rebeccajr/color-clock/docs/imgs/circuit/mux-examples__2024-06-23.pdf

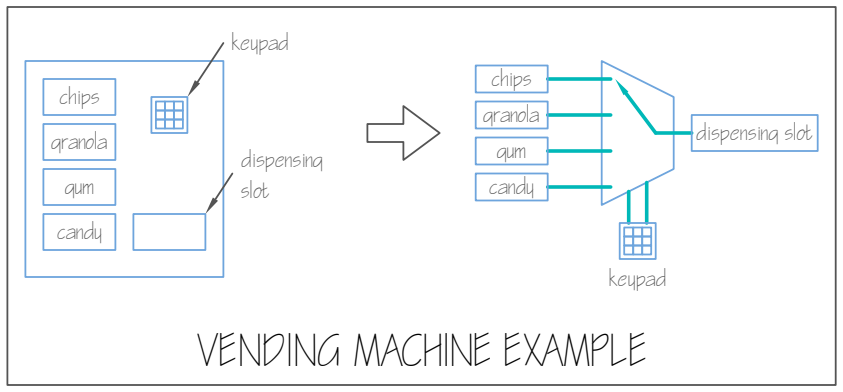
[picture p3: figure]
chips; granola; gum; candy; keypad; dispensing slot; chips granola gum candy; keypad VENDING MACHINE EXAMPLE

Arduino
control signals
common output pin | R
| G B

LED terminals

# RGB LED EXAMPLE
