rebeccajr/color-clock/docs/imgs/participant-ctrl/participant-ctrl-enclosure__2024-07-13.pdf

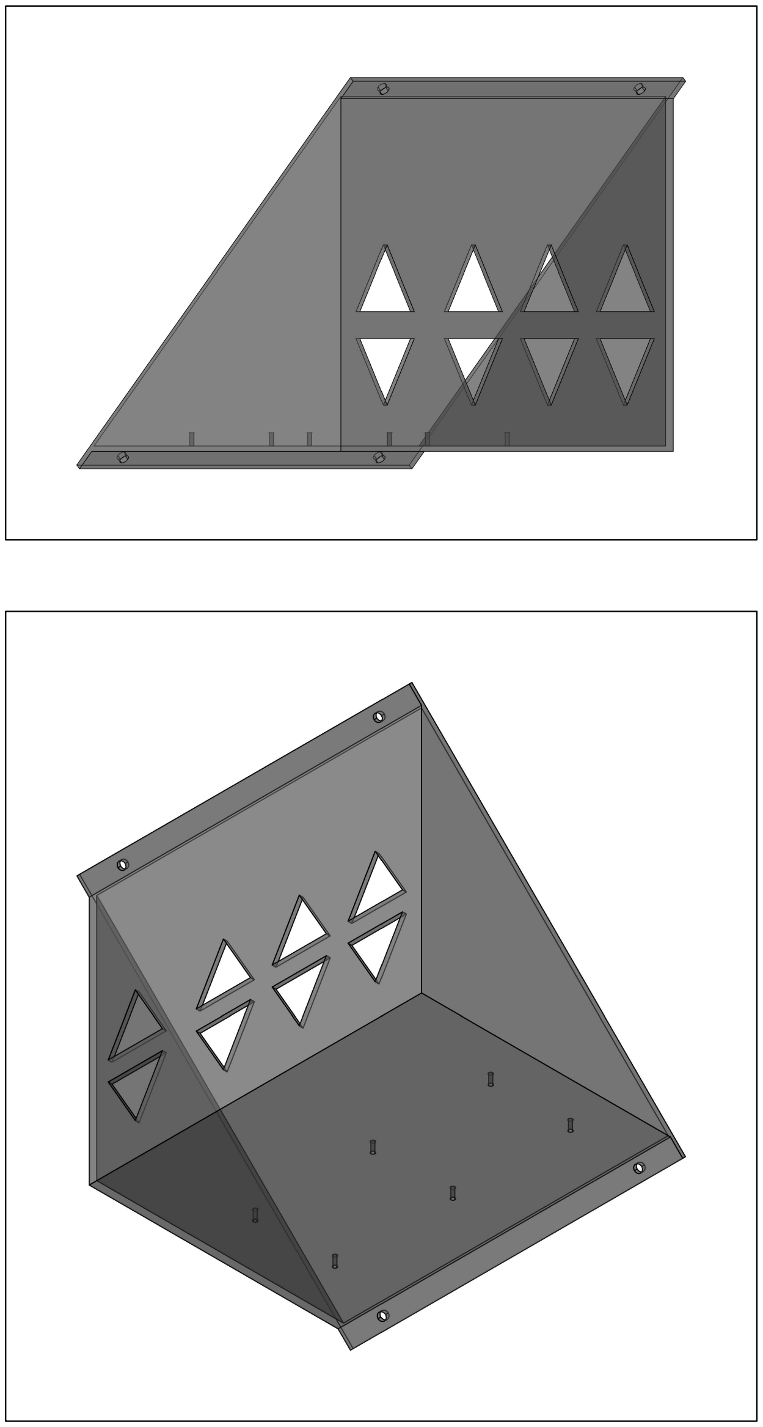
[picture p4: page 1]
