rebeccajr/color-clock/docs/imgs/participant-ctrl/participant-intfc__2024-07-04.pdf

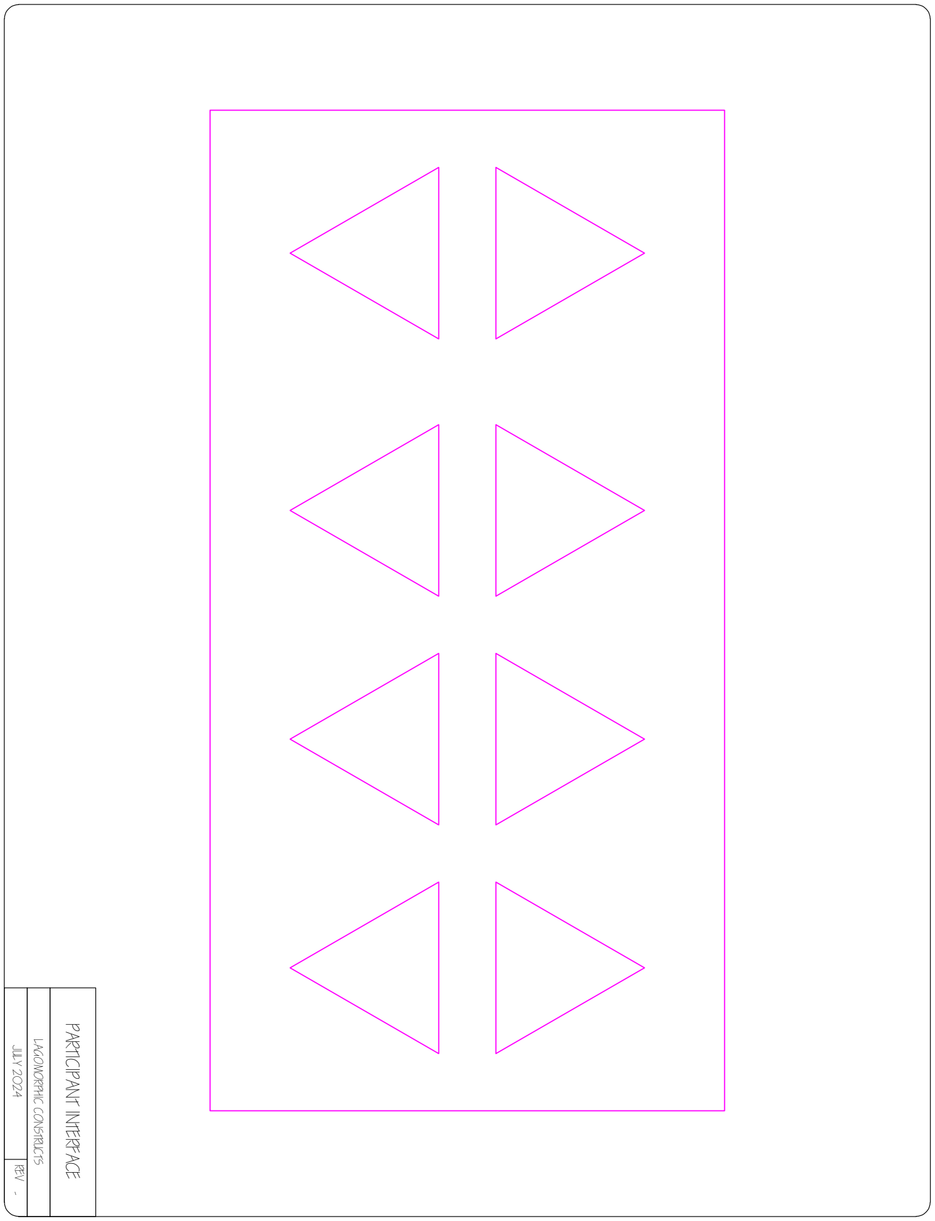
[picture p5: figure]

REV LAGOMORPHIC CONSTRUCTS - JULY 2024 PARTICIPANT INTERFACE
