rebeccajr/color-clock/docs/datasheets/Common-Anode-Singal-Input.jpg

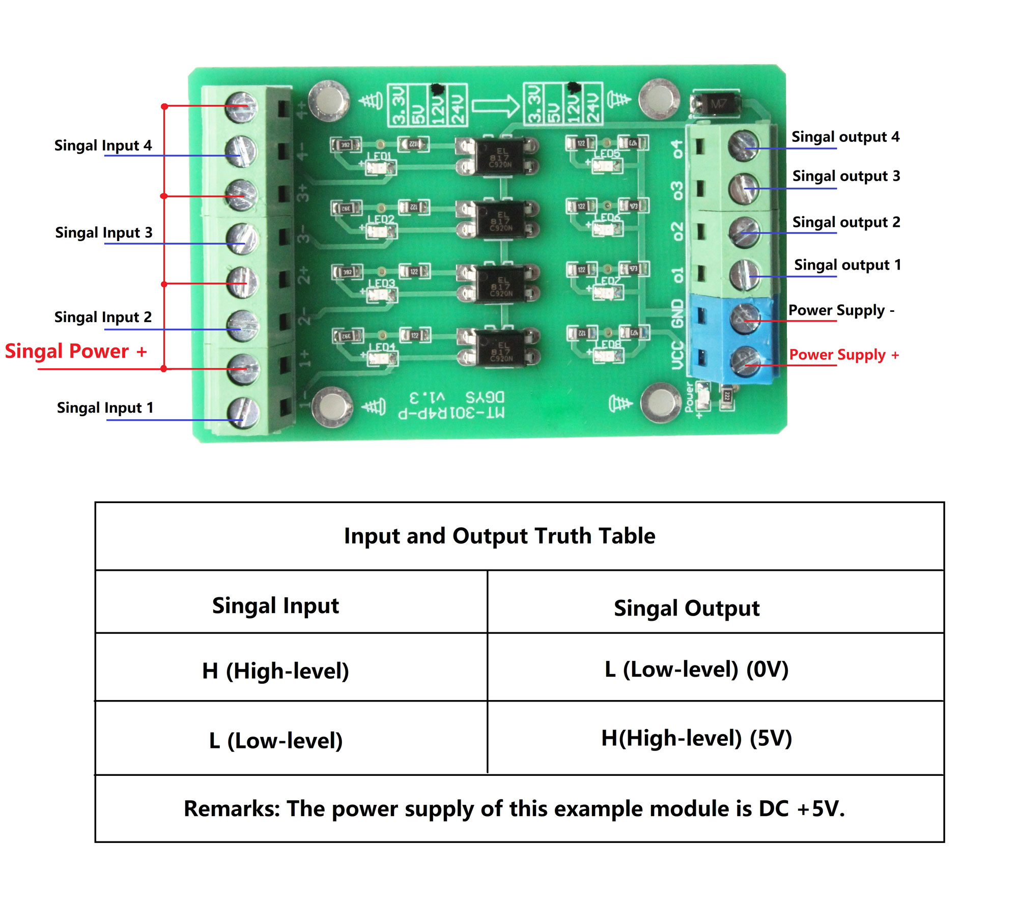
docs/datasheets/Common-Anode-Singal-Input.jpg
