rebeccajr/color-clock/docs/datasheets/Common-Cathode-Singal-Input.jpg

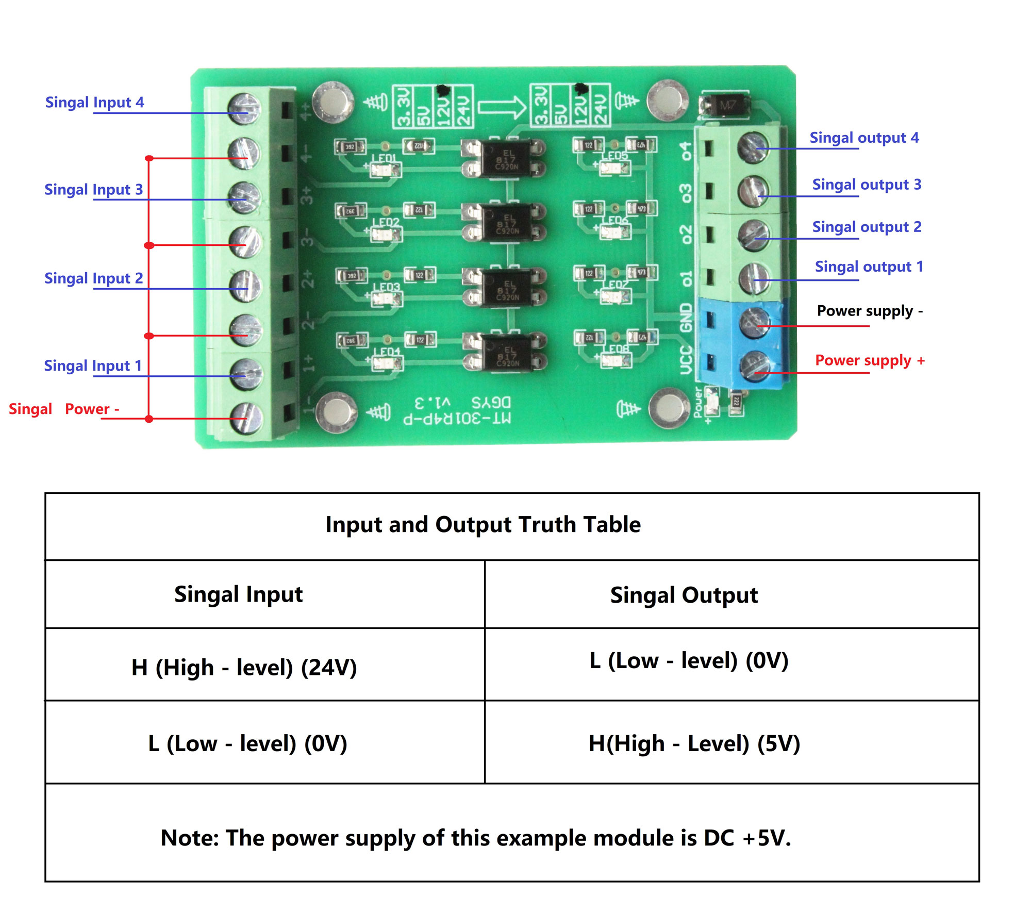
docs/datasheets/Common-Cathode-Singal-Input.jpg
