rebeccajr/color-clock/docs/imgs/block-diagrams/color-clock-block.png

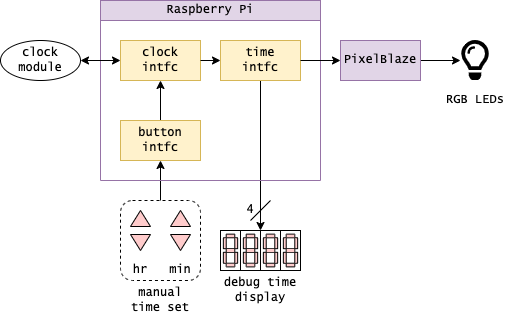
docs/imgs/block-diagrams/color-clock-block.png
