rebeccajr/color-clock/docs/imgs/block-diagrams/color-clock-block_2022-04.png

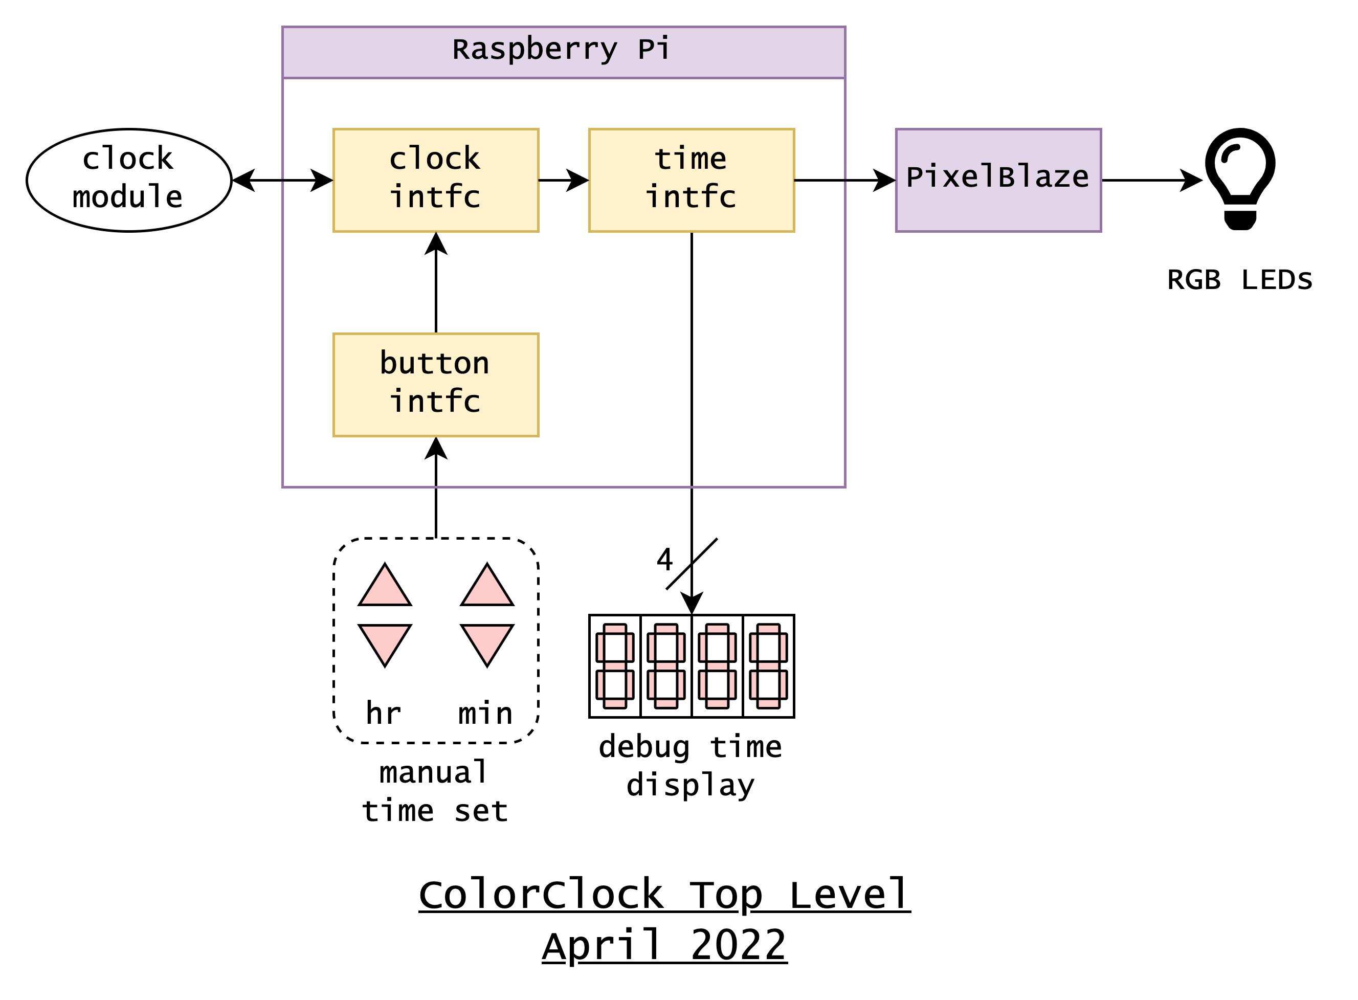
docs/imgs/block-diagrams/color-clock-block_2022-04.png
