rebeccajr/color-clock/docs/imgs/block-diagrams/color-clock-block_2024-02-03.png

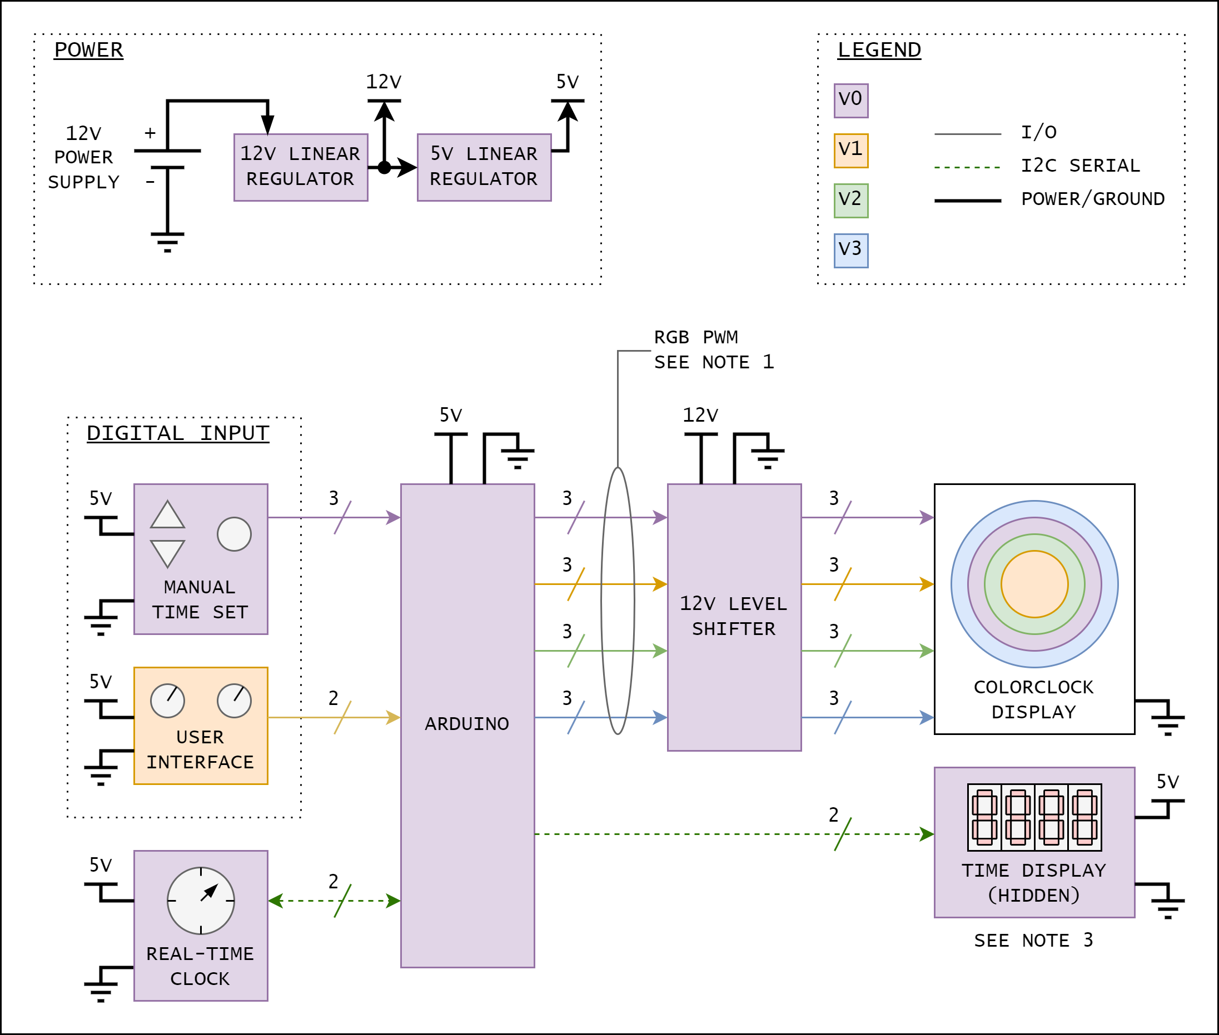
docs/imgs/block-diagrams/color-clock-block_2024-02-03.png
