rebeccajr/color-clock/docs/imgs/circuit/circuit-board-full__2024-07-20.png

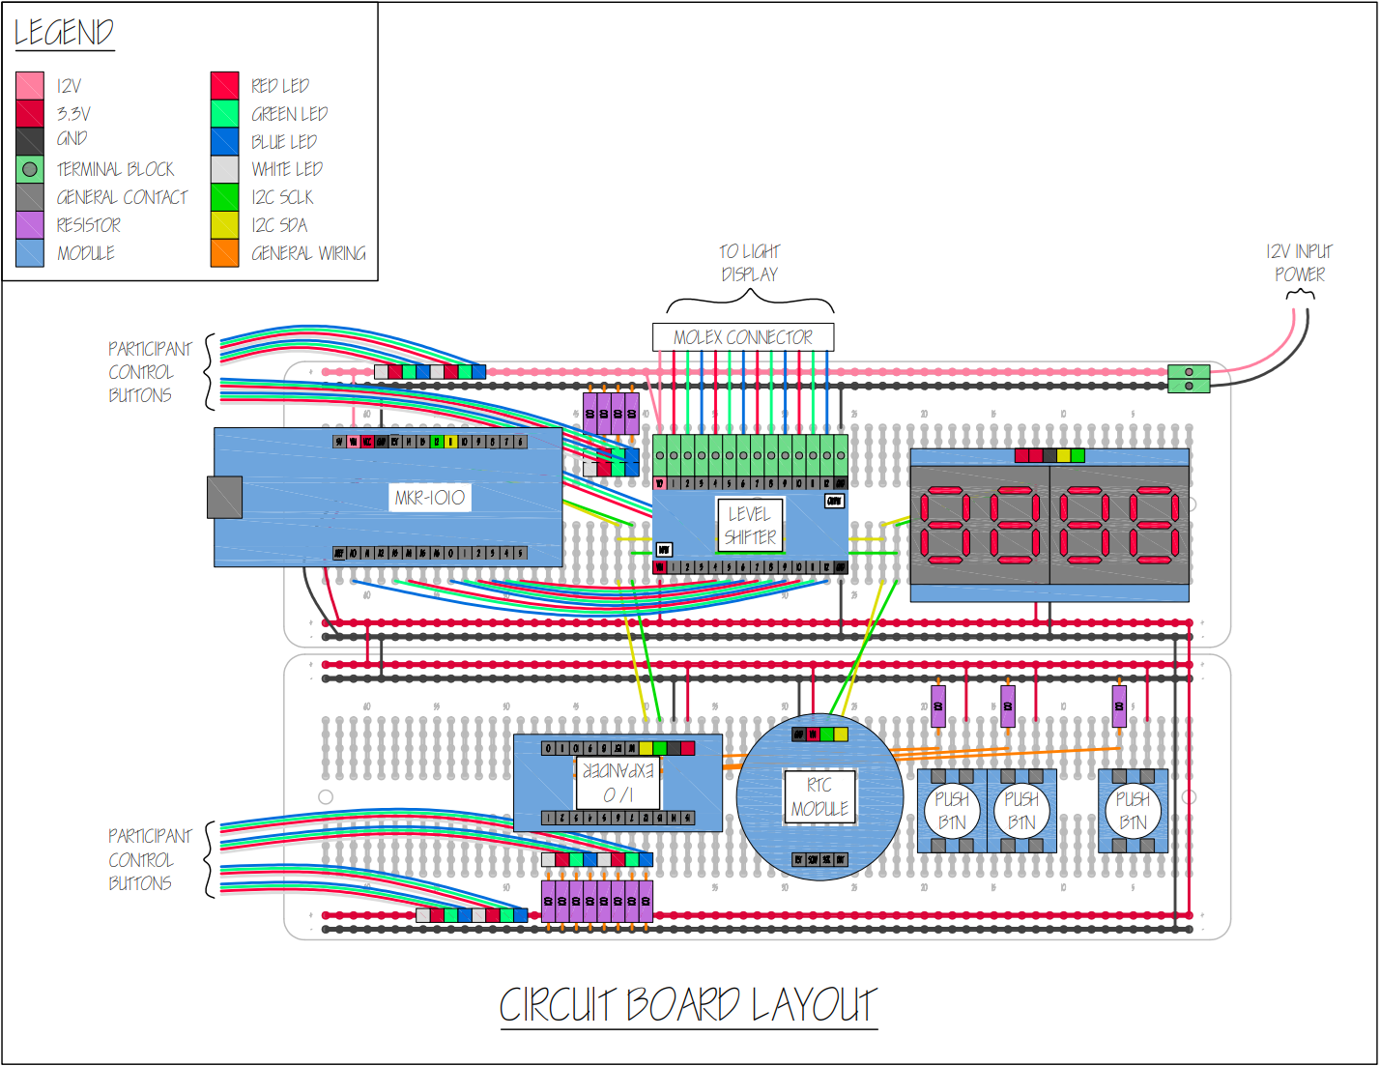
docs/imgs/circuit/circuit-board-full__2024-07-20.png
