rebeccajr/color-clock/docs/imgs/circuit/circuit-board-wire__2024-07-20.png

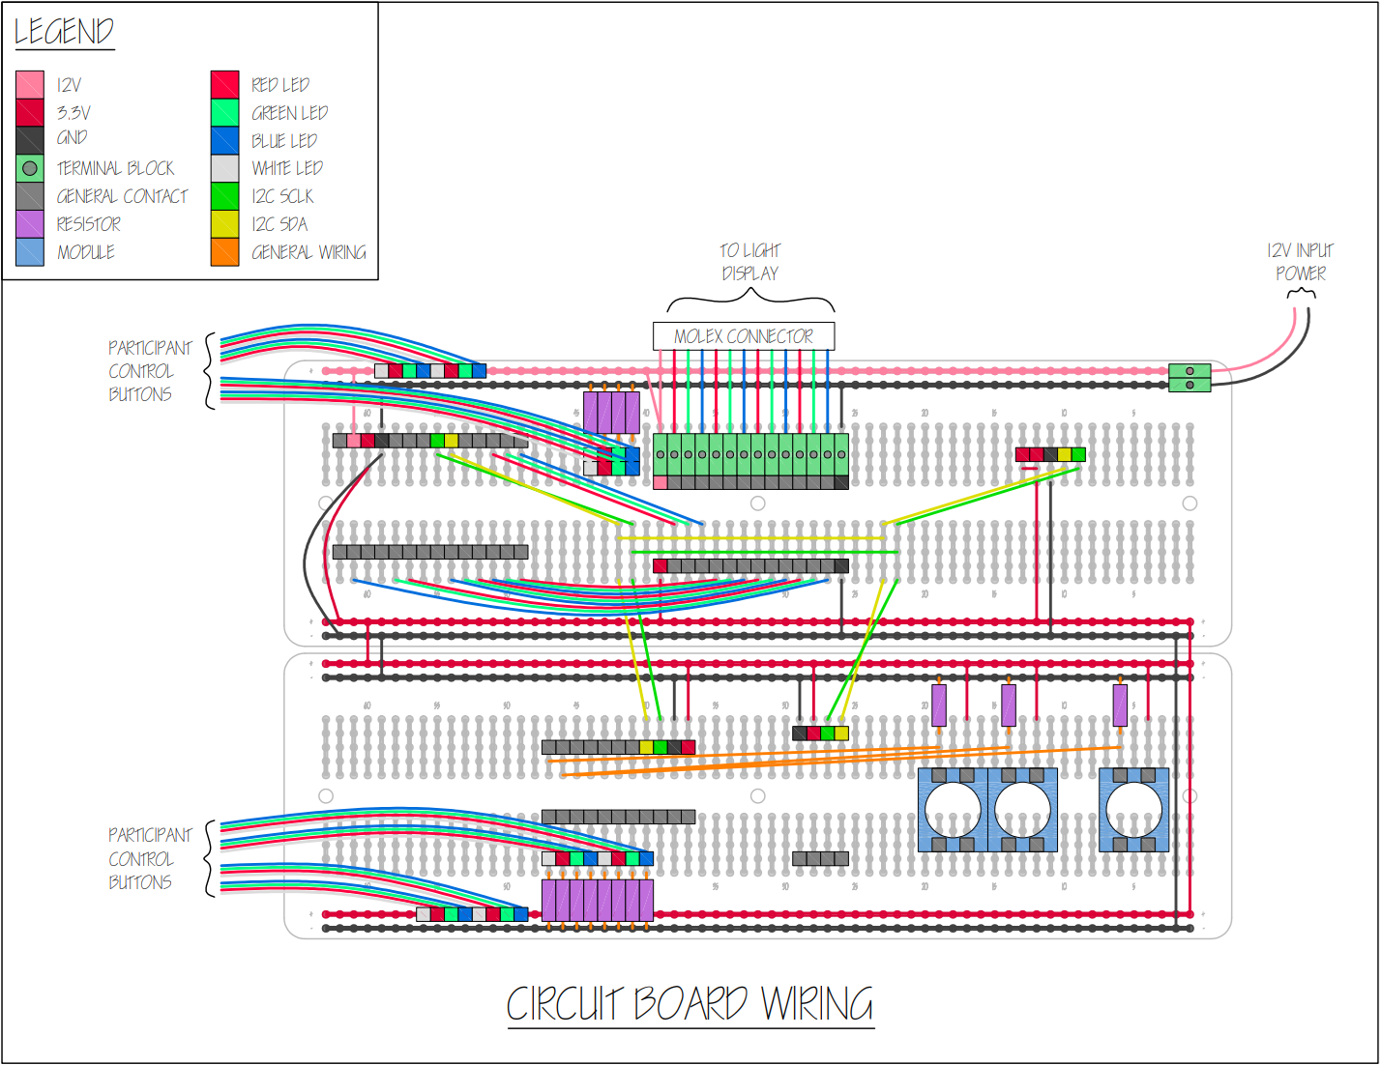
docs/imgs/circuit/circuit-board-wire__2024-07-20.png
