rebeccajr/color-clock/docs/imgs/circuit/color-clock-circuit_2022-05-15.png

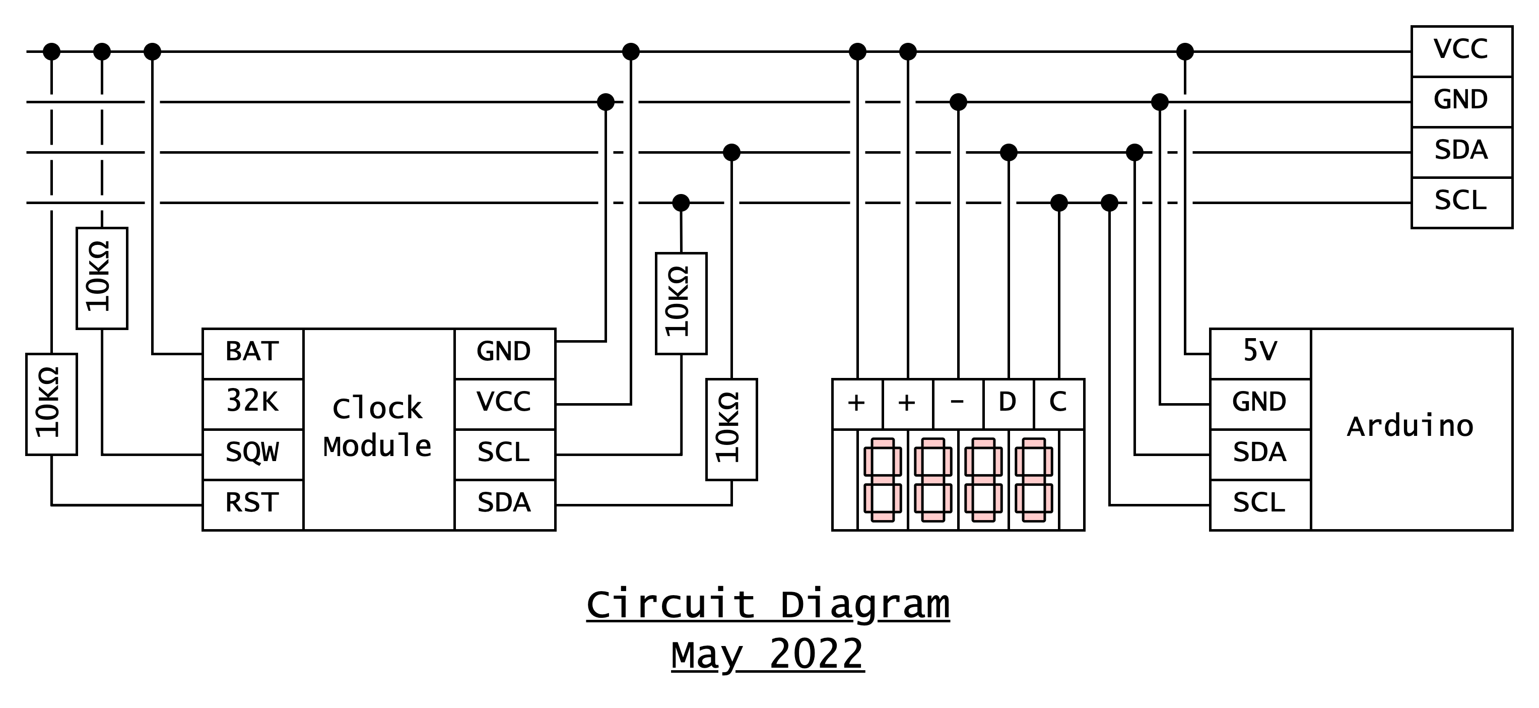
docs/imgs/circuit/color-clock-circuit_2022-05-15.png
