rebeccajr/color-clock/docs/imgs/circuit/mux-rgb__2024-06-23.png

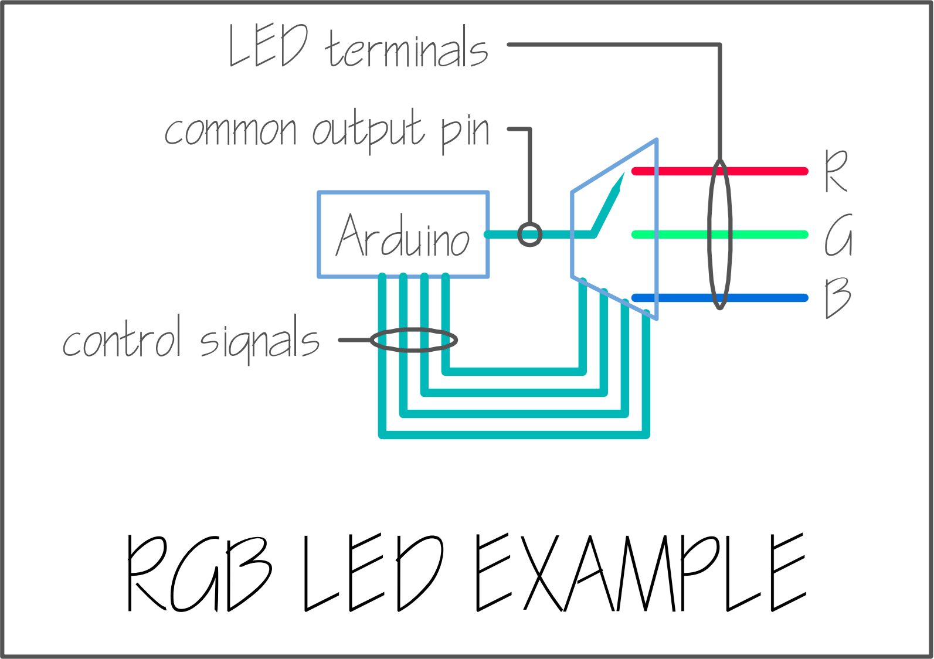
docs/imgs/circuit/mux-rgb__2024-06-23.png
