rebeccajr/color-clock/docs/imgs/circuit/mux-vending-machine__2024-06-23.png

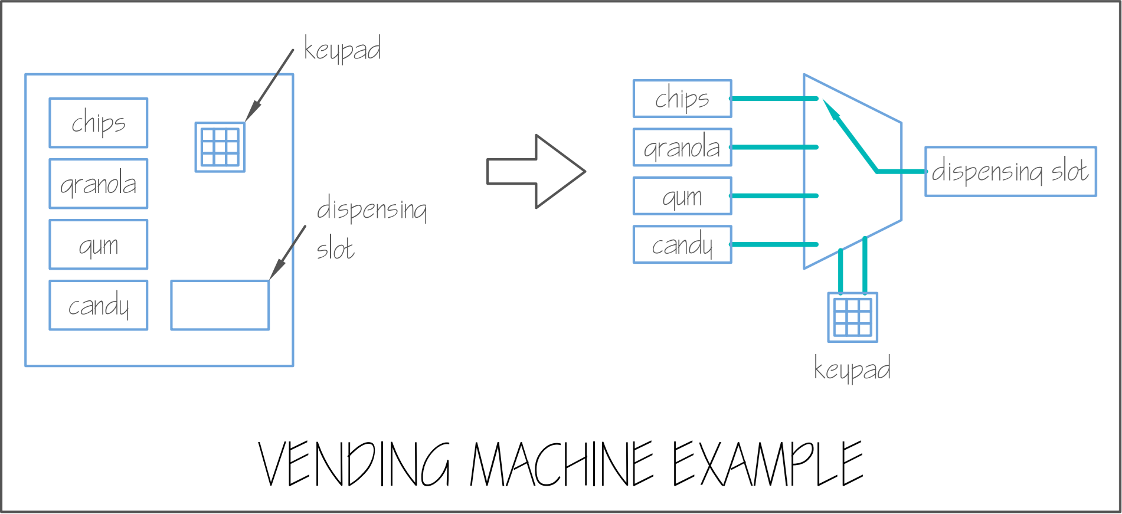
docs/imgs/circuit/mux-vending-machine__2024-06-23.png
