rebeccajr/color-clock/docs/imgs/light-display/light-display-v02_2024-03-06.png

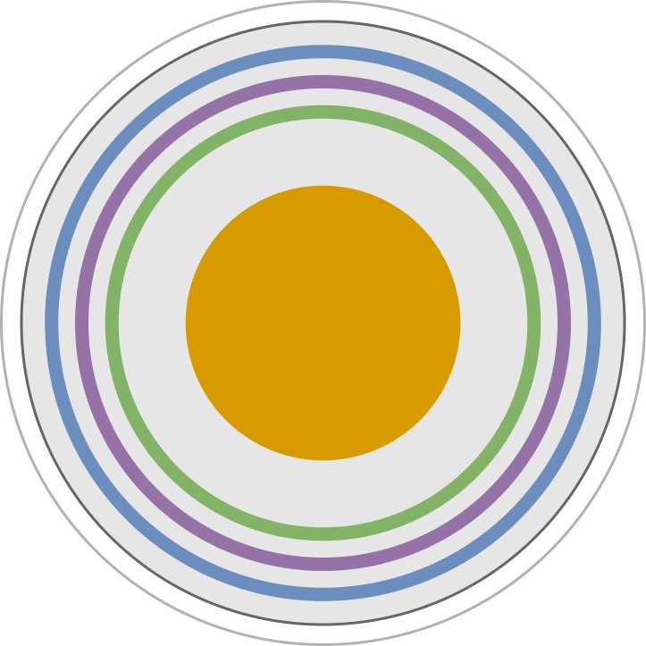
docs/imgs/light-display/light-display-v02_2024-03-06.png
