rebeccajr/color-clock/docs/imgs/light-display/light-display_2024-02-23.png

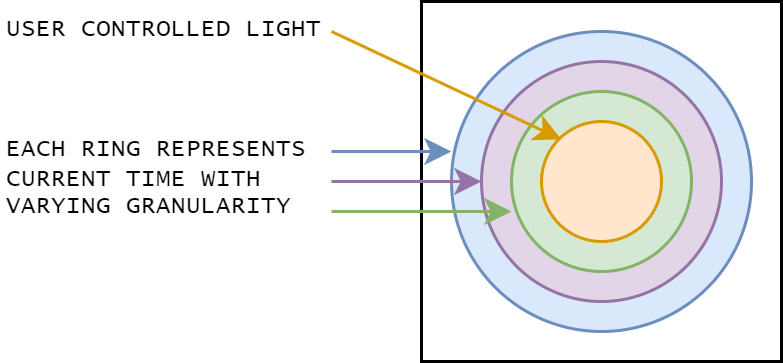
docs/imgs/light-display/light-display_2024-02-23.png
