rebeccajr/color-clock/docs/imgs/other/ascii-bunny.png

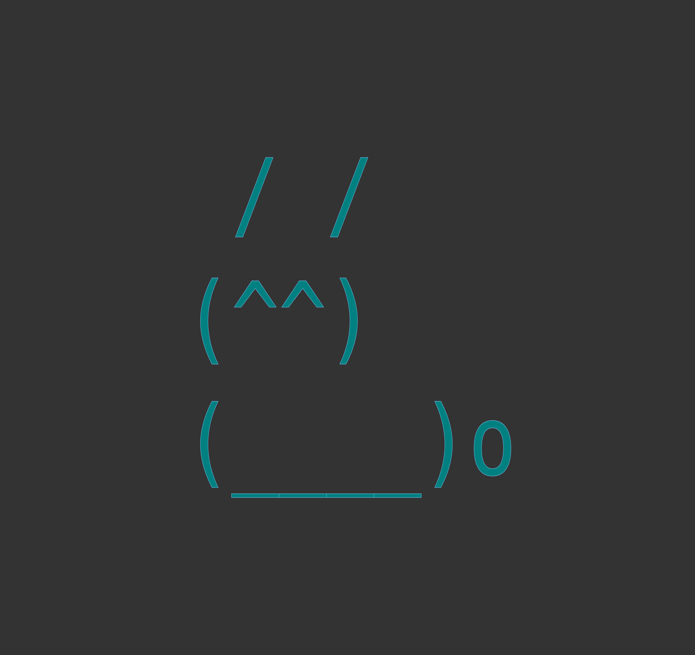
docs/imgs/other/ascii-bunny.png
