rebeccajr/color-clock/docs/imgs/participant-ctrl/participant-ctrl-0__2024-07-13.png

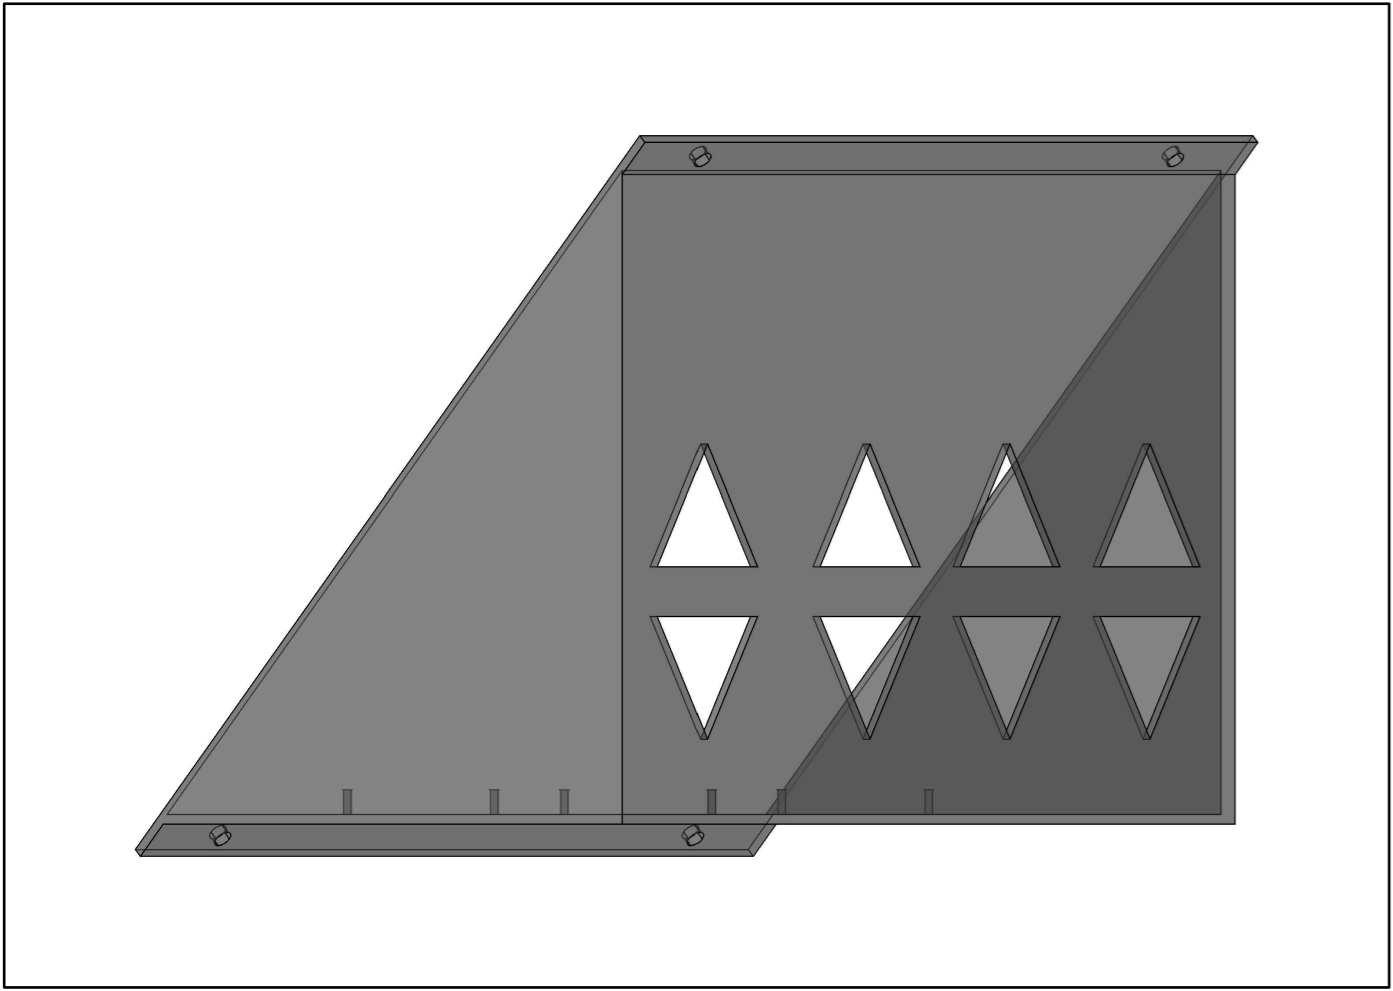
docs/imgs/participant-ctrl/participant-ctrl-0__2024-07-13.png
