rebeccajr/color-clock/docs/imgs/participant-ctrl/user-interface-v2_2024-02-23.png

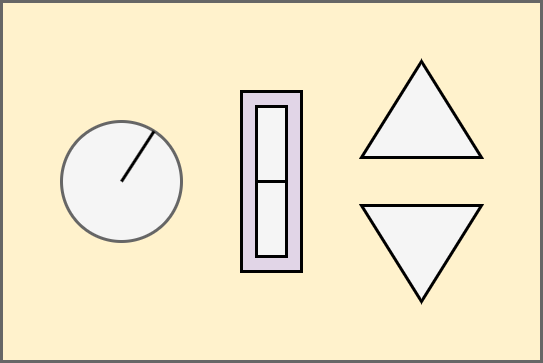
docs/imgs/participant-ctrl/user-interface-v2_2024-02-23.png
