rebeccajr/color-clock/docs/imgs/participant-ctrl/user-interface-v3_2024-02-23.png

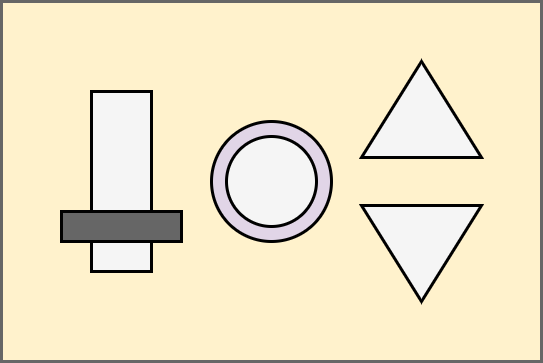
docs/imgs/participant-ctrl/user-interface-v3_2024-02-23.png
