rebeccajr/color-clock/docs/imgs/photos/IMG_2031.JPEG

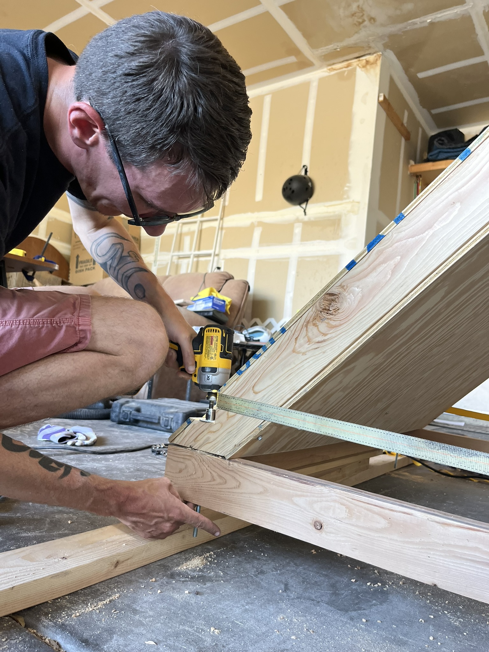
docs/imgs/photos/IMG_2031.JPEG
