rebeccajr/color-clock/docs/imgs/photos/IMG_2035.JPEG

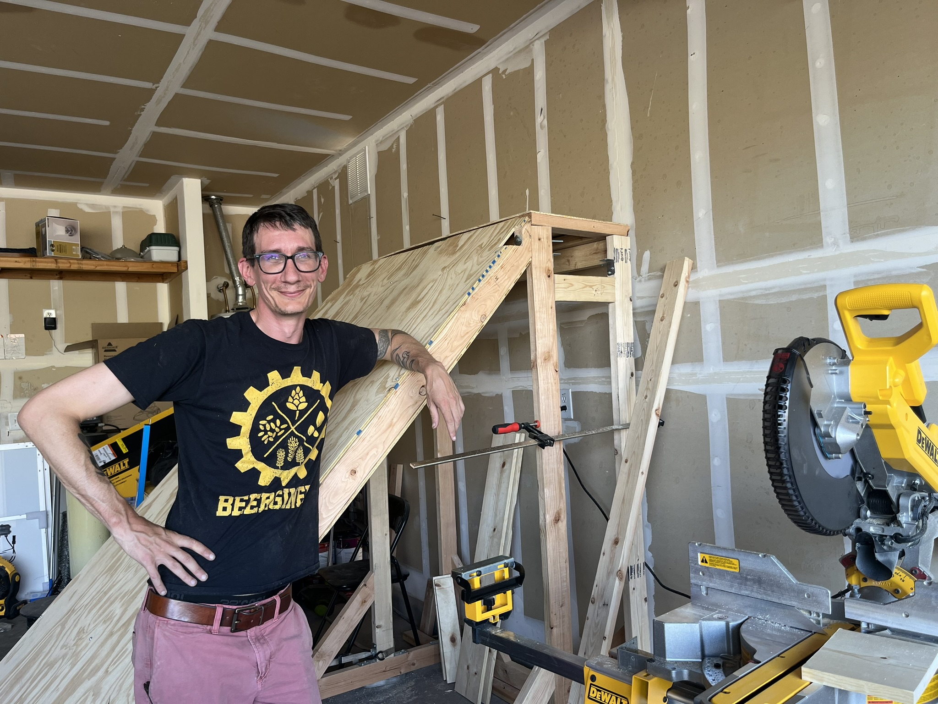
docs/imgs/photos/IMG_2035.JPEG
