rebeccajr/color-clock/docs/imgs/photos/IMG_2041.JPEG

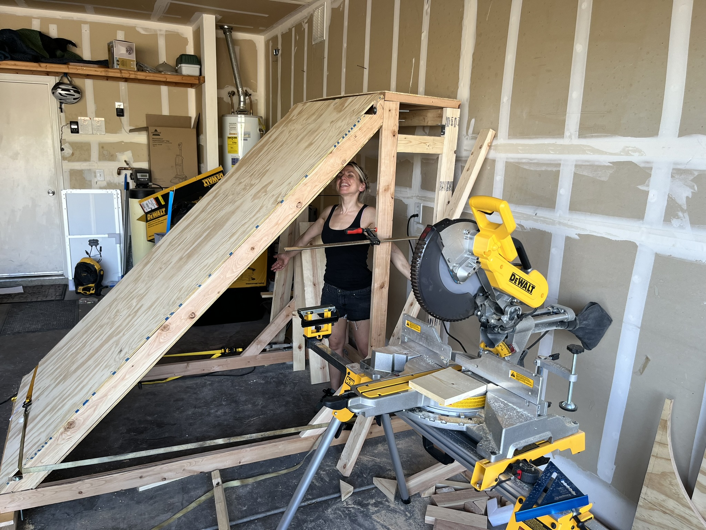
docs/imgs/photos/IMG_2041.JPEG
