rebeccajr/color-clock/docs/imgs/photos/IMG_2043.JPEG

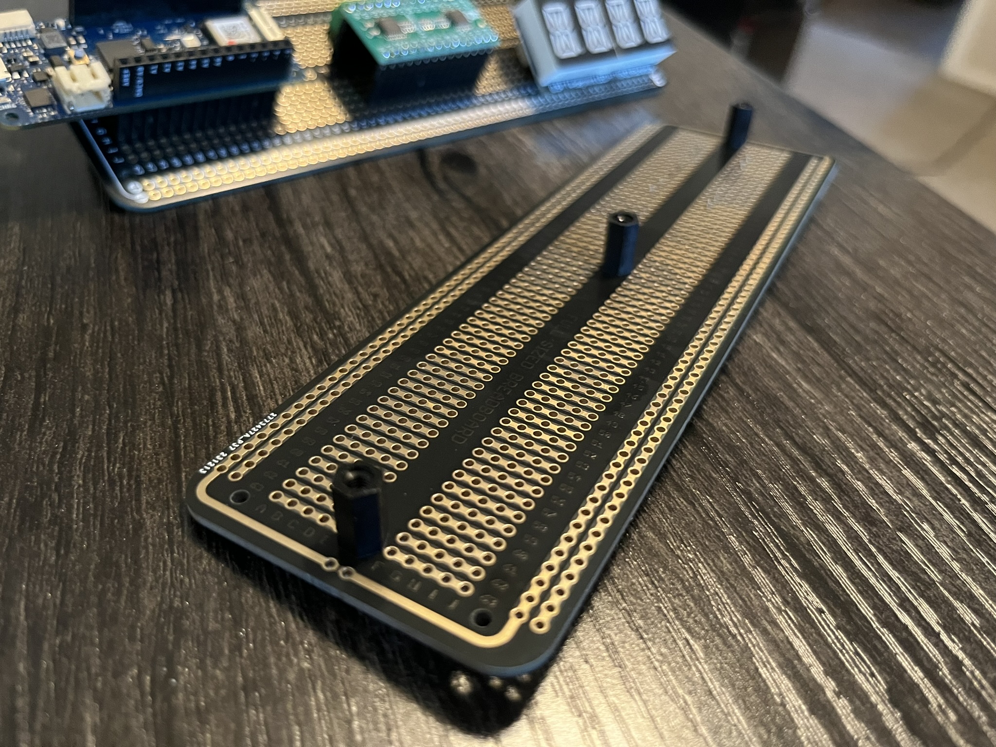
docs/imgs/photos/IMG_2043.JPEG
