rebeccajr/color-clock/docs/imgs/photos/structure-v1-photo_2024-03-02.jpg

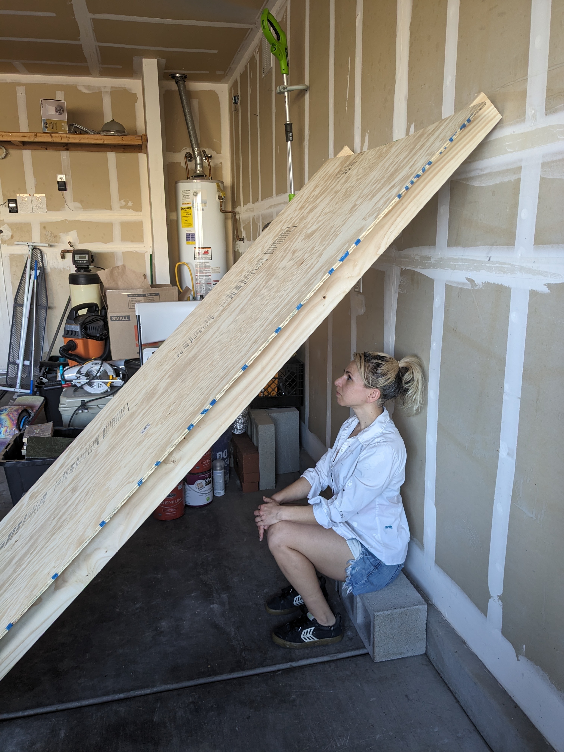
docs/imgs/photos/structure-v1-photo_2024-03-02.jpg
