rebeccajr/color-clock/docs/imgs/photos/time-display_2024-03-20.jpg

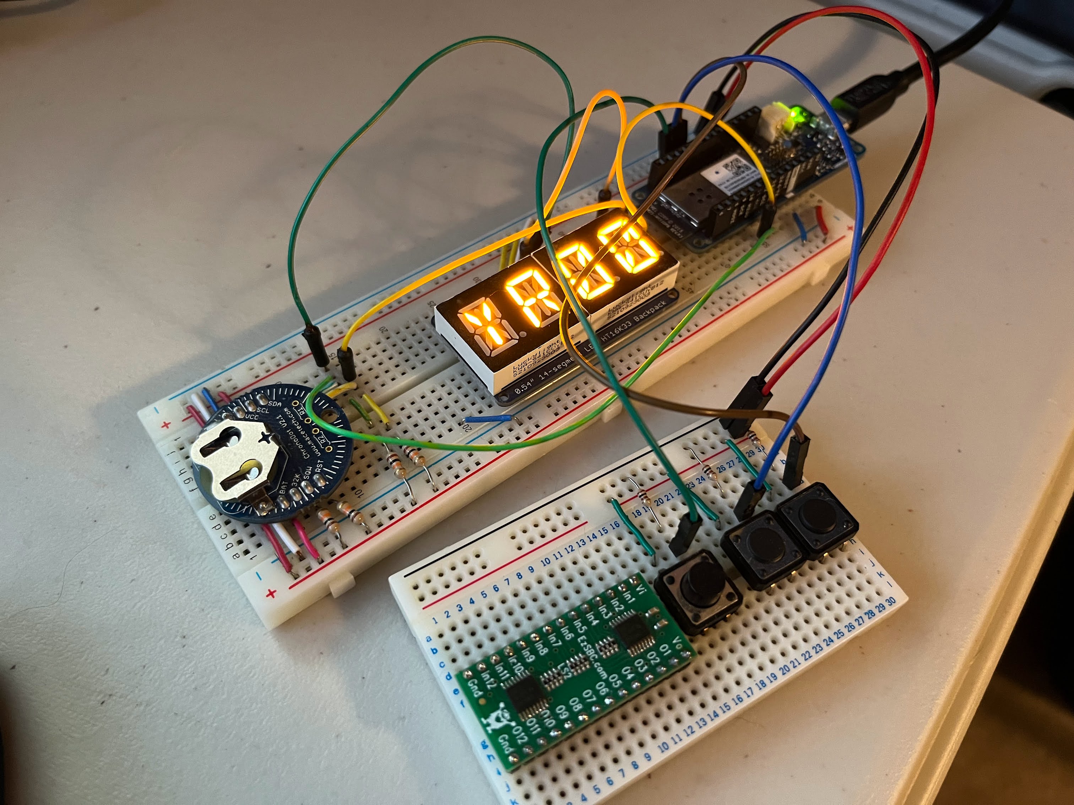
docs/imgs/photos/time-display_2024-03-20.jpg
