rebeccajr/color-clock/docs/imgs/structure/color-clock-overall-v02__2024-03-06.jpg

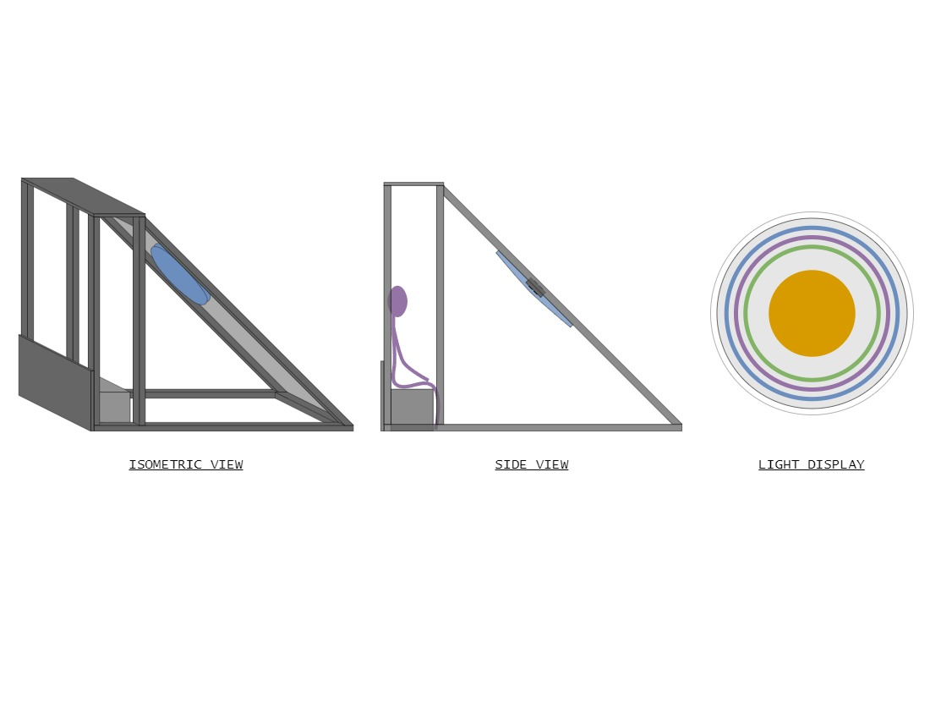
docs/imgs/structure/color-clock-overall-v02__2024-03-06.jpg
