rebeccajr/color-clock/docs/imgs/structure/color-clock-physical-structure-v0.jpg

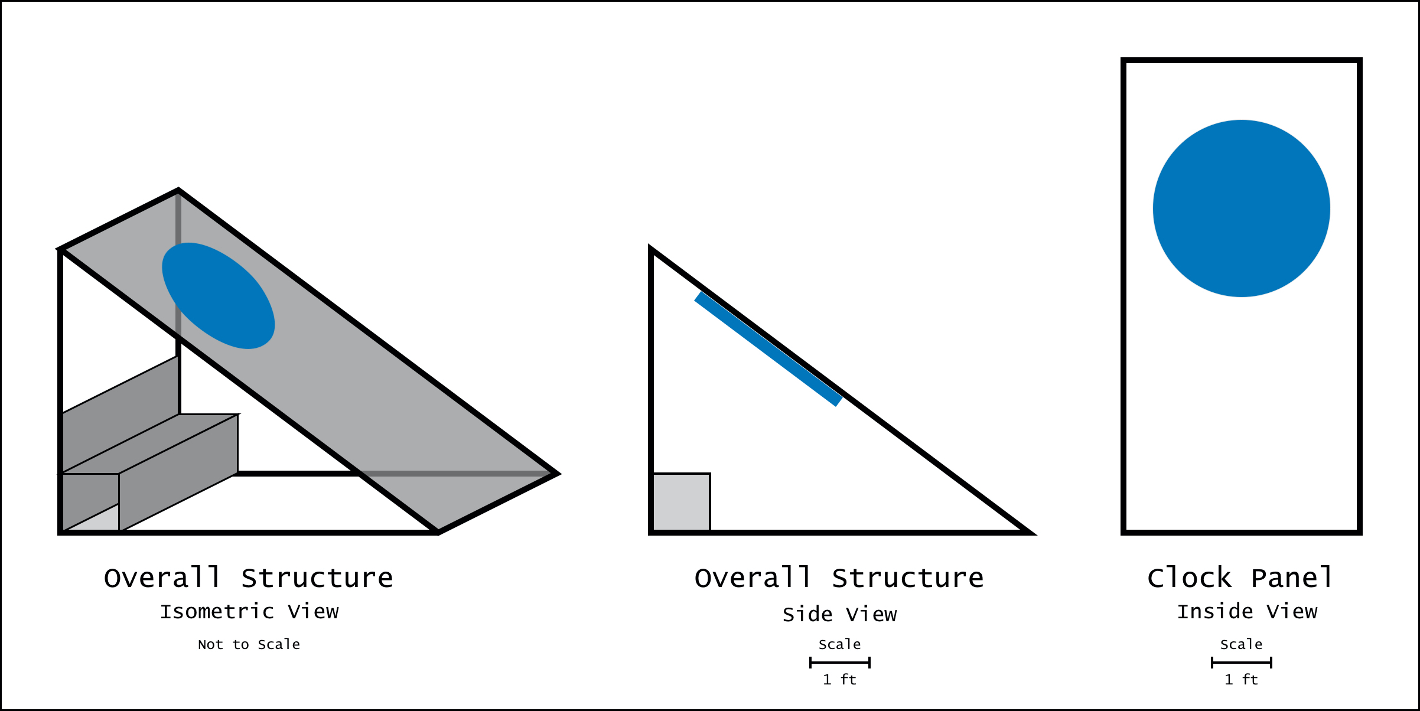
docs/imgs/structure/color-clock-physical-structure-v0.jpg
