rebeccajr/color-clock/docs/imgs/structure/structure-v2-cad_2024-03-06.png

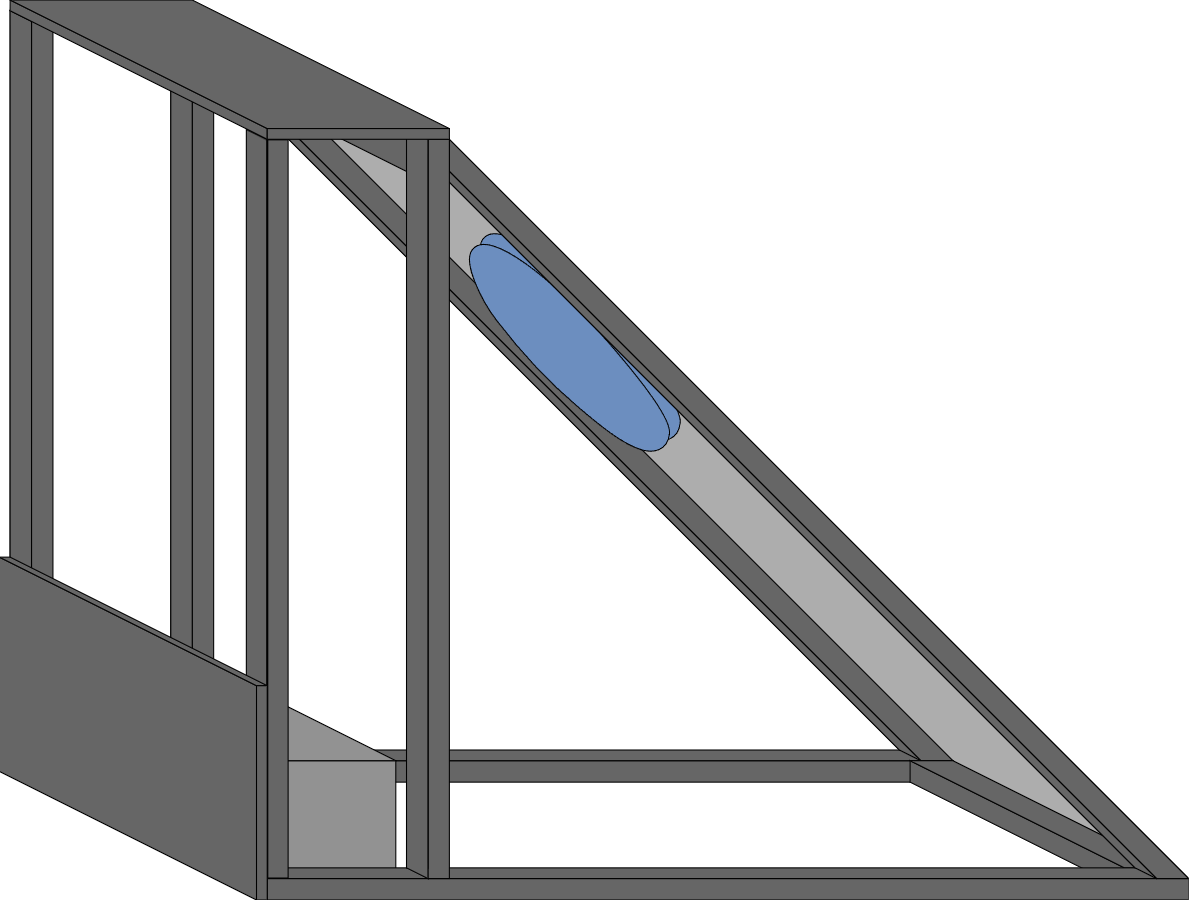
docs/imgs/structure/structure-v2-cad_2024-03-06.png
