rebeccajr/color-clock/docs/imgs/structure/structure-v2-sketch_2024-03-20.png

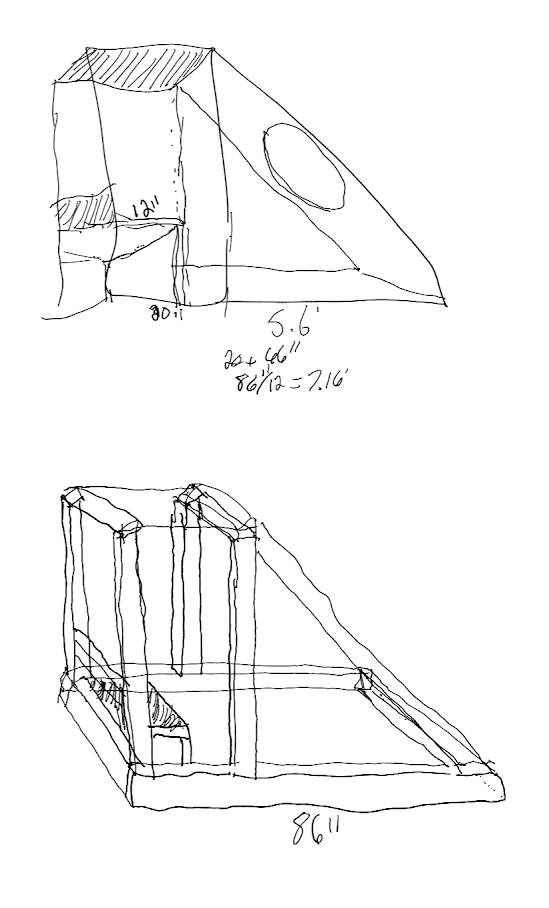
docs/imgs/structure/structure-v2-sketch_2024-03-20.png
