rebeccajr/color-clock/docs/slide-decks/2024-08-10__demo/_photos-demo/IMG_2125.jpeg

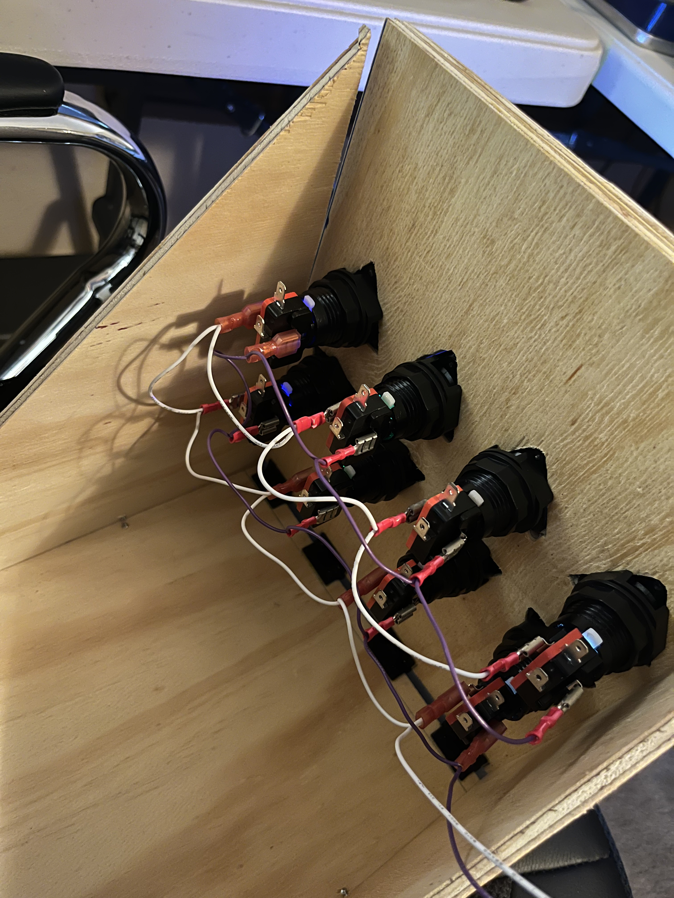
docs/slide-decks/2024-08-10__demo/_photos-demo/IMG_2125.jpeg
