rebeccajr/color-clock/docs/slide-decks/2024-08-10__demo/_png/02__light-color.png

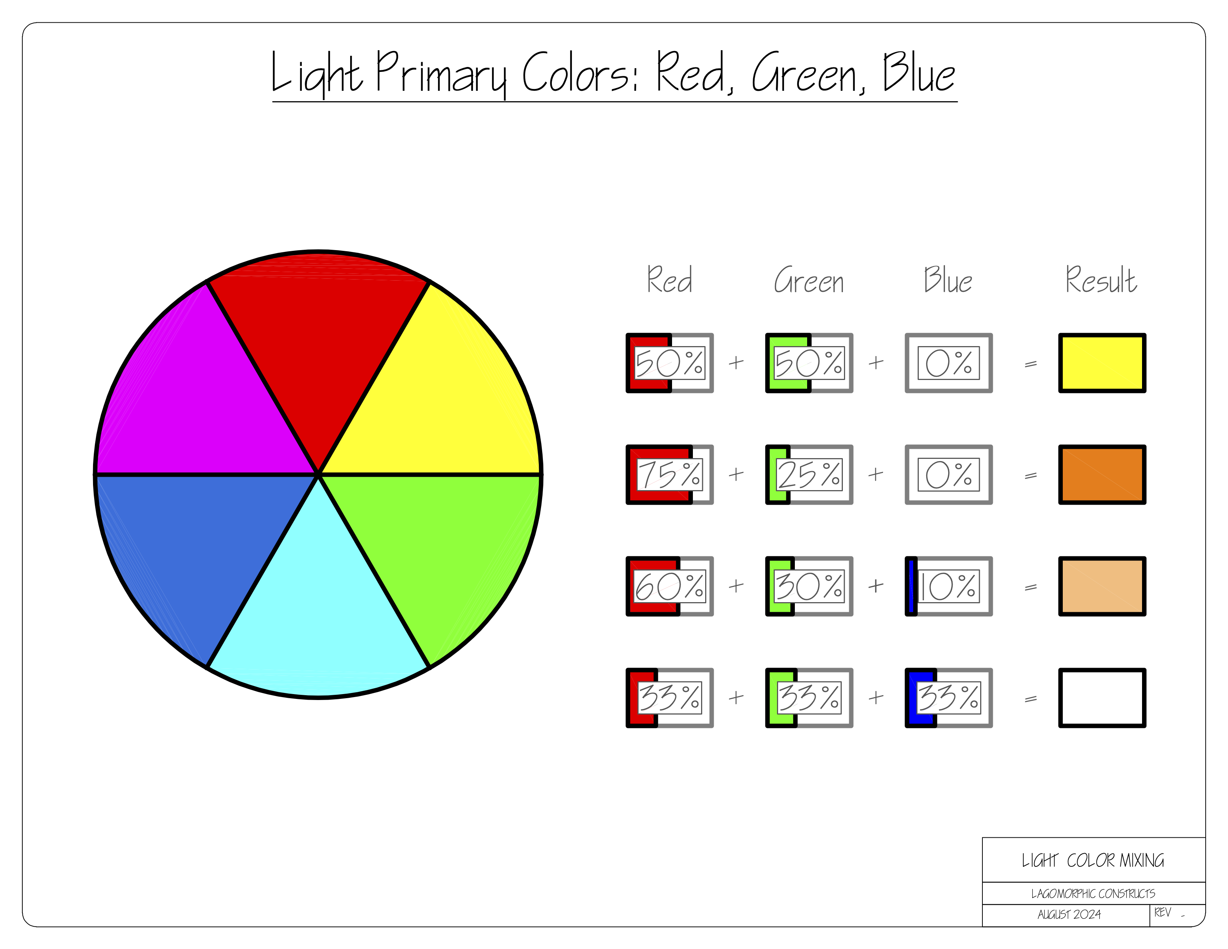
docs/slide-decks/2024-08-10__demo/_png/02__light-color.png
