rebeccajr/color-clock/docs/slide-decks/2024-08-10__demo/_png/03__rgb-led-common-anode.png

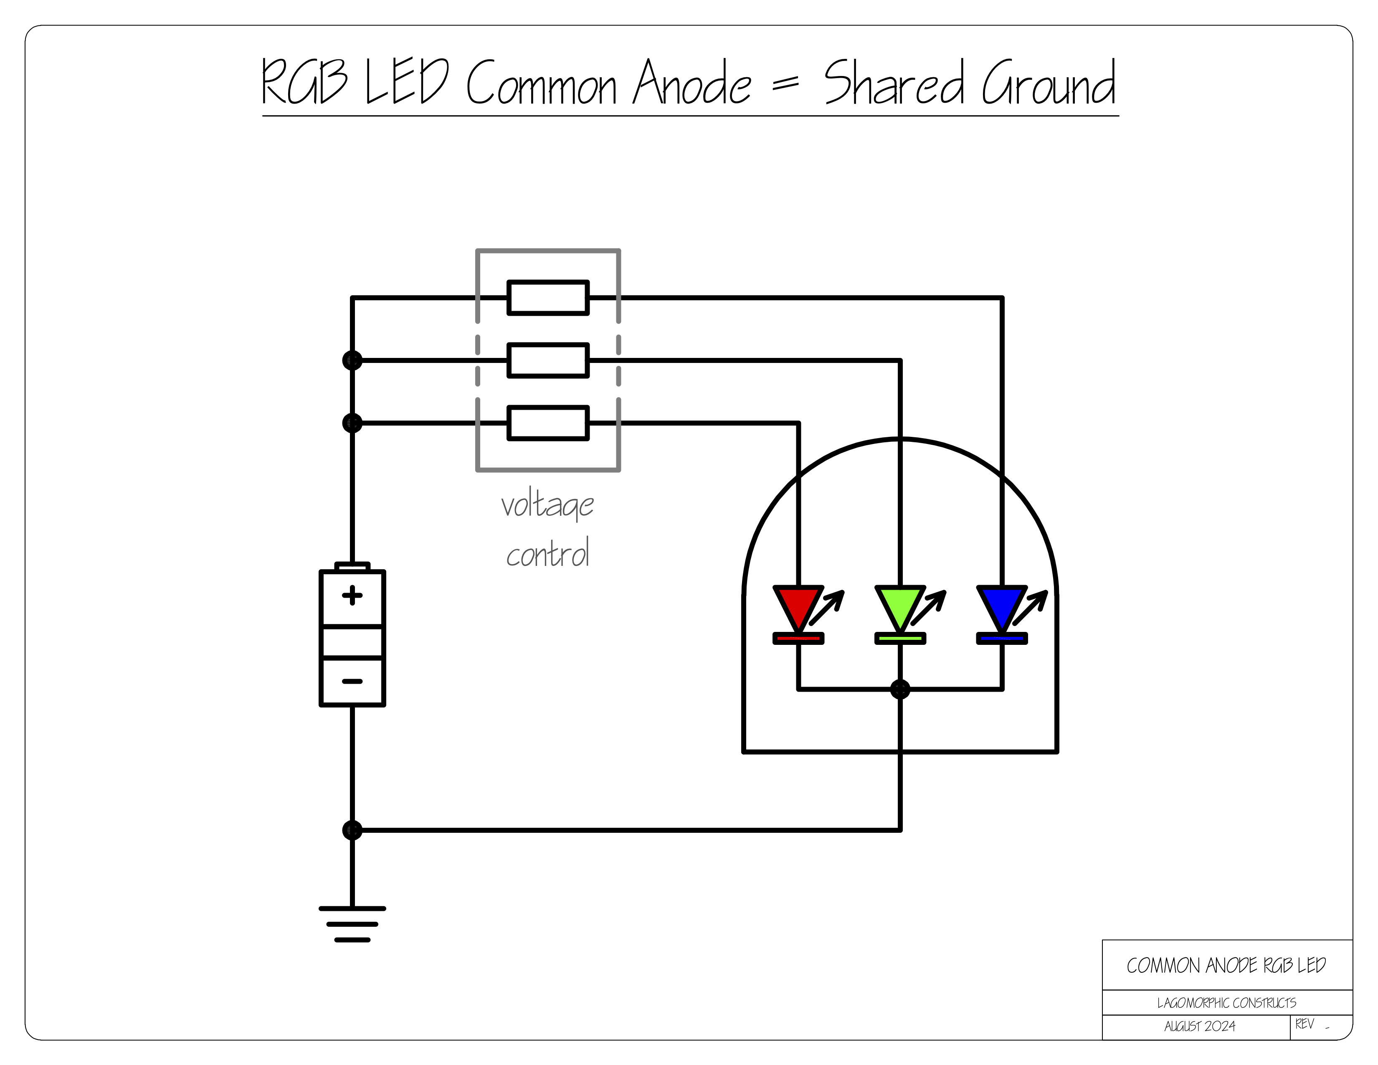
docs/slide-decks/2024-08-10__demo/_png/03__rgb-led-common-anode.png
