rebeccajr/color-clock/docs/slide-decks/2024-08-10__demo/_png/04__rgb-color-mix.png

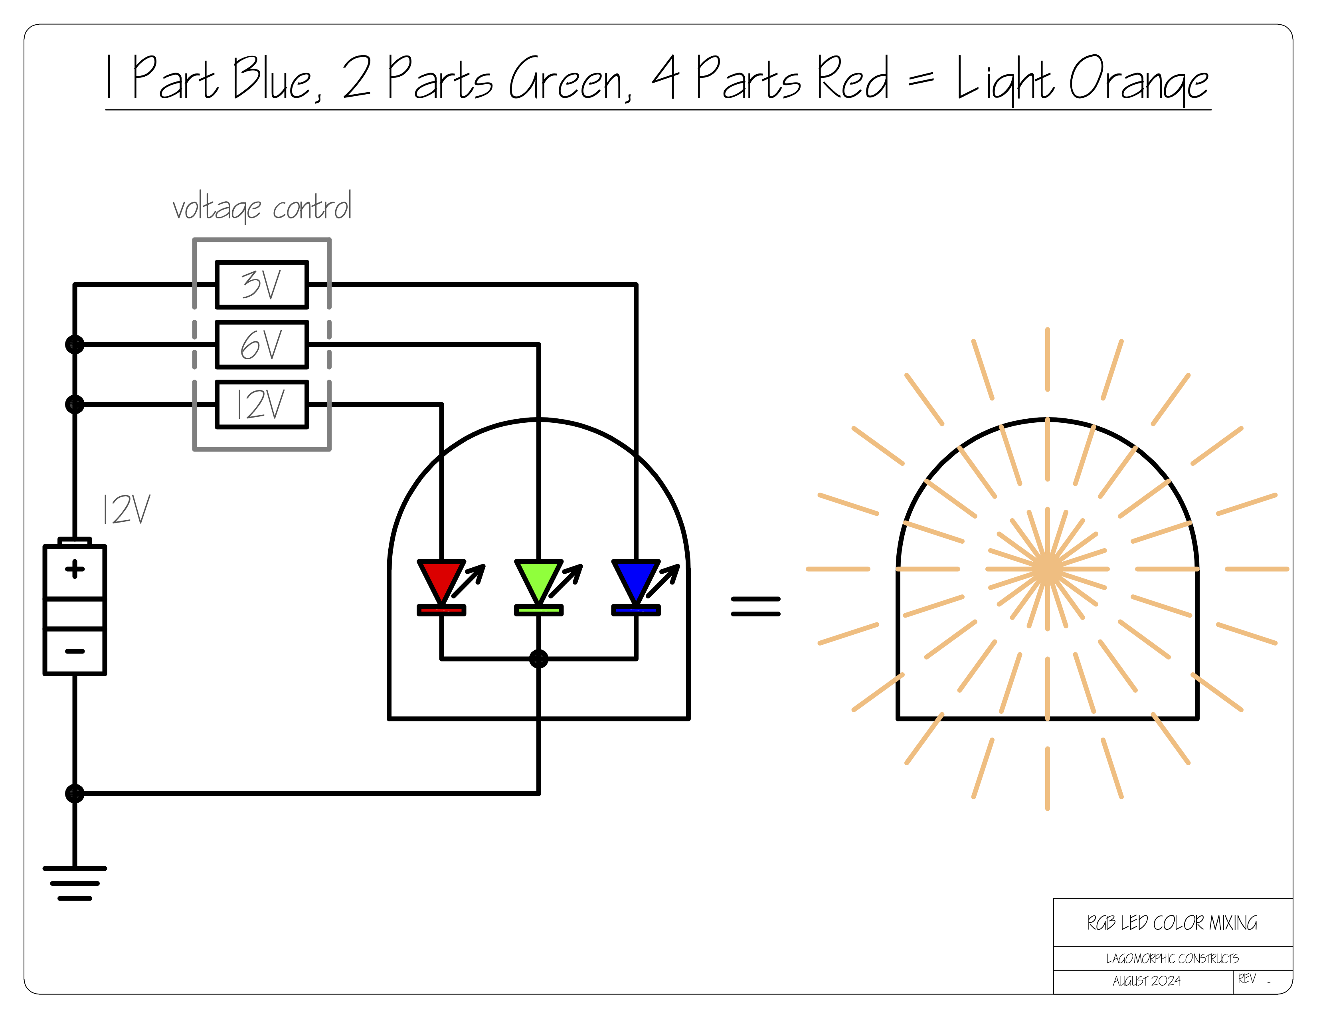
docs/slide-decks/2024-08-10__demo/_png/04__rgb-color-mix.png
