rebeccajr/color-clock/docs/slide-decks/2024-08-10__demo/_png/05__level-shifter.png

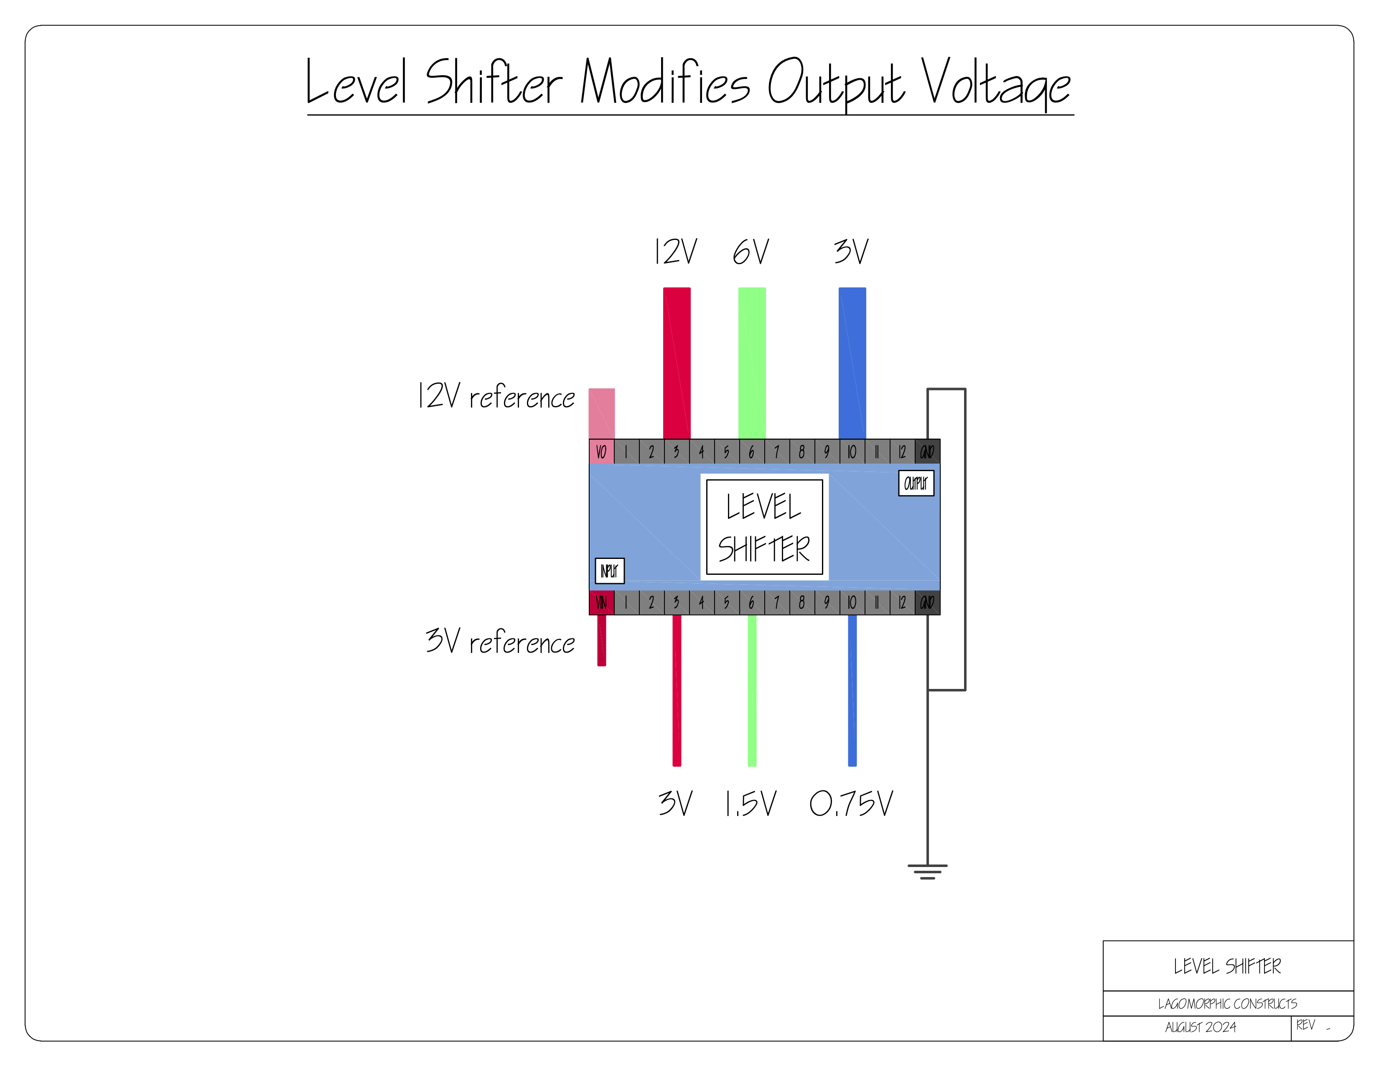
docs/slide-decks/2024-08-10__demo/_png/05__level-shifter.png
