rebeccajr/color-clock/docs/imgs/acad/_stl/box-divider-6in-v0__2024-08-04.stl

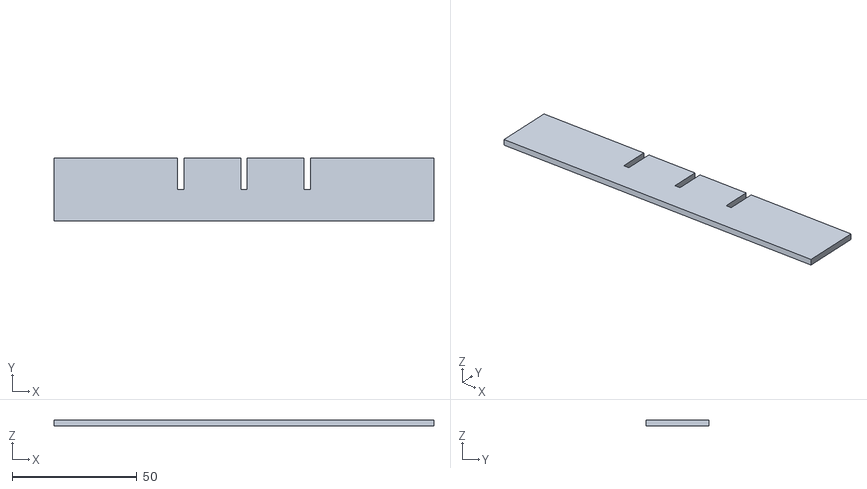
[picture p65: CAD file, 2024-11-28]
docs/imgs/acad/_stl/box-divider-6in-v0__2024-08-04.stl
152.4 x 25.4 x 2.54
