rebeccajr/color-clock/docs/imgs/acad/_stl/enclosure-front-v0__2024-07-29.stl

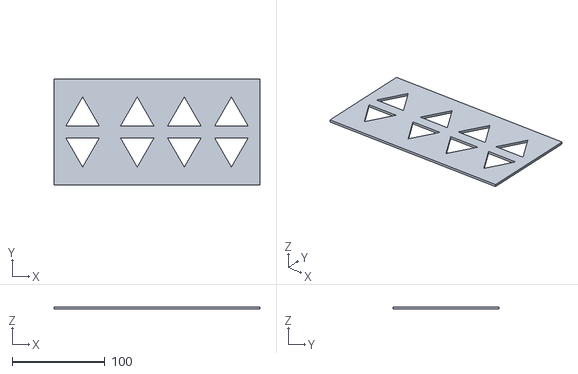
[picture p66: CAD file, 2024-11-28]
docs/imgs/acad/_stl/enclosure-front-v0__2024-07-29.stl
222.2 x 114.3 x 2.54
