rebeccajr/color-clock/docs/imgs/circuit/solderless-breadboard-layout-rev--no-anno__2024-05-28.png

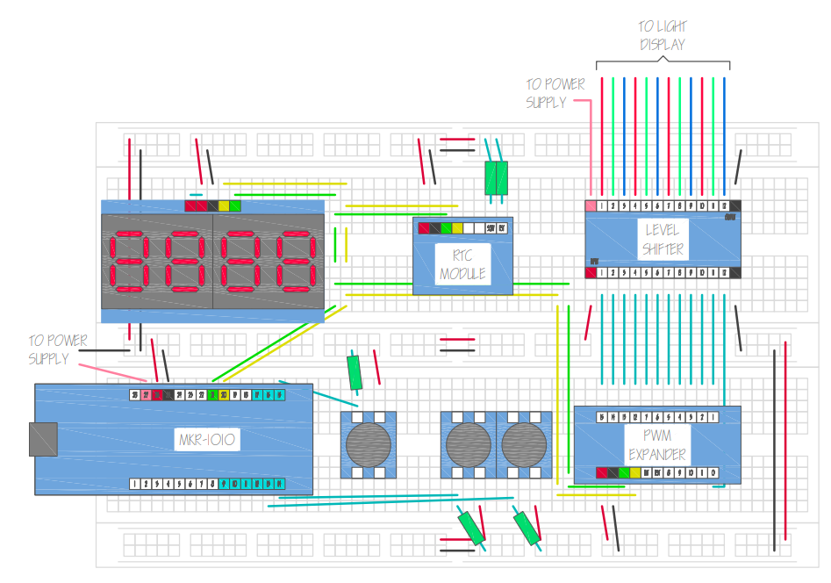
docs/imgs/circuit/solderless-breadboard-layout-rev--no-anno__2024-05-28.png
