rebeccajr/color-clock/docs/imgs/circuit/solderless-breadboard-layout-rev-a-no-anno__2024-05-29.jpg

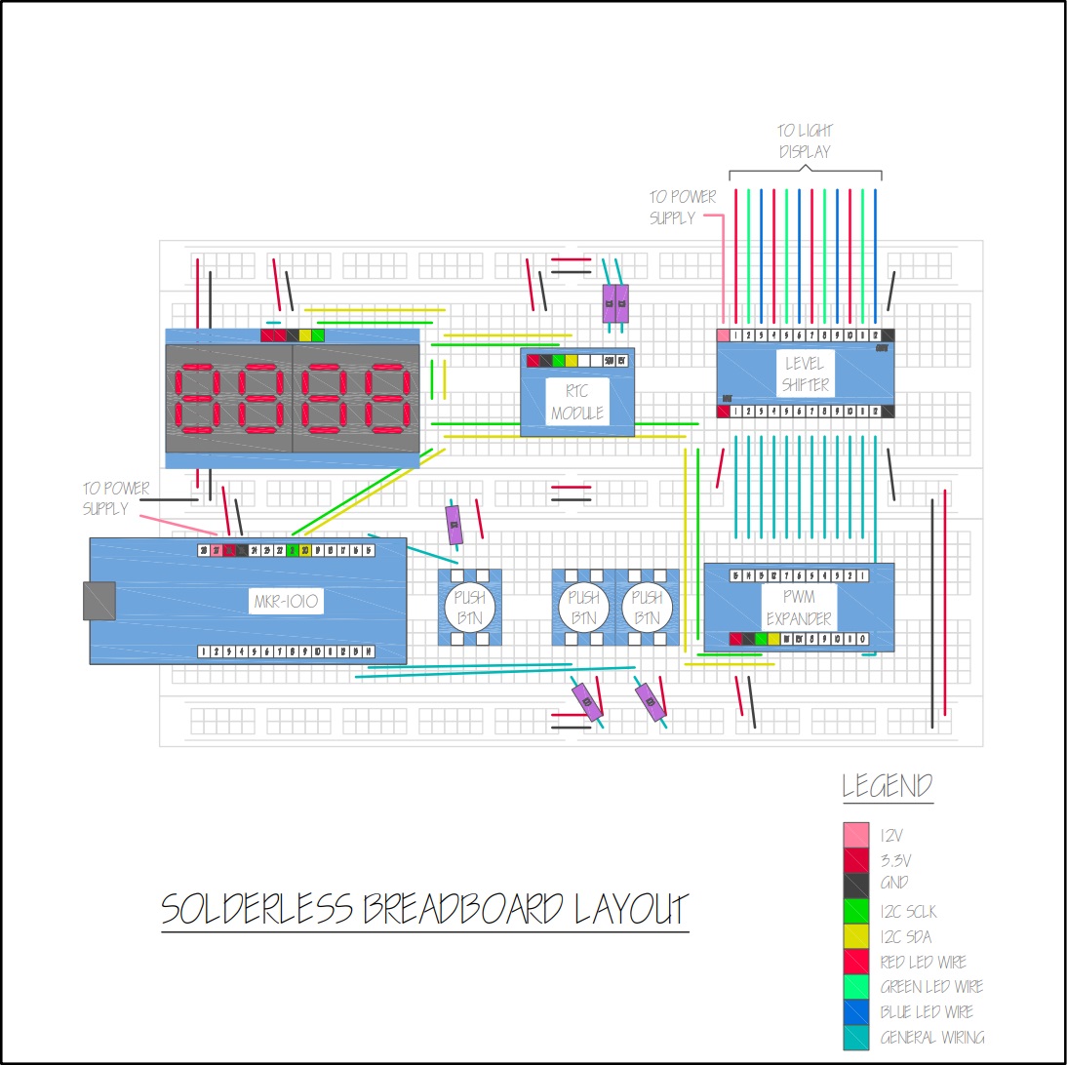
docs/imgs/circuit/solderless-breadboard-layout-rev-a-no-anno__2024-05-29.jpg
