rebeccajr/color-clock/docs/imgs/photos/hardware/solderless-bread-board__2024-05-29.JPEG

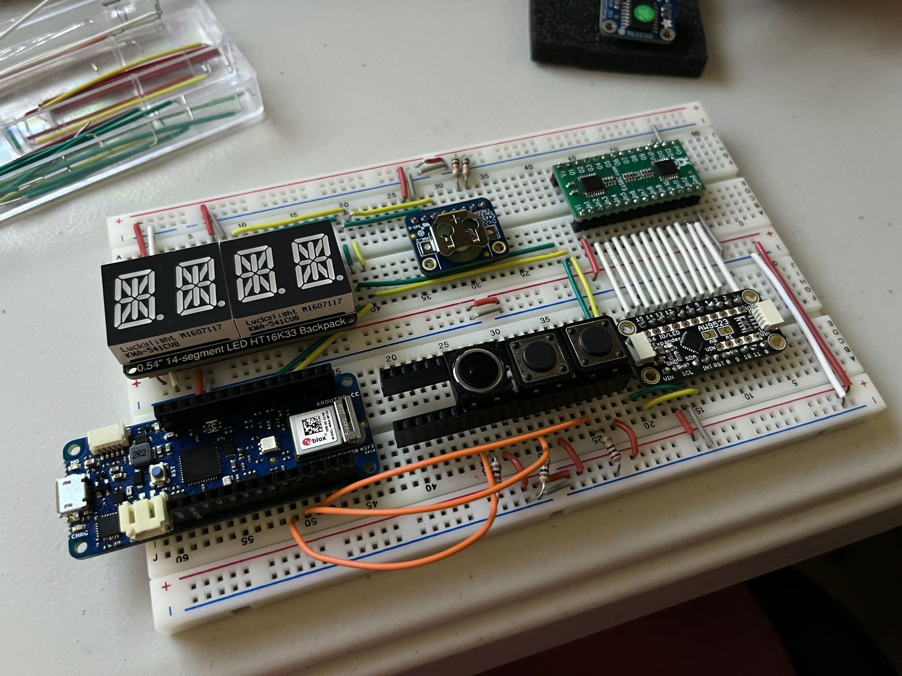
docs/imgs/photos/hardware/solderless-bread-board__2024-05-29.JPEG
