rebeccajr/color-clock/docs/slide-decks/2024-08-10__demo/3__rgb-led-common-anode.pdf

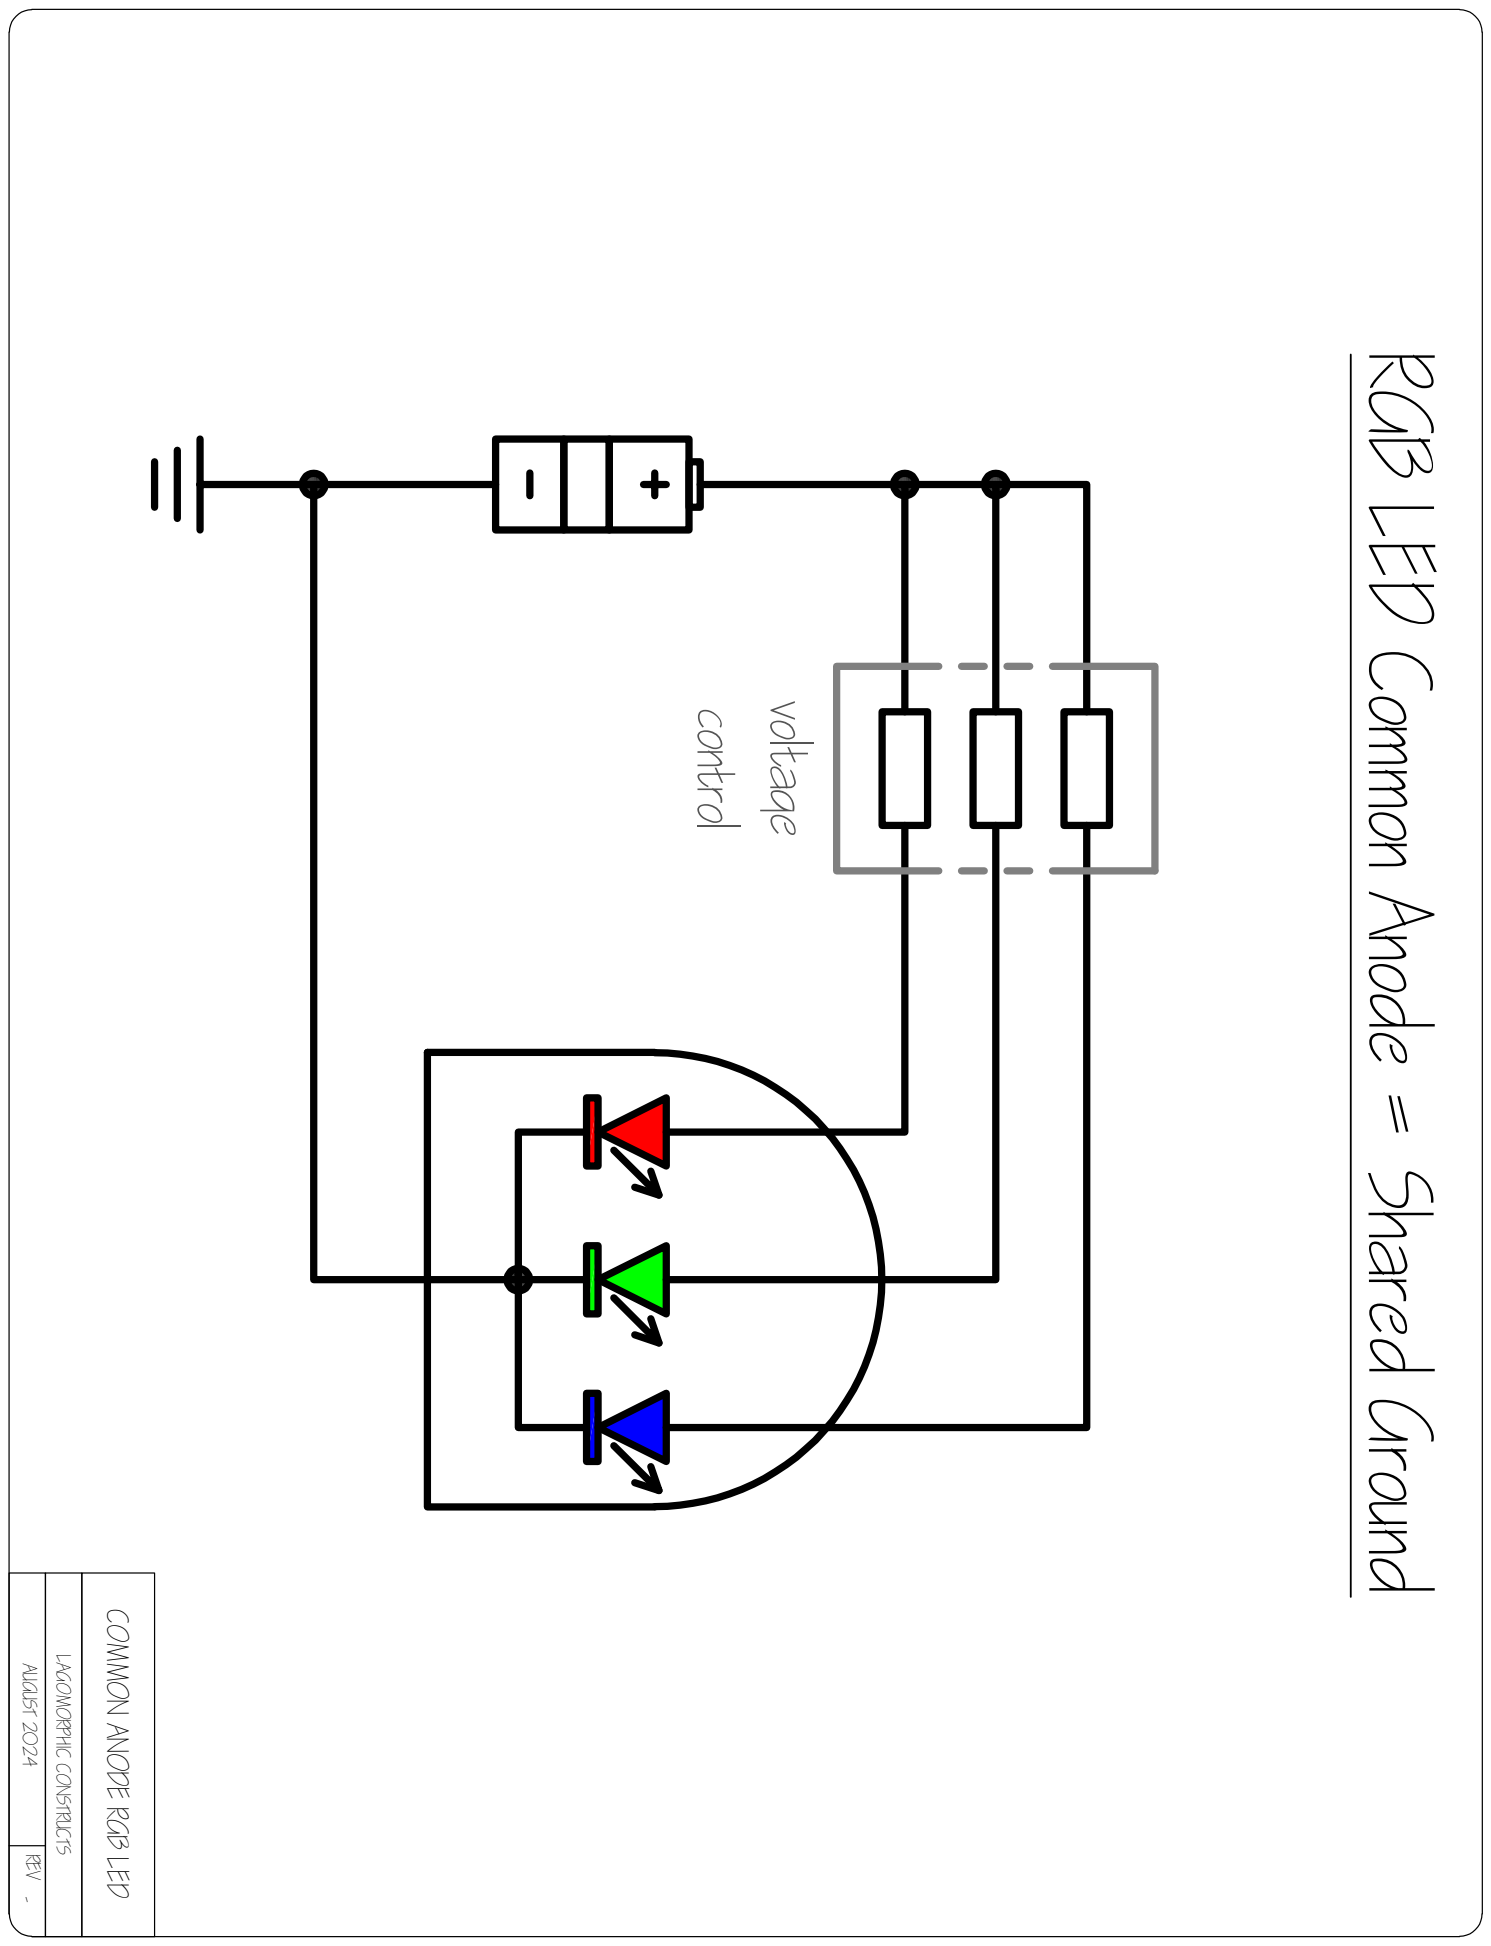
[picture p73: page 1]

REV LAGOMORPHIC CONSTRUCTS - AUGUST 2024 COMMON ANODE RGB LED RGB LED Common Anode = Shared Ground control voltage
