rebeccajr/color-clock/docs/slide-decks/2024-08-10__demo/4__rgb-color-mix.pdf

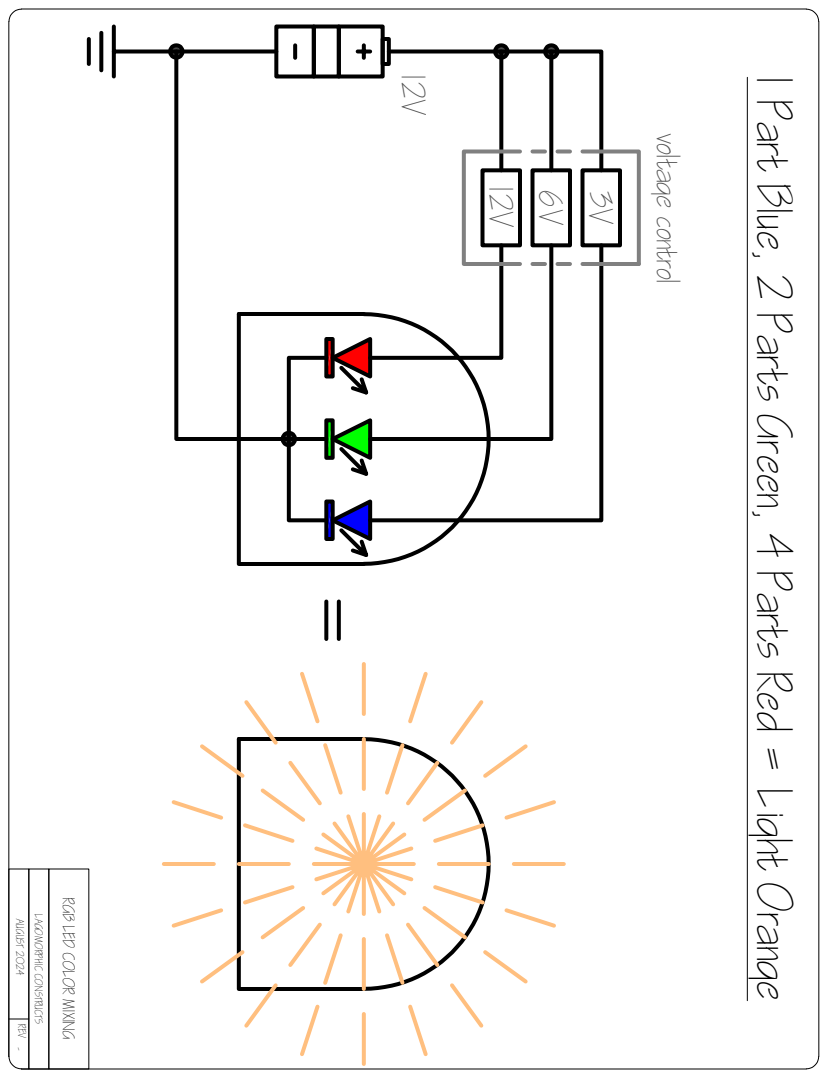
[picture p74: page 1]
voltage control

REV LAGOMORPHIC CONSTRUCTS - AUGUST 2024 RGB LED COLOR MIXING 12V

1 Part Blue, 2 Parts Green, 4 Parts Red = Light Orange
