rebeccajr/color-clock/docs/slide-decks/2024-08-10__demo/6a__level-shifter.pdf

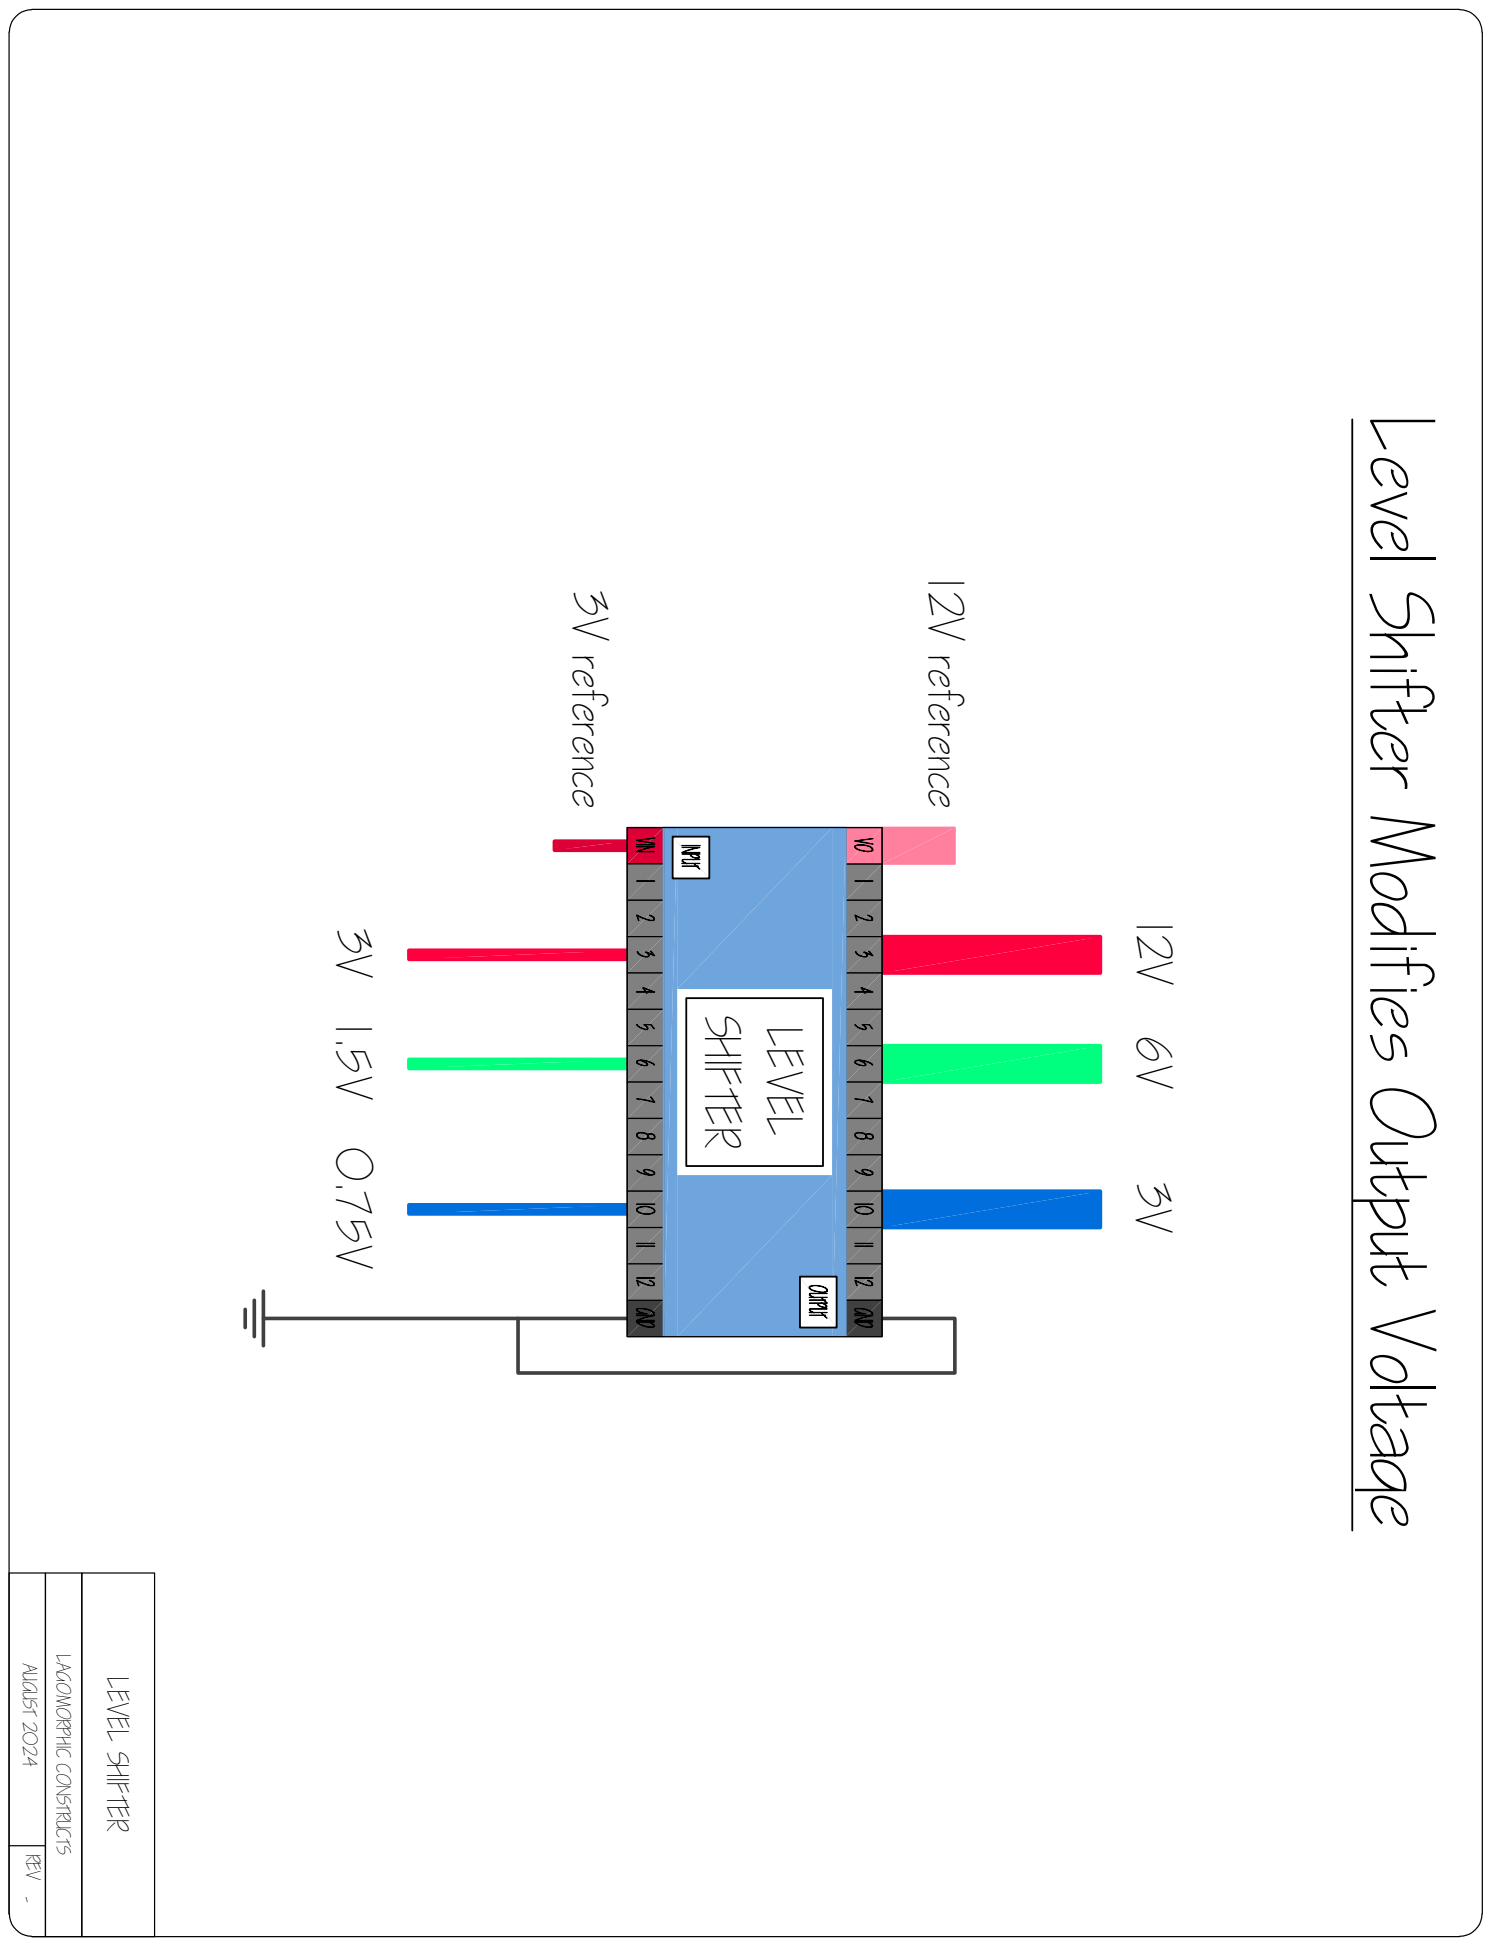
[picture p75: page 1]

3V reference 12V reference 3V 1.5V 0.75V 12V 6V 3V LEVEL SHIFTER REV LAGOMORPHIC CONSTRUCTS - AUGUST 2024 LEVEL SHIFTER Level Shifter Modifies Output Voltage
