rebeccajr/color-clock/docs/slide-decks/2024-08-10__demo/7__level-shifter.pdf

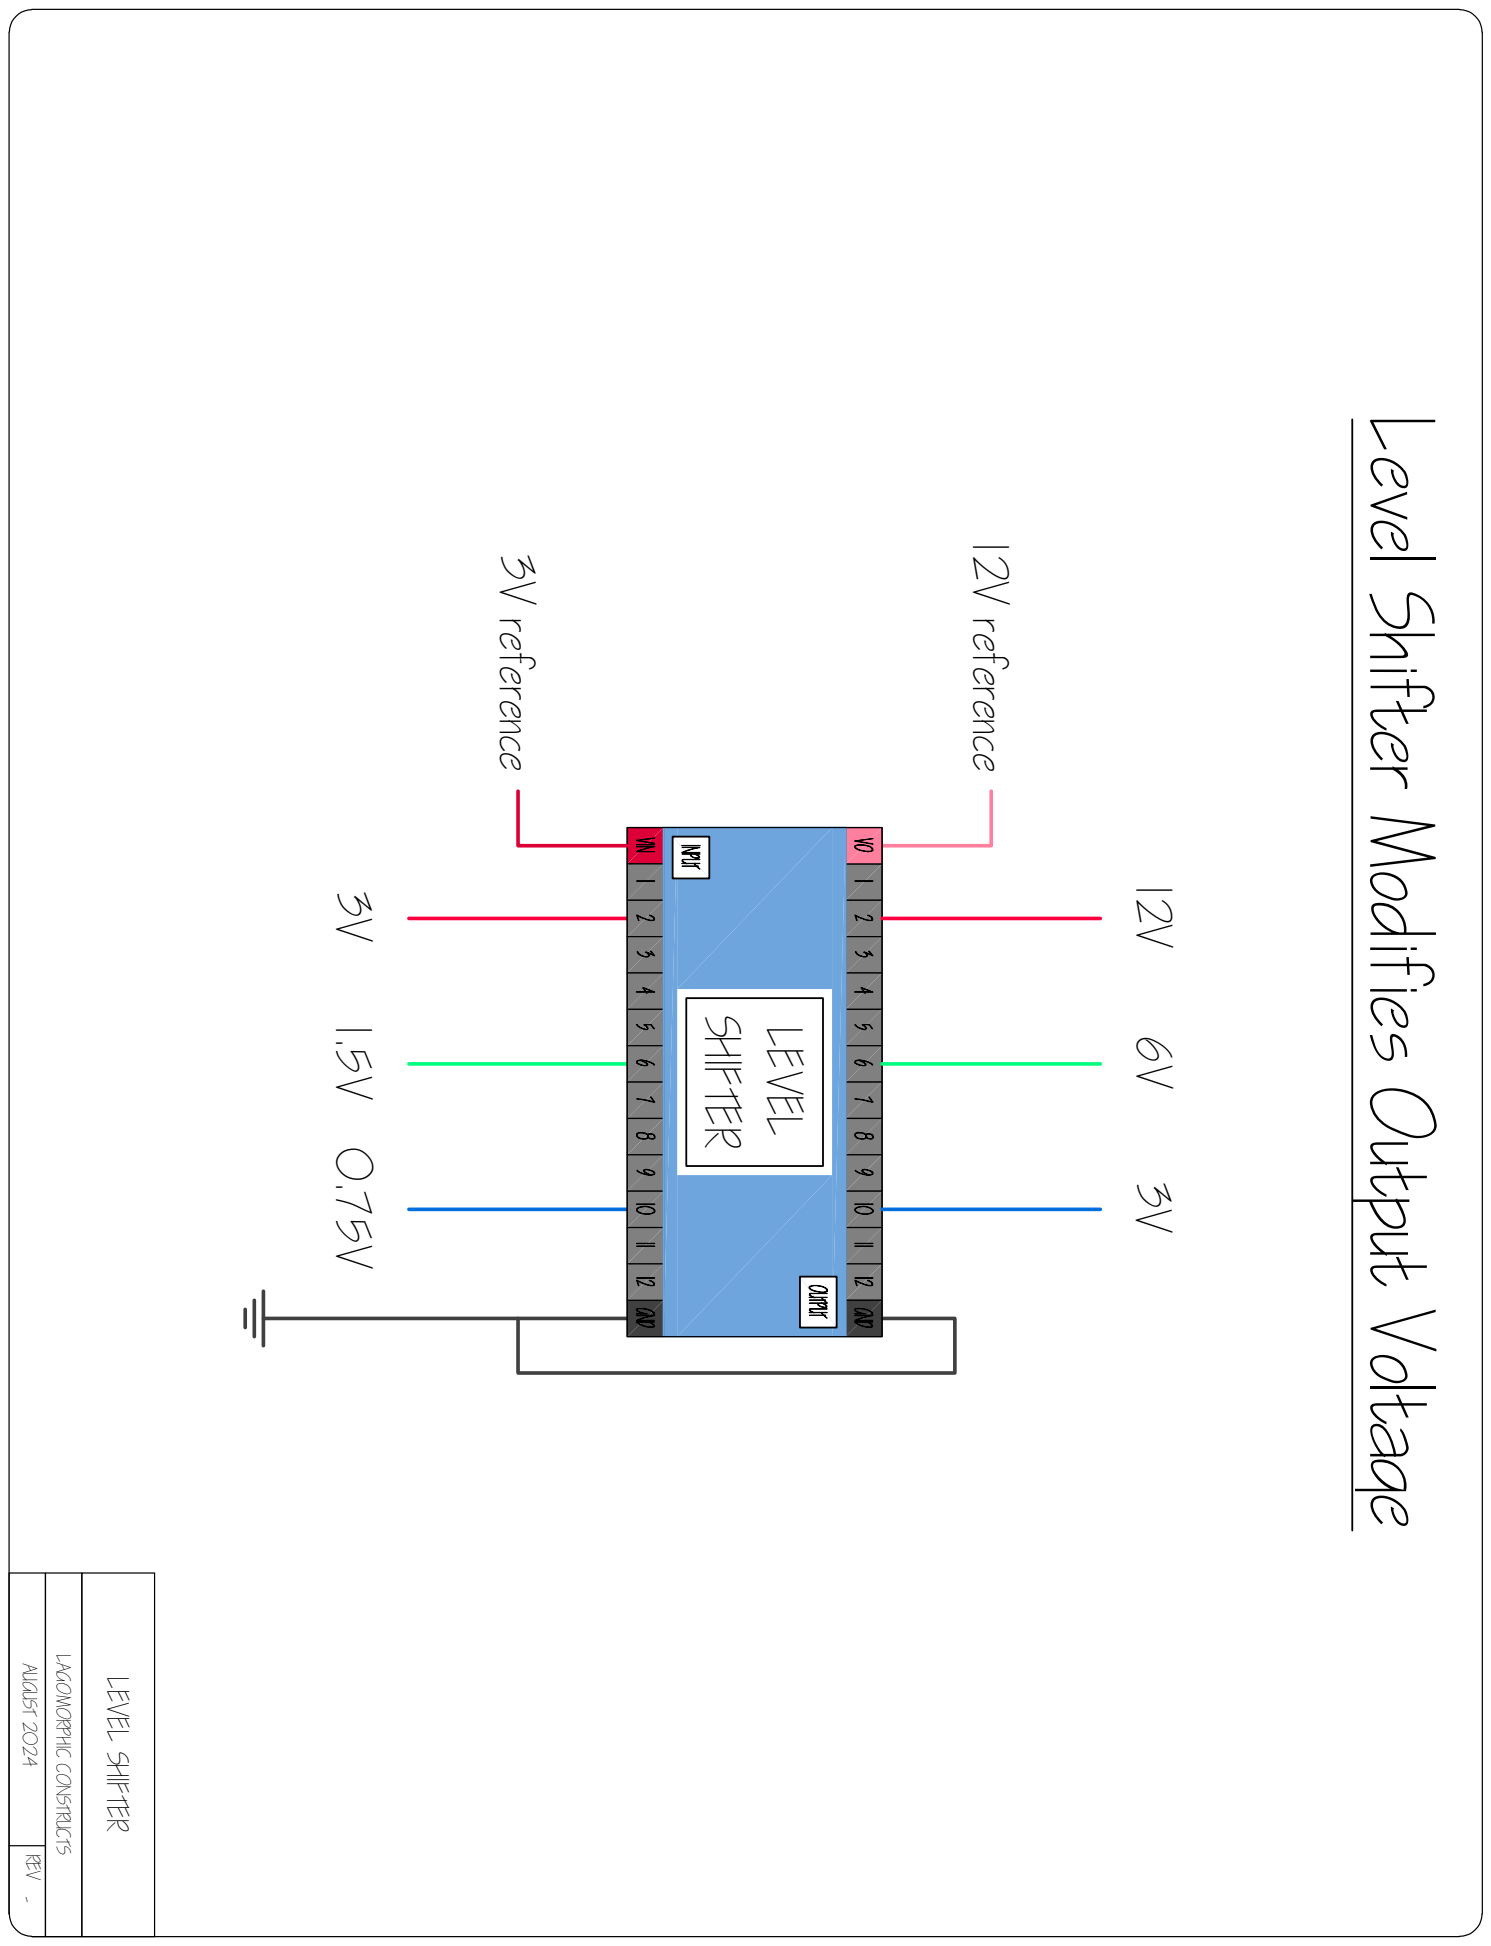
[picture p77: page 1]

12V reference LEVEL SHIFTER 3V reference 3V 1.5V 0.75V 12V 6V 3V REV LAGOMORPHIC CONSTRUCTS - AUGUST 2024 LEVEL SHIFTER Level Shifter Modifies Output Voltage
