rebeccajr/color-clock/docs/slide-decks/2024-08-10__demo/8__circuit-board-full.pdf

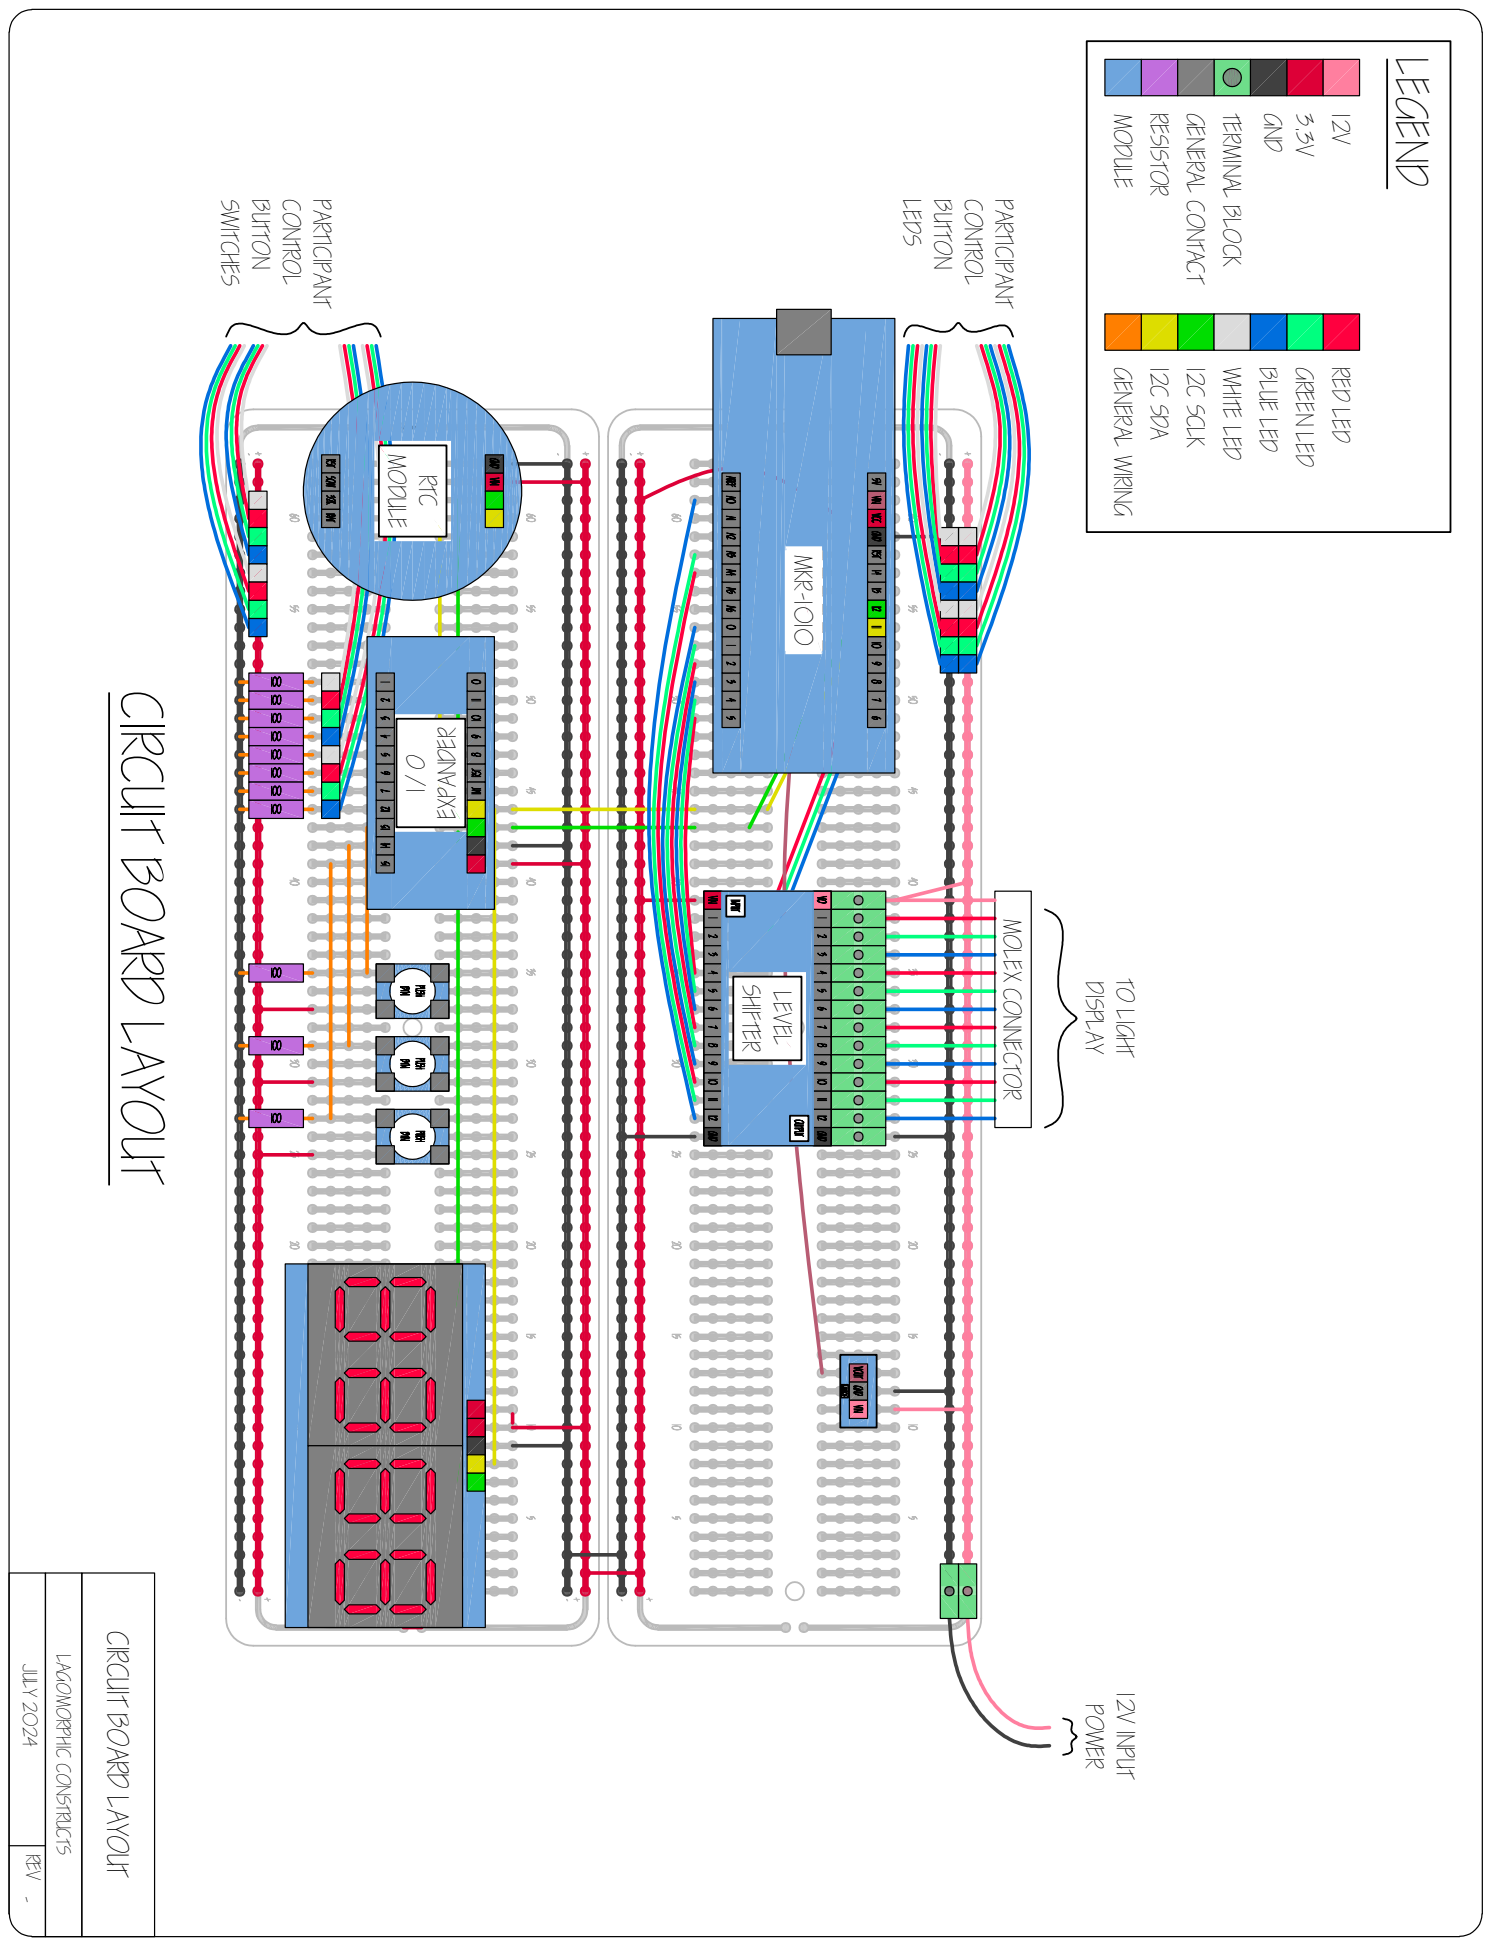
[picture p78: page 1]

LEDS BUTTON CONTROL PARTICIPANT MOLEX CONNECTOR DISPLAY TO LIGHT 12V INPUT POWER SWITCHES BUTTON CONTROL PARTICIPANT RTC MODULE I/O EXPANDER LEVEL SHIFTER MKR-1010 3.3V 12V RED LED I2C SDA I2C SCLK GND LEGEND RESISTOR WHITE LED GREEN LED TERMINAL BLOCK GENERAL WIRING BLUE LED MODULE GENERAL CONTACT REV LAGOMORPHIC CONSTRUCTS - JULY 2024 CIRCUIT BOARD LAYOUT CIRCUIT BOARD LAYOUT
