rebeccajr/color-clock/docs/slide-decks/2024-08-10__demo/04__rgb-color-mix.pdf

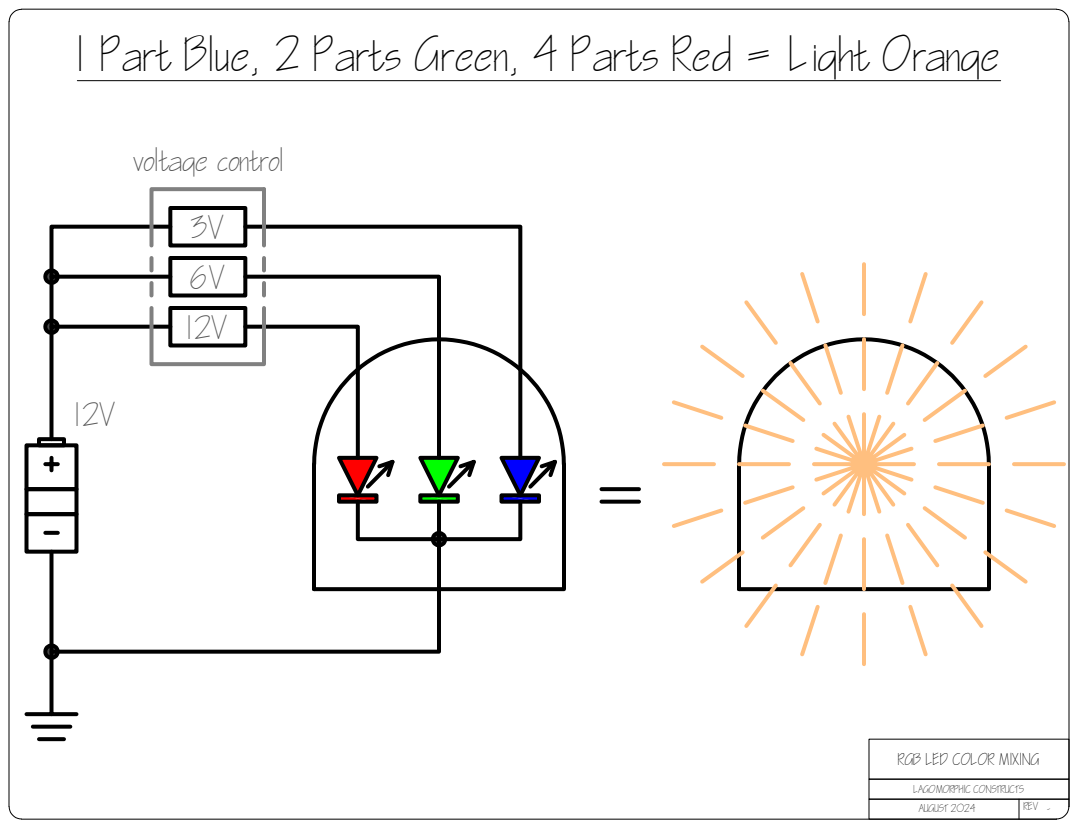
[picture p79: page 1]
REV LAGOMORPHIC CONSTRUCTS AUGUST 2024; - RGB LED COLOR MIXING 1 Part Blue, 2 Parts Green, 4 Parts Red = Light Orange 12V; 12V6V3V voltage control
