rebeccajr/color-clock/docs/slide-decks/2024-08-10__demo/05__level-shifter.pdf

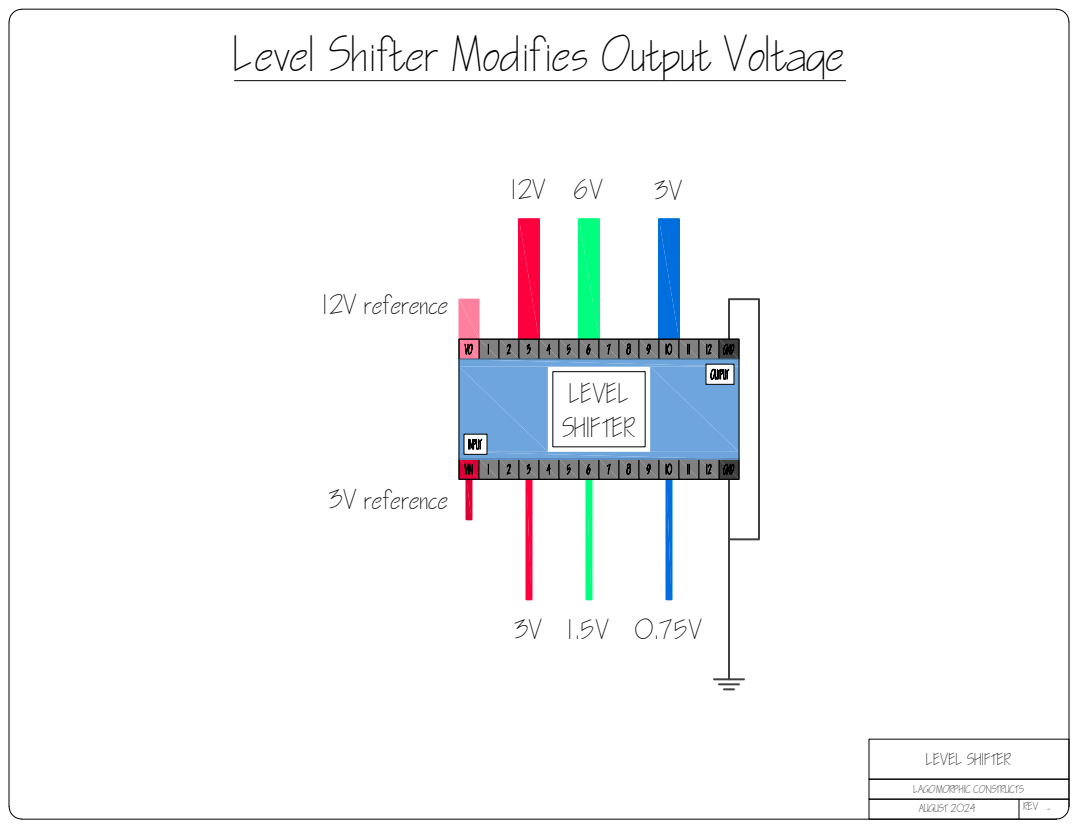
[picture p80: page 1]
12V reference 3V reference; 3V LEVEL SHIFTER; REV LAGOMORPHIC CONSTRUCTS AUGUST 2024; - LEVEL SHIFTER Level Shifter Modifies Output Voltage
