rebeccajr/color-clock/docs/slide-decks/2024-08-10__demo/08__level-shifter.pdf

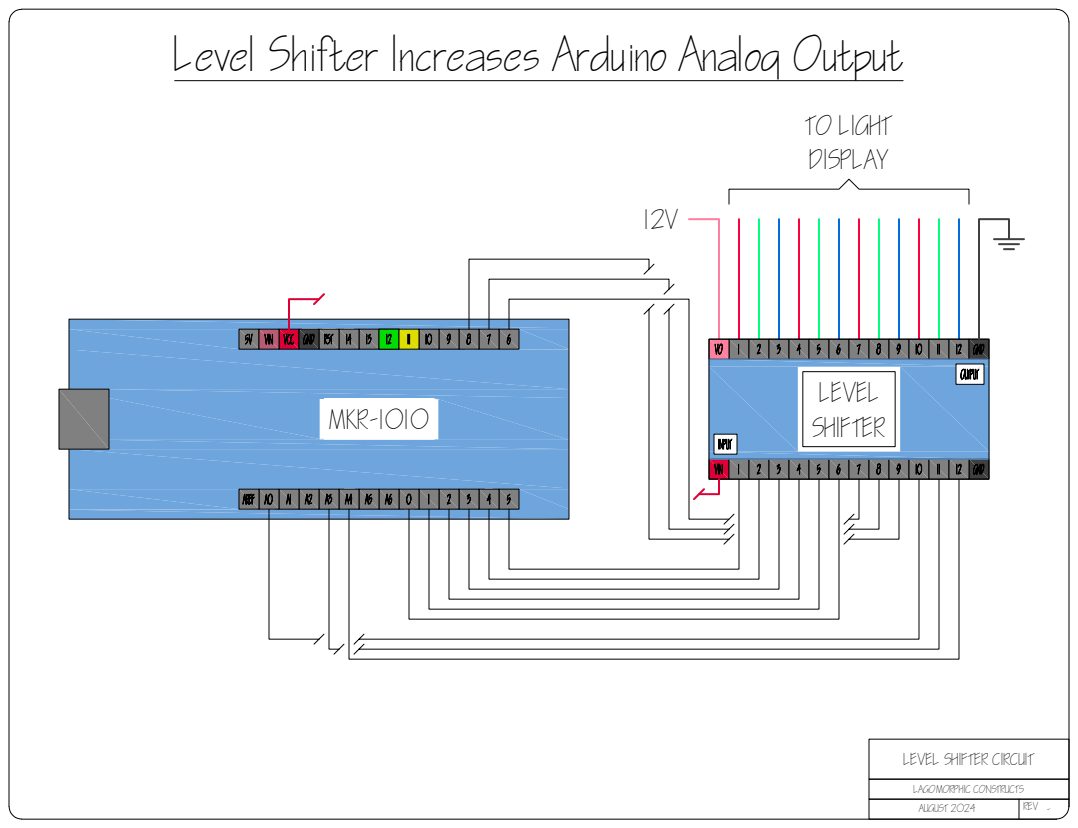
[picture p81: page 1]
MKR-1010; TO LIGHT DISPLAY LEVEL SHIFTER 12V; REV LAGOMORPHIC CONSTRUCTS AUGUST 2024; - LEVEL SHIFTER CIRCUIT Level Shifter Increases Arduino Analog Output
