rebeccajr/color-clock/docs/slide-decks/2024-08-10__demo/09__circuit-board-full.pdf

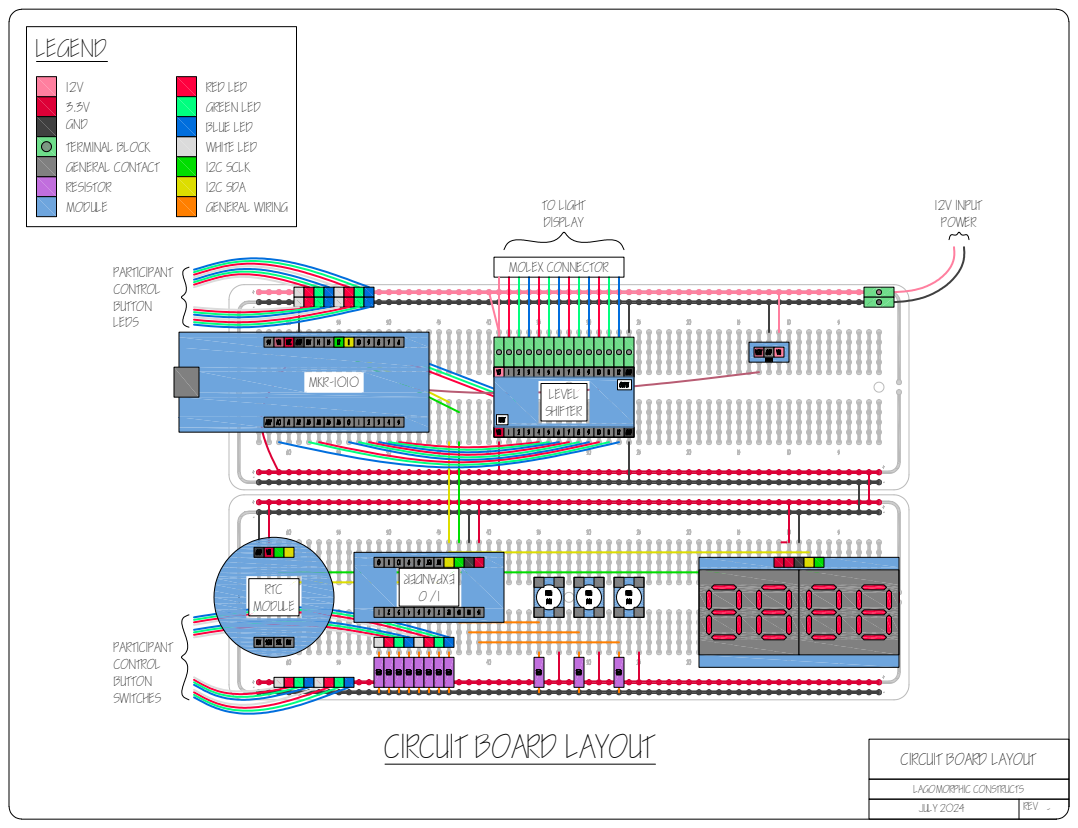
[picture p82: page 1]
PARTICIPANT CONTROL BUTTON LEDS; MOLEX CONNECTOR TO LIGHT DISPLAY; 12V INPUT POWER PARTICIPANT CONTROL BUTTON SWITCHES; RTC MODULE; EXPANDER; LEVEL SHIFTER MKR-1010 3.3V 12V; RED LED I2C SCLK I2C SDA GND LEGEND RESISTOR; GREEN LED TERMINAL BLOCK; WHITE LED GENERAL WIRING BLUE LED GENERAL CONTACT MODULE; REV LAGOMORPHIC CONSTRUCTS JULY 2024; - CIRCUIT BOARD LAYOUT; CIRCUIT BOARD LAYOUT
