rebeccajr/color-clock/docs/slide-decks/2024-08-10__demo/10__circuit-board-wire.pdf

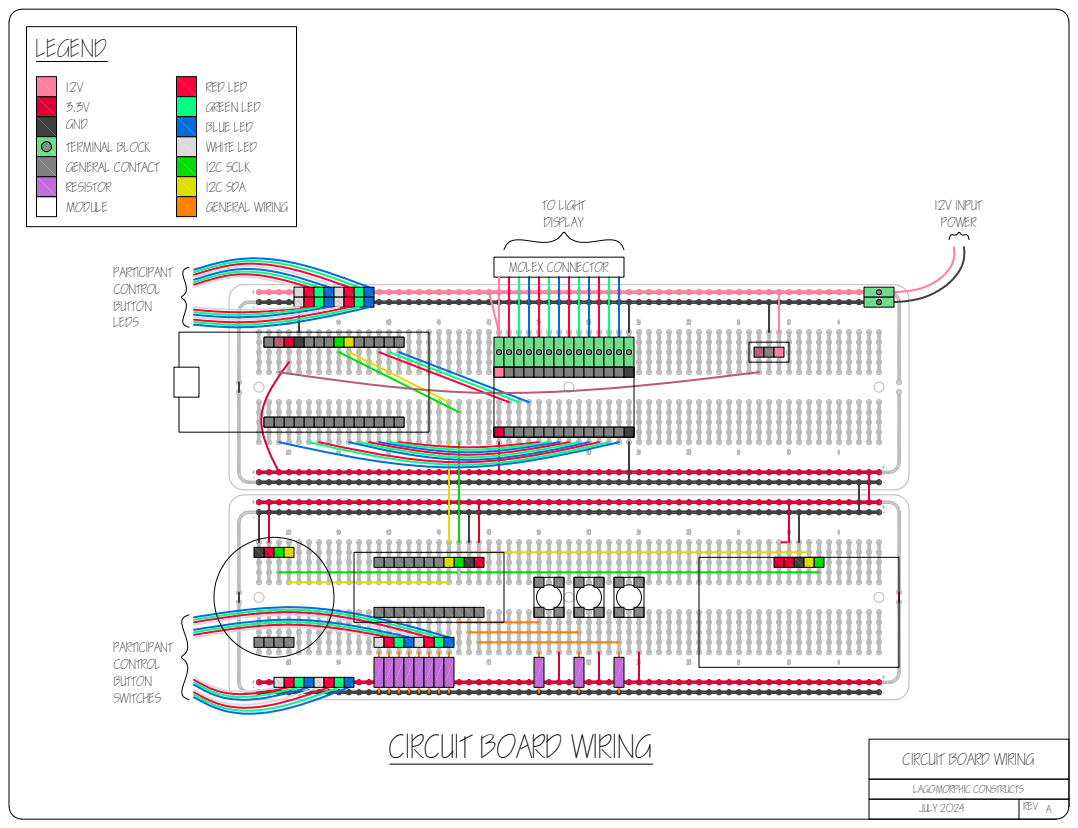
[picture p83: page 1]
RED LED I2C SCLK I2C SDA GND LEGEND RESISTOR; GREEN LED TERMINAL BLOCK; WHITE LED GENERAL WIRING BLUE LED GENERAL CONTACT MODULE PARTICIPANT CONTROL BUTTON LEDS; MOLEX CONNECTOR TO LIGHT DISPLAY; 12V INPUT POWER PARTICIPANT CONTROL BUTTON SWITCHES; REV LAGOMORPHIC CONSTRUCTS JULY 2024; A CIRCUIT BOARD WIRING; CIRCUIT BOARD WIRING
