rebeccajr/color-clock/docs/slide-decks/2024-08-10__demo/5b__top-level.pdf

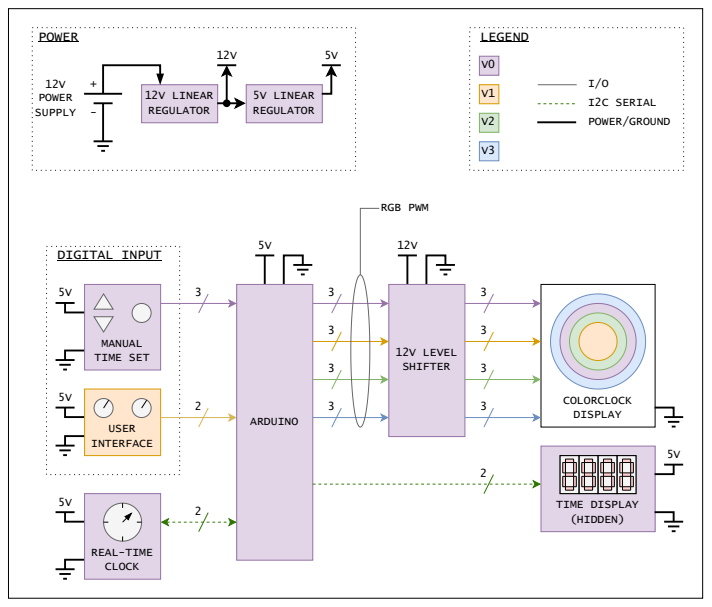
[picture p84: page 1]
ARDUINO; USER INTERFACE; 12V LEVEL SHIFTER; TIME DISPLAY (HIDDEN); COLORCLOCK DISPLAY; RGB PWM; DIGITAL INPUT; MANUAL TIME SET; REAL-TIME CLOCK; I2C SERIAL; POWER/GROUND; LEGEND; 12V LINEAR REGULATOR; 5V LINEAR REGULATOR; 12V POWER SUPPLY; POWER
