rebeccajr/color-clock/docs/imgs/circuit/level-shifter__2024-06-06.pdf

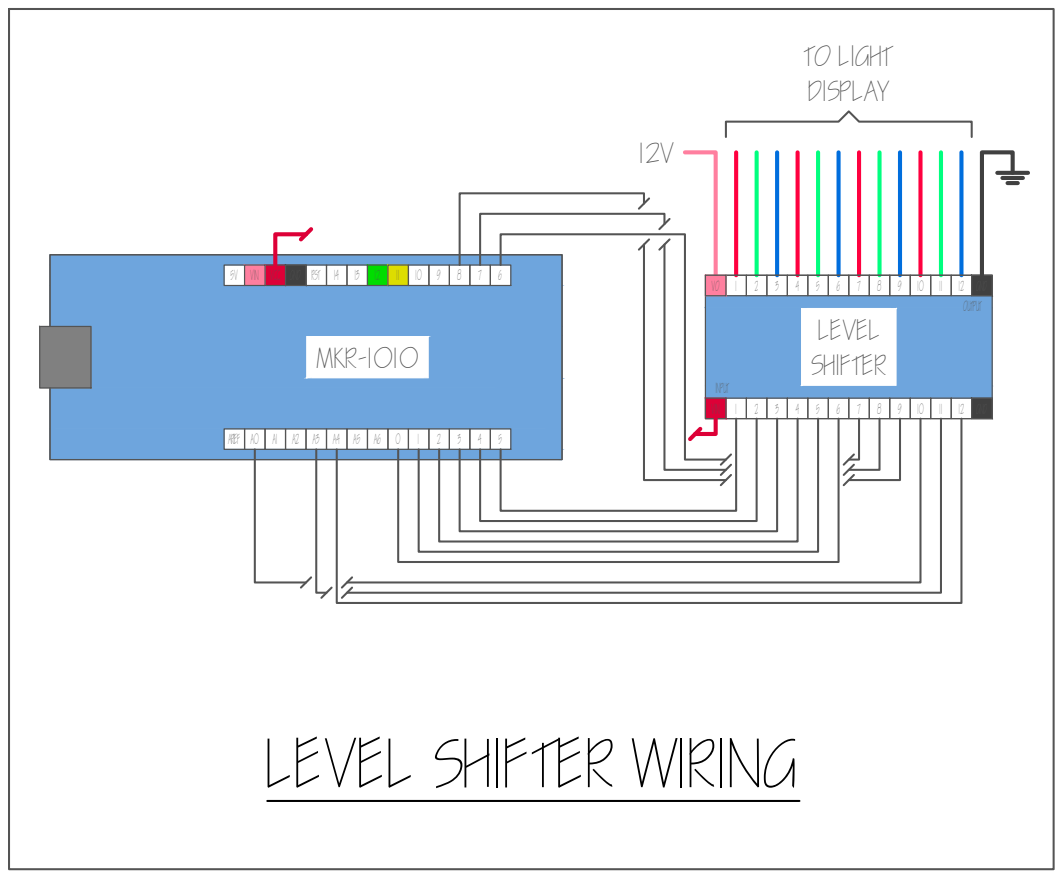
[picture p85: page 1]
TO LIGHT

5V | VIN | VCC | GND | RST | 14 | 13 | 12 | 11 | 10 | 9 | 8 | 7 | 6

INPUT | OUTPUT VO GND GND LEVEL SHIFTER

VIN | 1 | 2 | 3 | 4 | 5 | 6 | 7 | 8 | 9 | 10 | 11 | 12

LEVEL SHIFTER WIRING
