rebeccajr/color-clock/docs/slide-decks/2024-08-10__demo/0b__intro-title.pdf

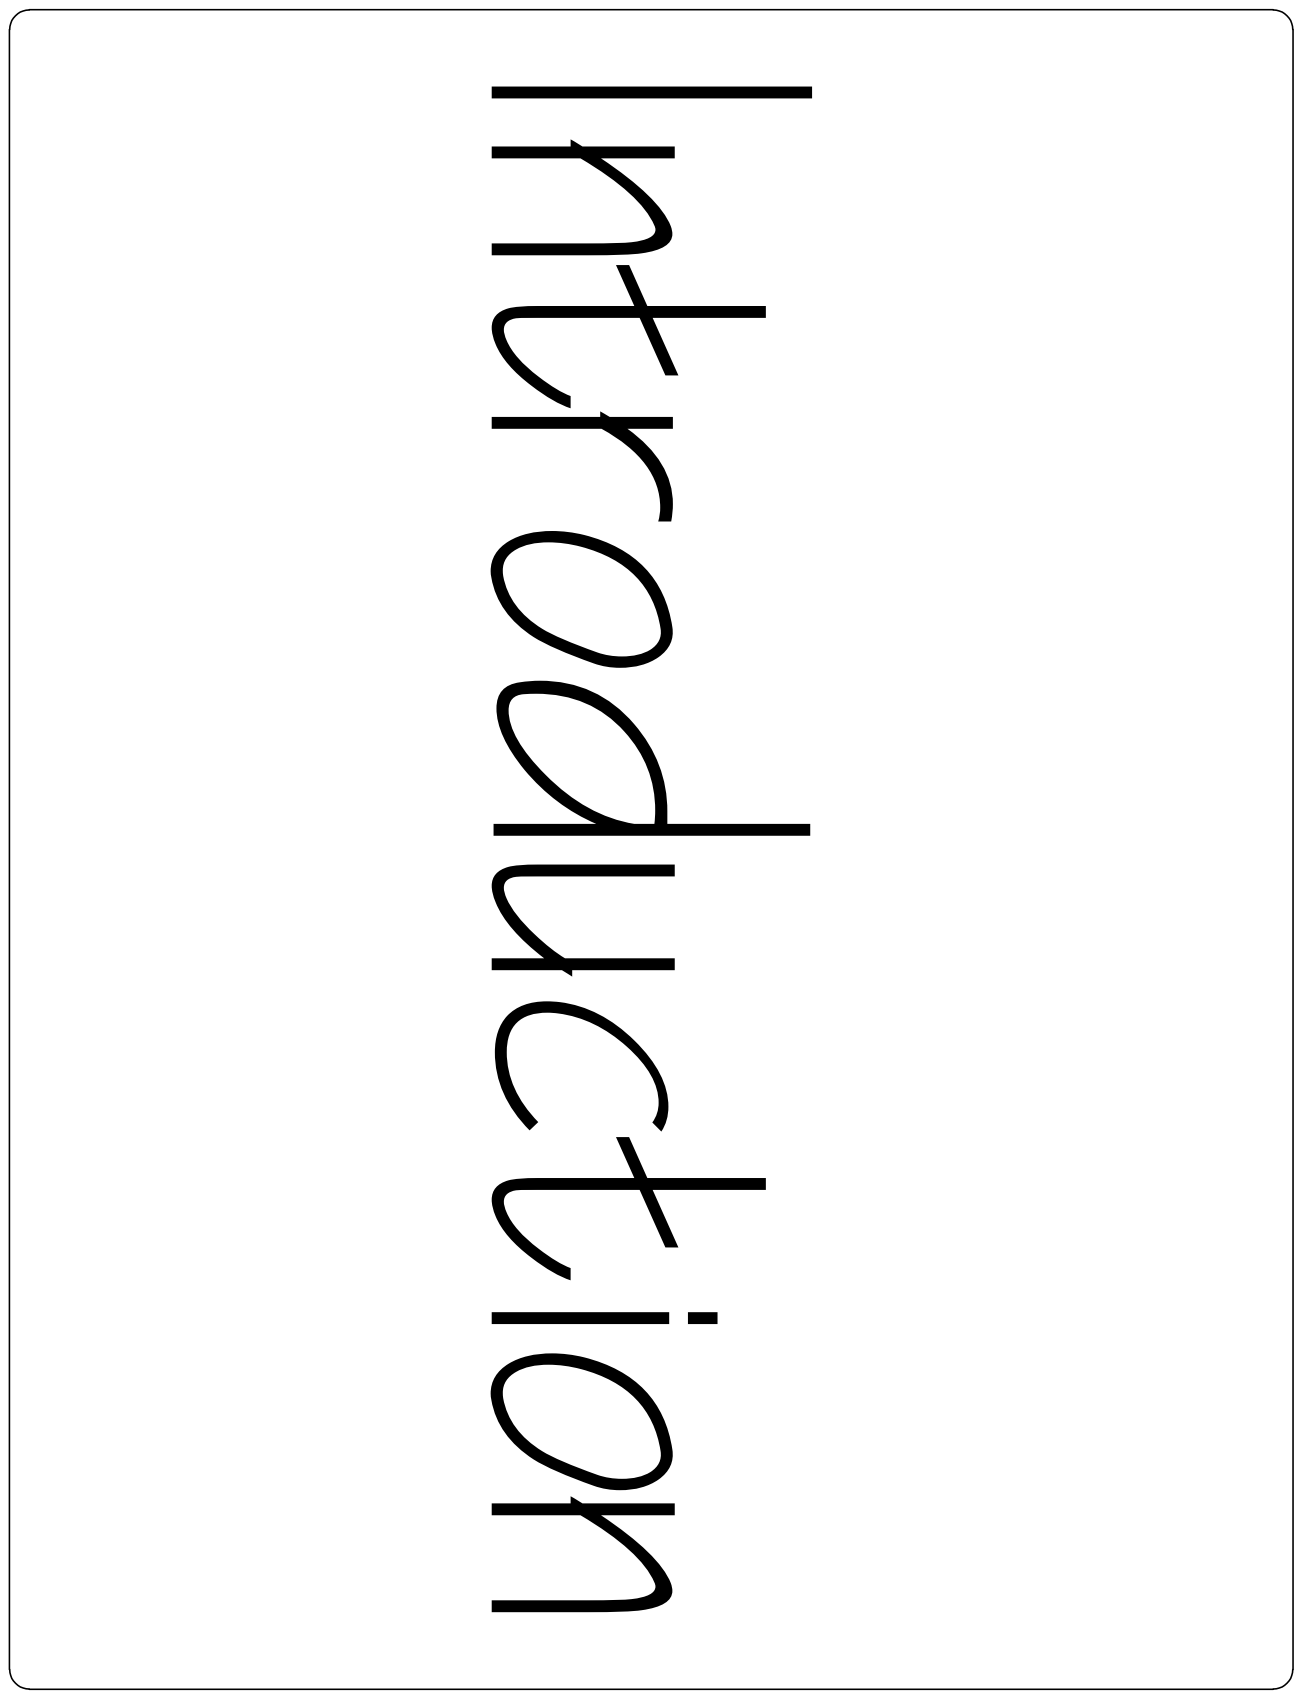
[picture p88: page 1]
