rebeccajr/color-clock/docs/slide-decks/2024-08-10__demo/10_.pdf

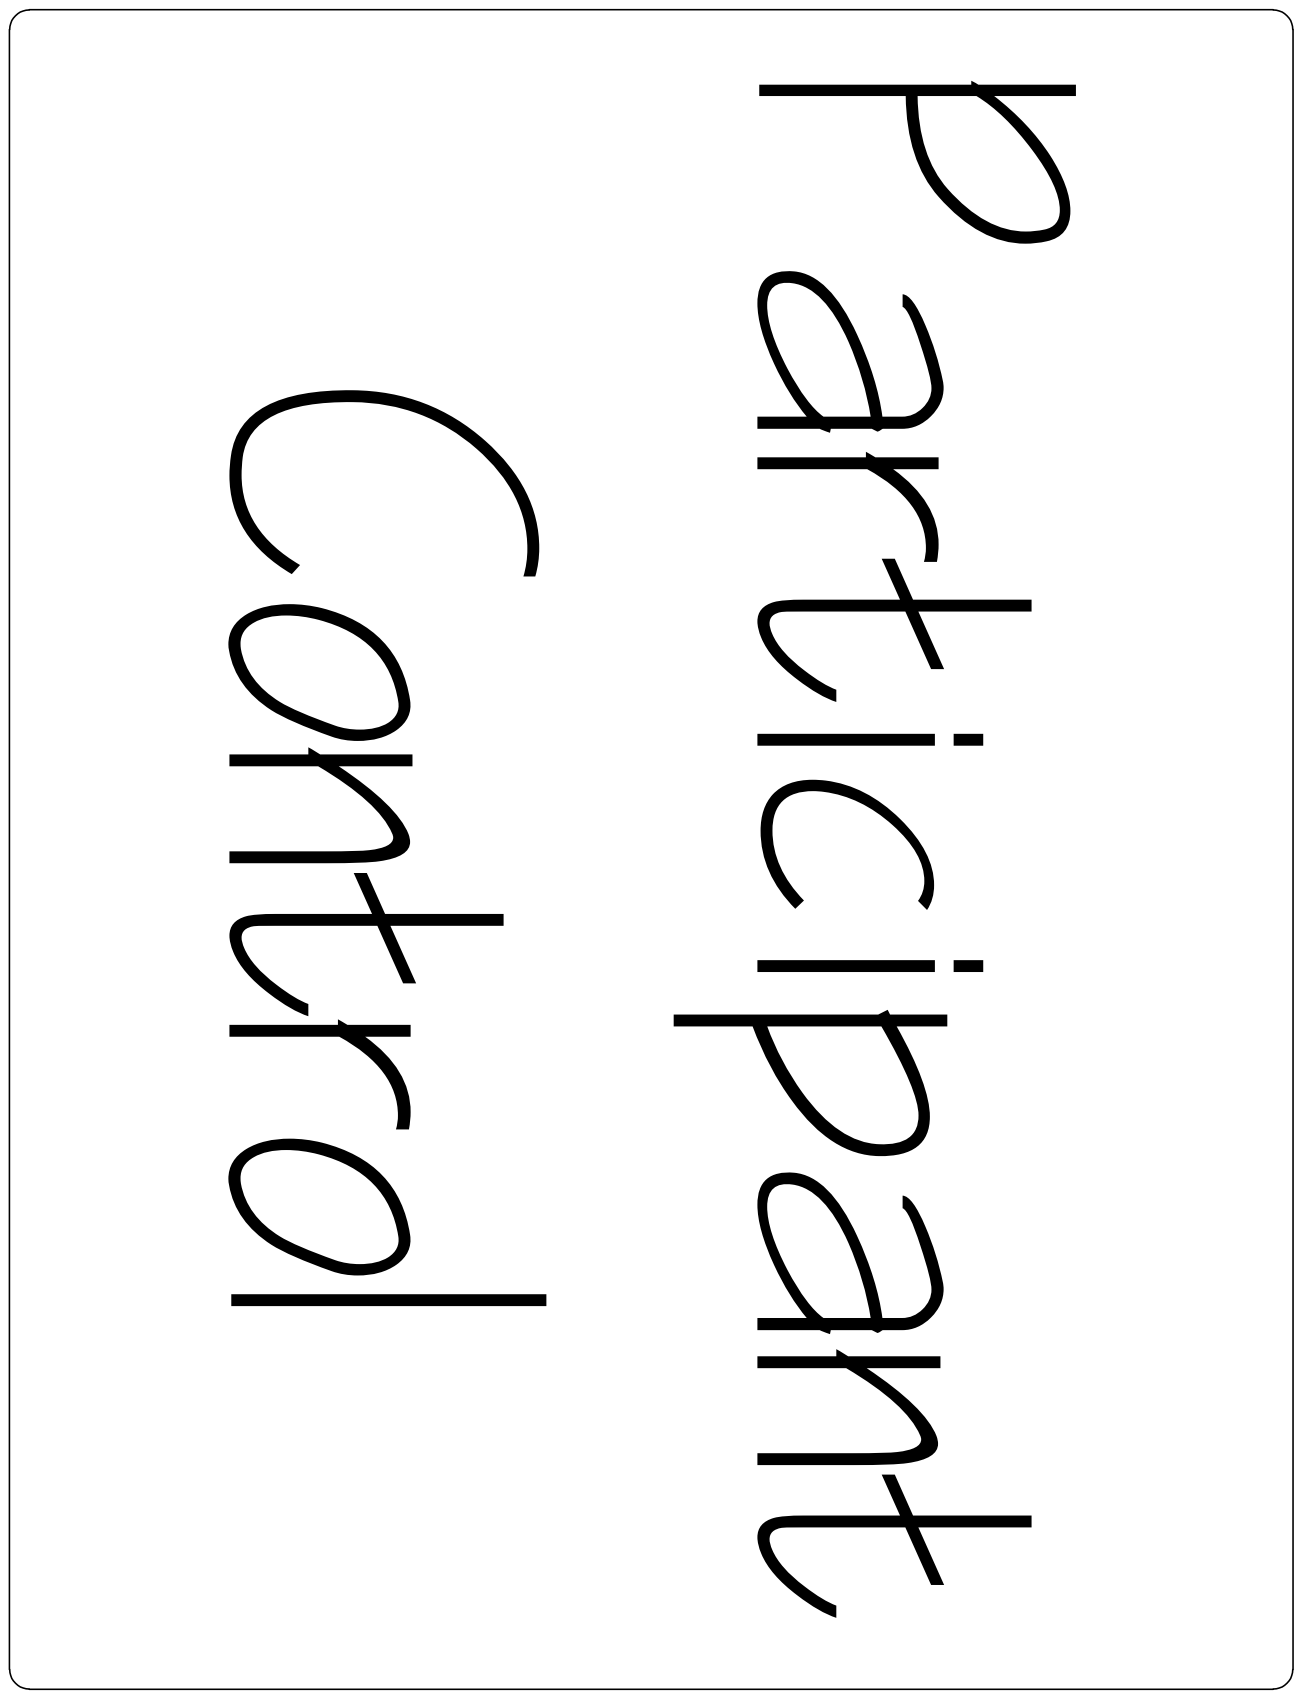
[picture p89: page 1]
