rebeccajr/color-clock/docs/slide-decks/2024-08-10__demo/11.pdf

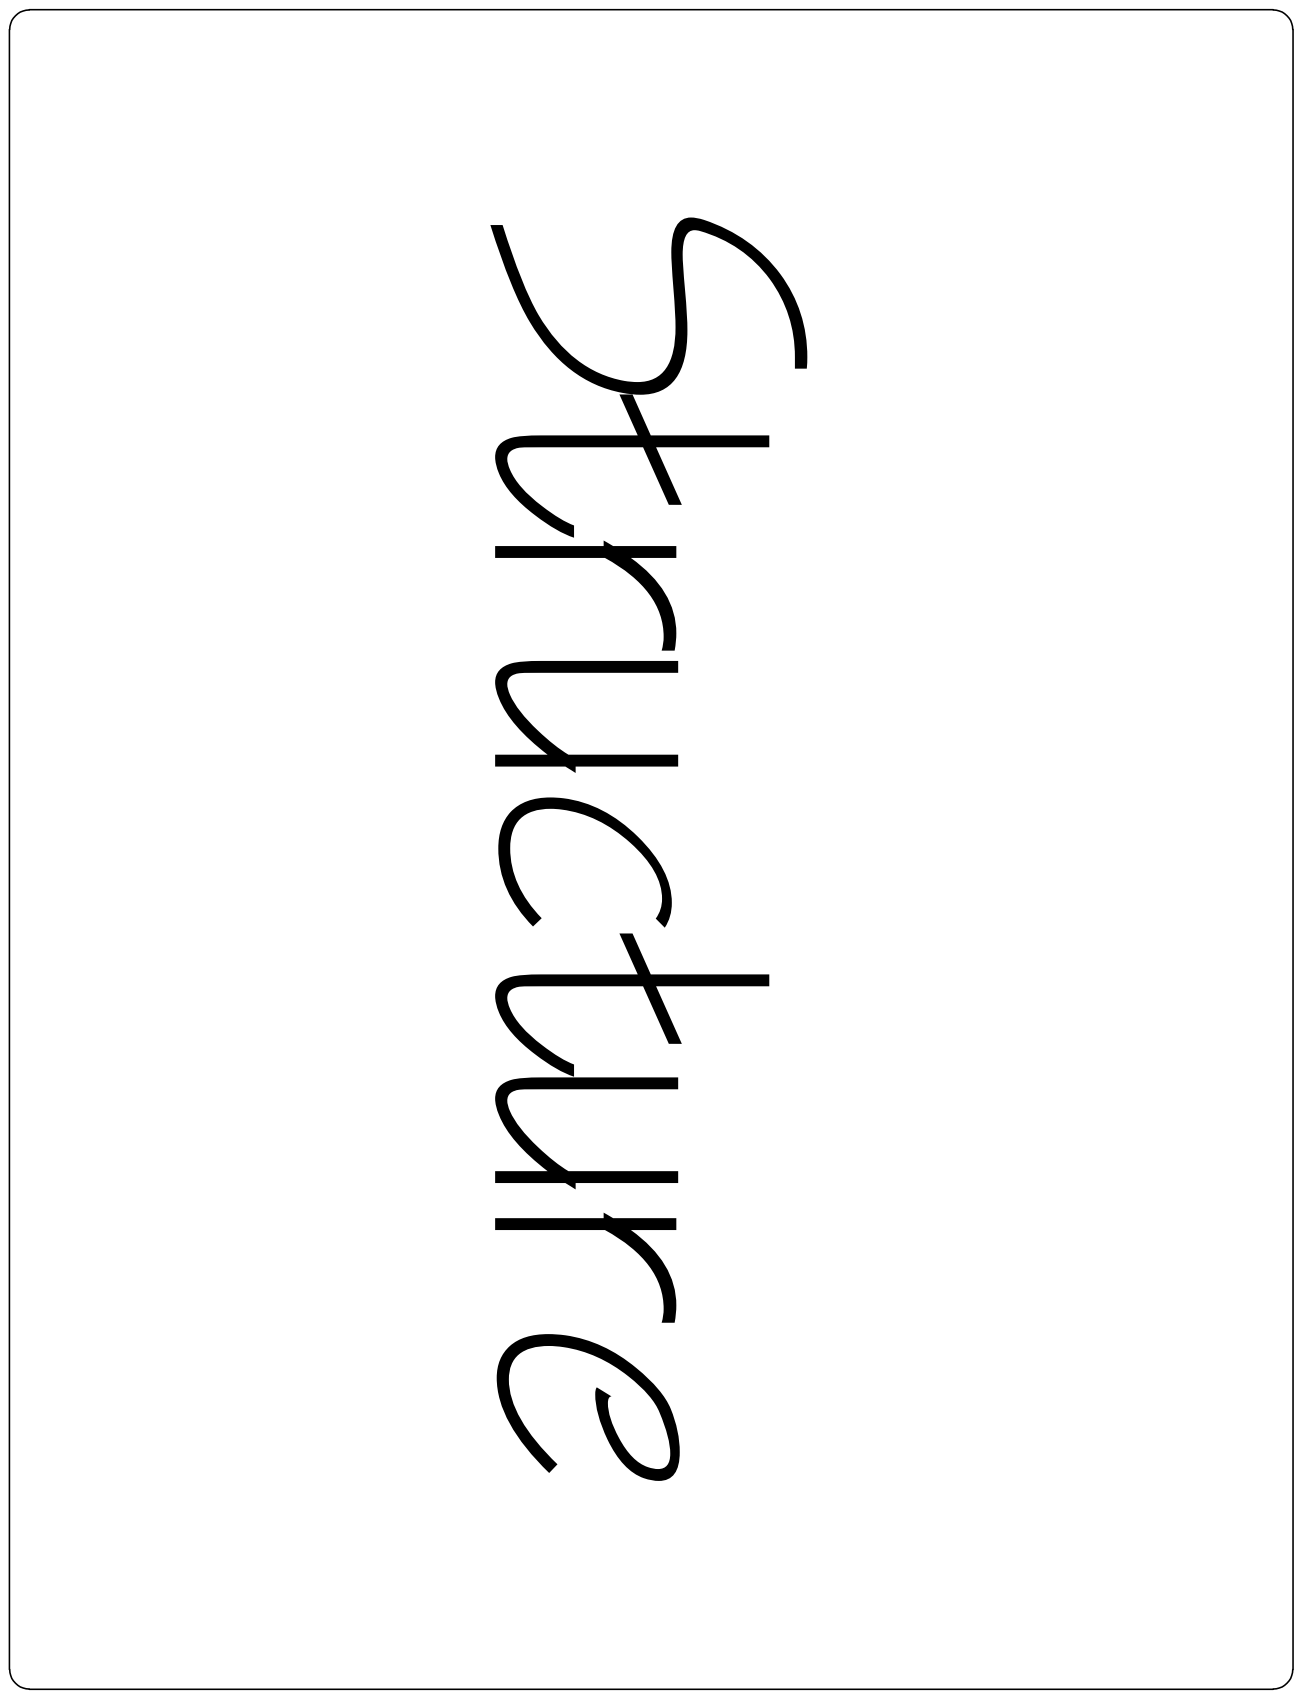
[picture p90: page 1]
