rebeccajr/color-clock/docs/slide-decks/2024-08-10__demo/12.pdf

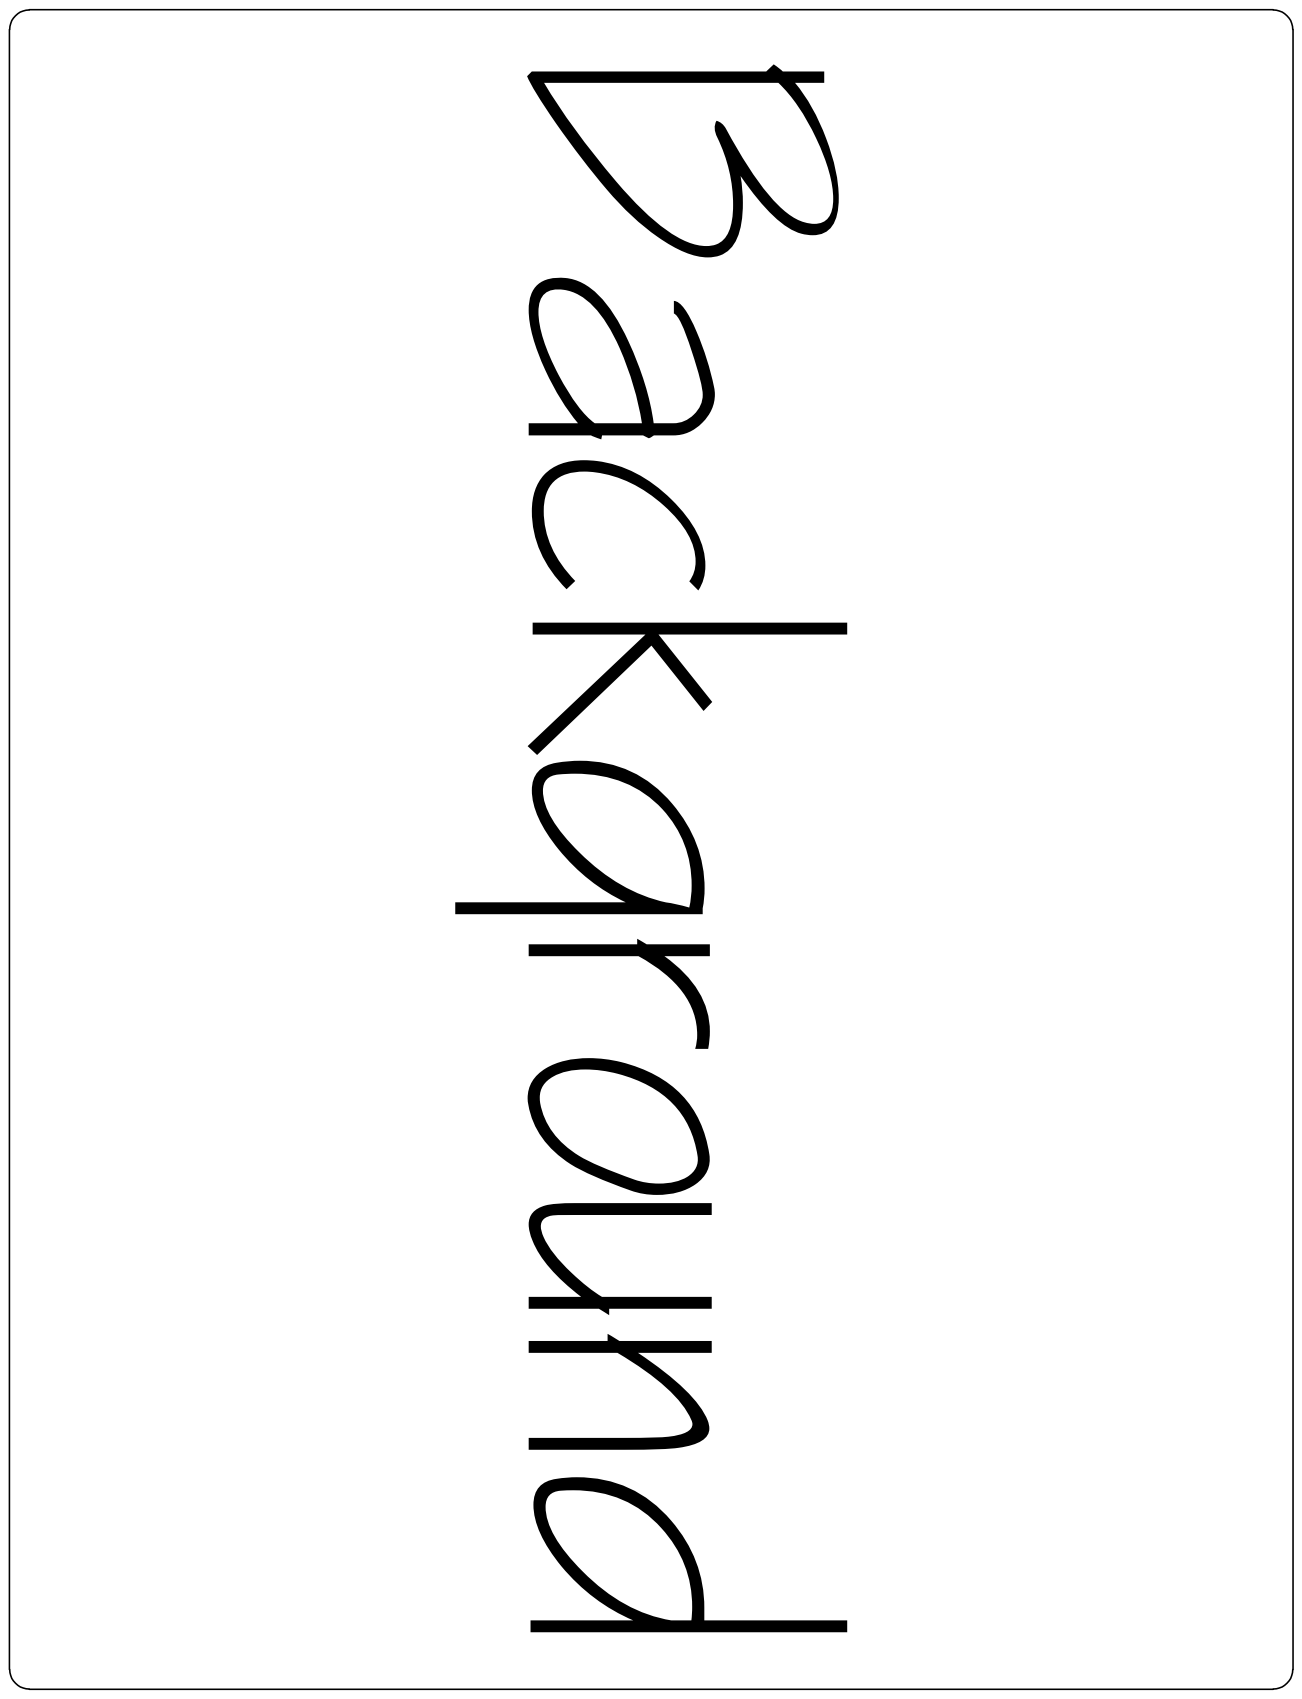
[picture p91: page 1]
