rebeccajr/color-clock/docs/slide-decks/2024-08-10__demo/13.pdf

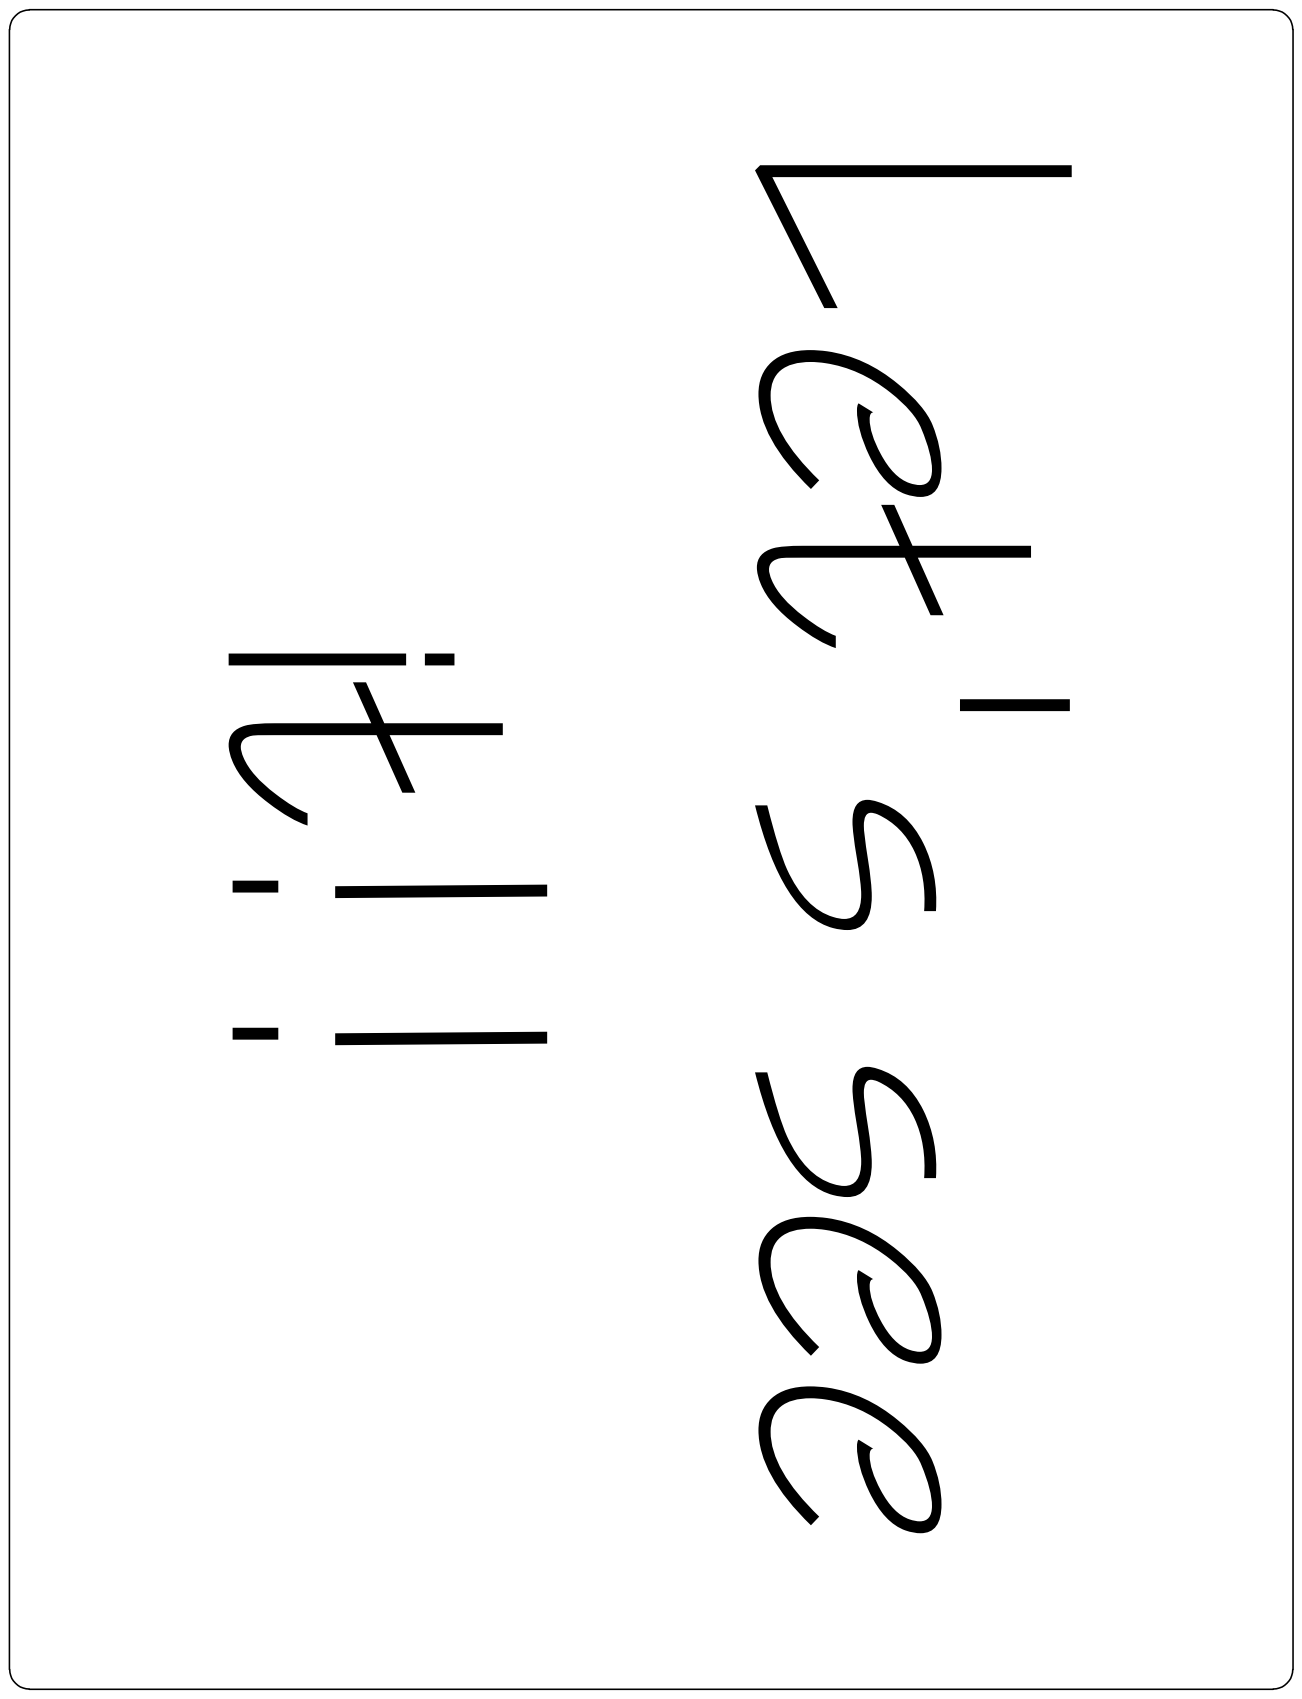
[picture p92: page 1]
