rebeccajr/color-clock/docs/slide-decks/2024-08-10__demo/1__pigment-color.pdf

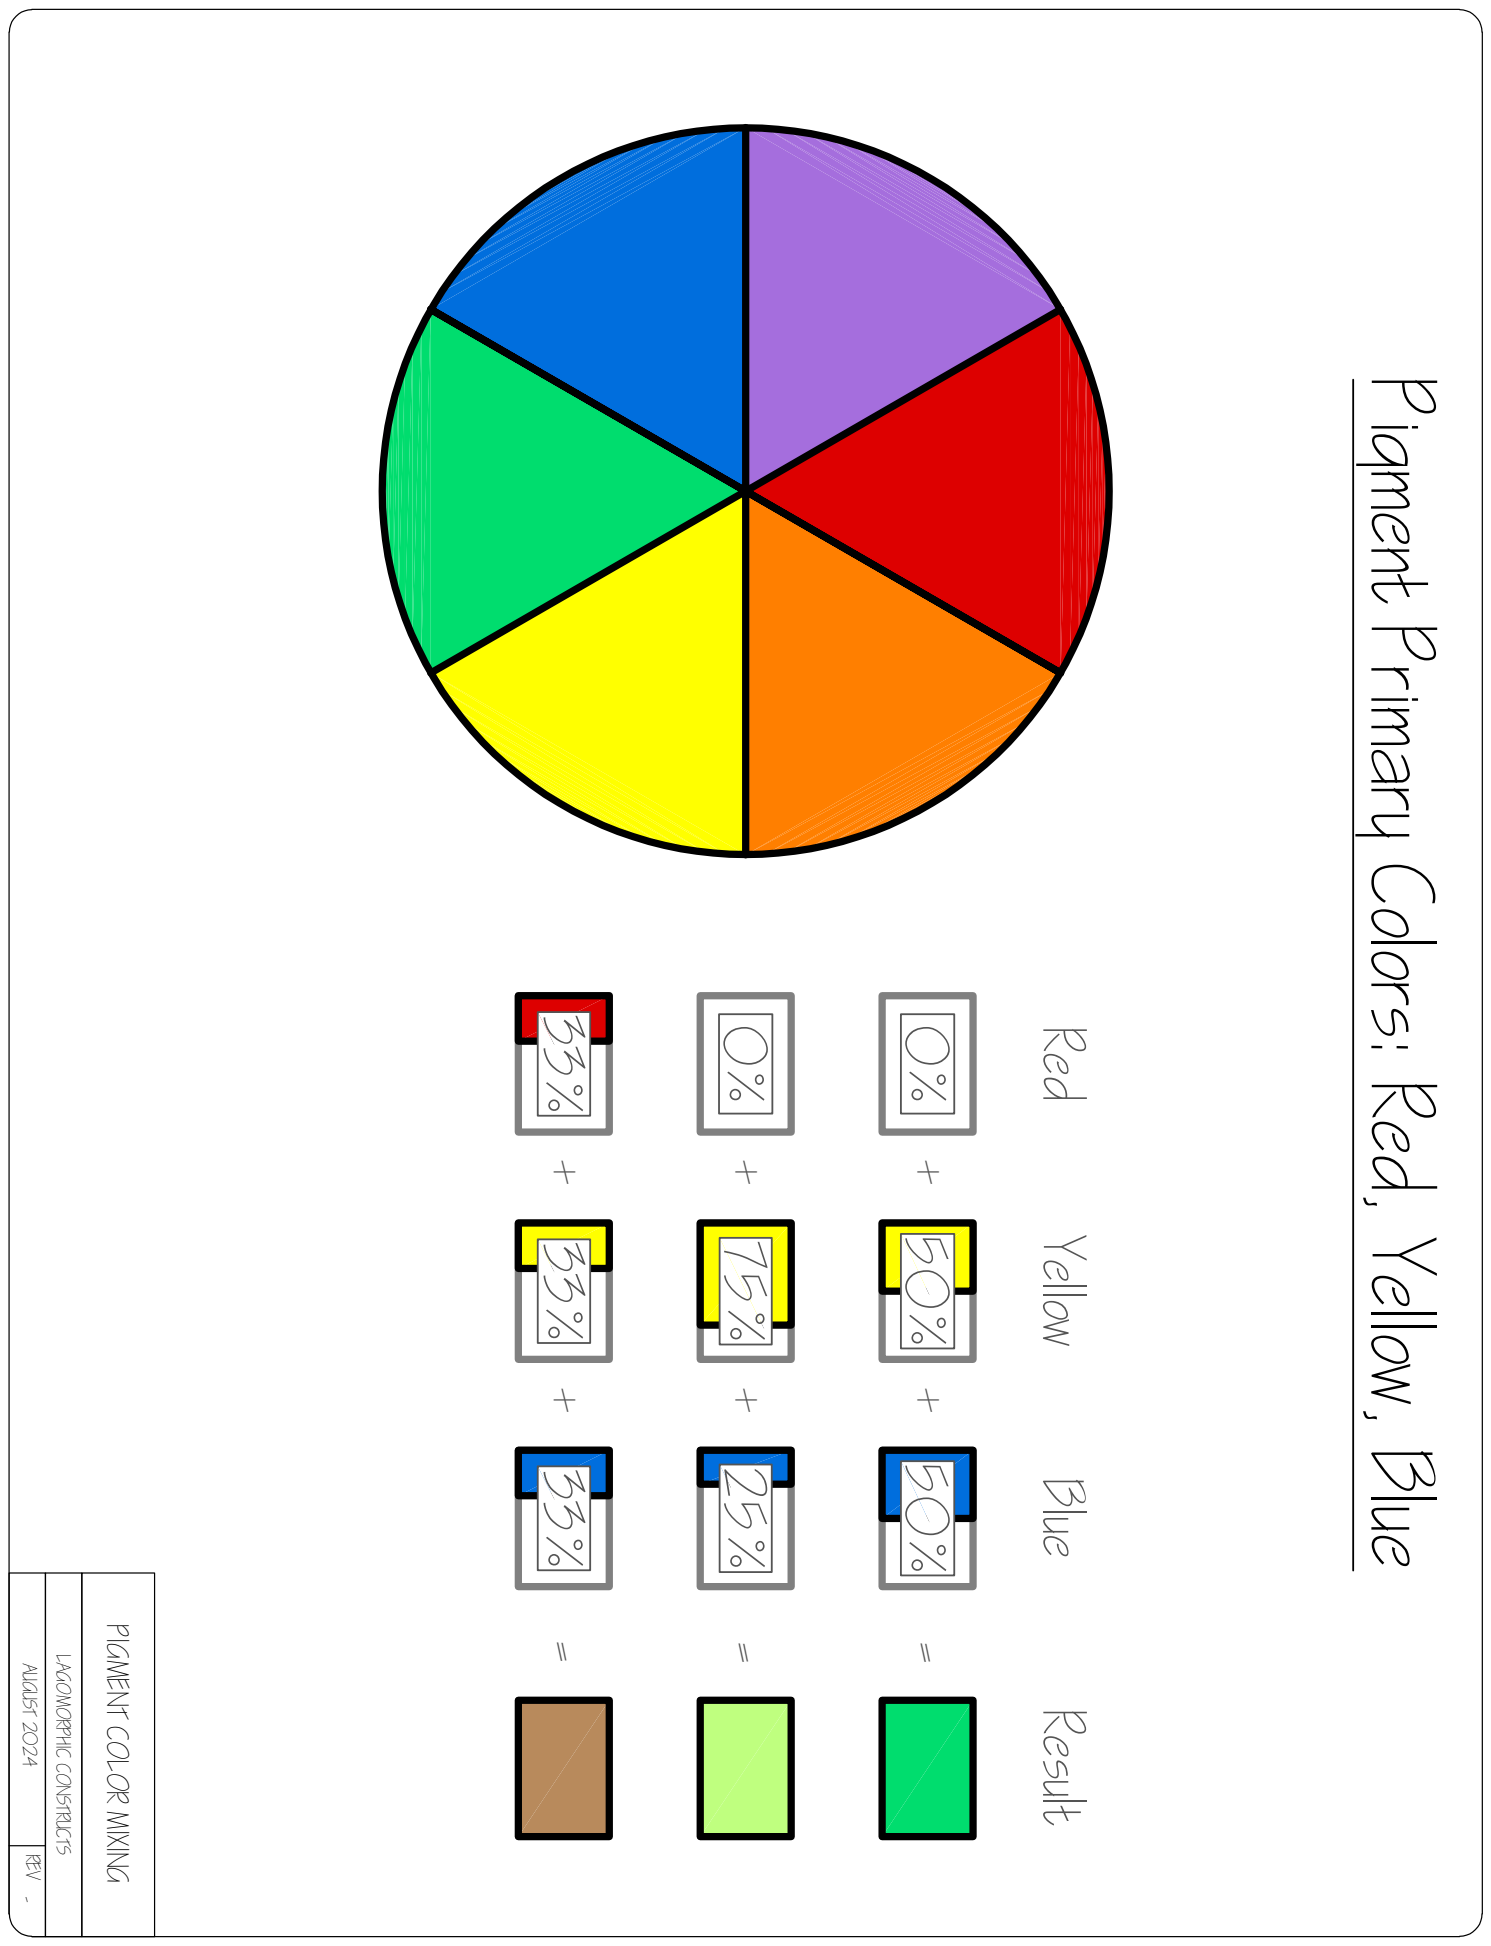
[picture p93: page 1]

REV LAGOMORPHIC CONSTRUCTS - AUGUST 2024 PIGMENT COLOR MIXING Pigment Primary Colors: Red, Yellow, Blue 0%Red Yellow Blue Result ++ ++ == + + = 0% 50% 25% 50% 75% 33% 33% 33%
