rebeccajr/color-clock/docs/slide-decks/2024-08-10__demo/2__light-color.pdf

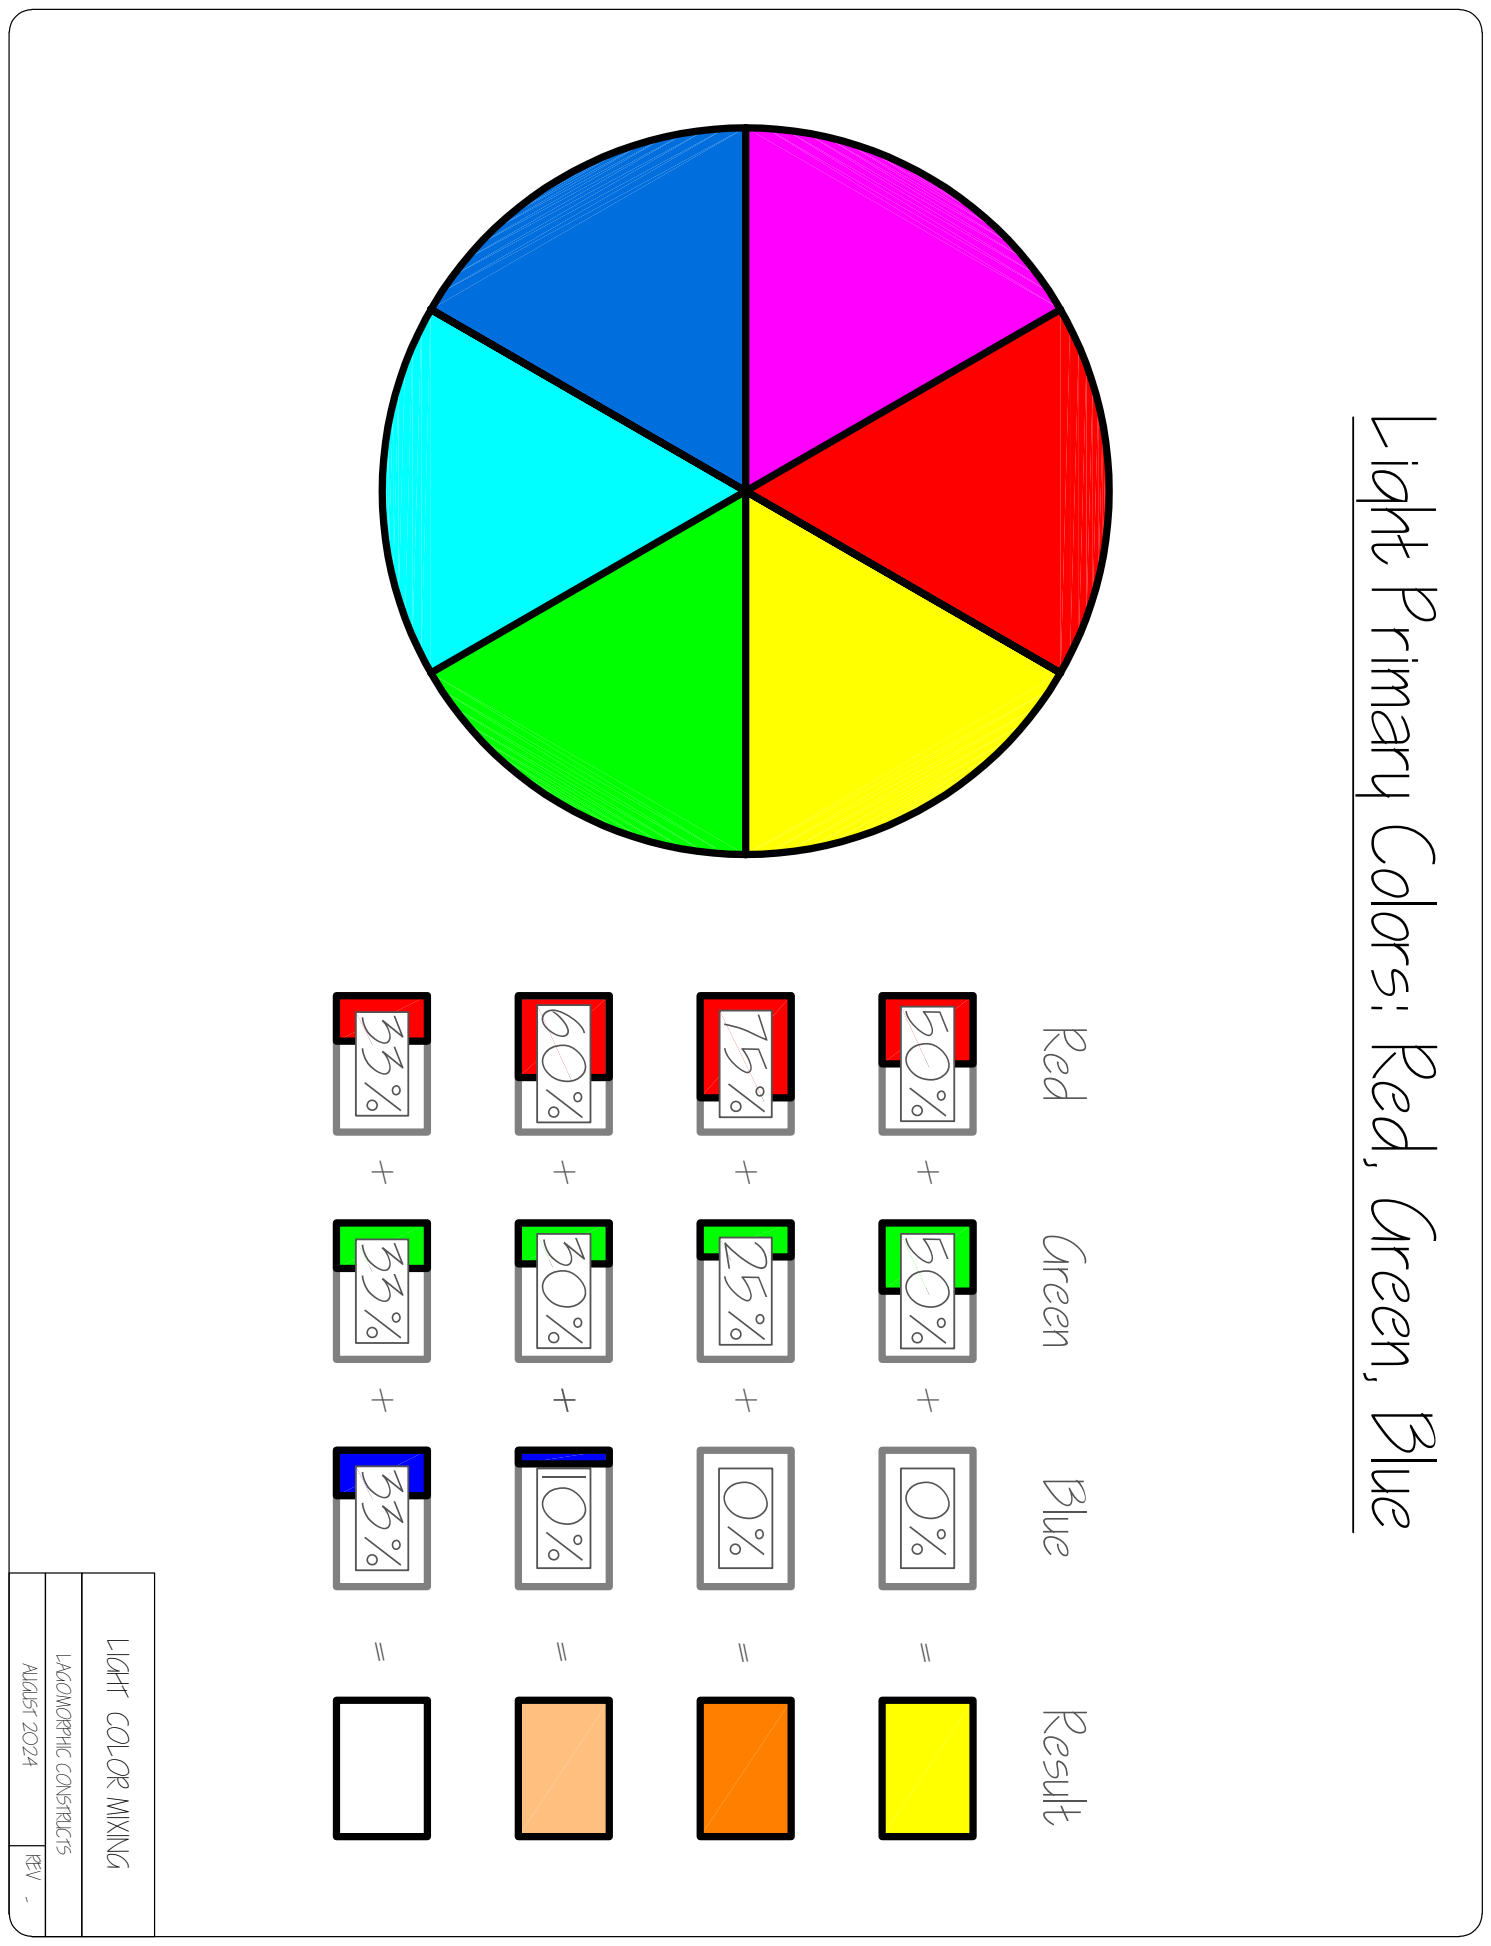
[picture p94: page 1]

REV LAGOMORPHIC CONSTRUCTS - AUGUST 2024 LIGHT COLOR MIXING Light Primary Colors: Red, Green, Blue Red Green Blue Result ++ ++ == 0%0% + + = + + = 25% 50% 33% 33% 33% 75% 50% + 10% 30% 60%
