rebeccajr/color-clock/docs/slide-decks/2024-08-10__demo/01__pigment-color.pdf

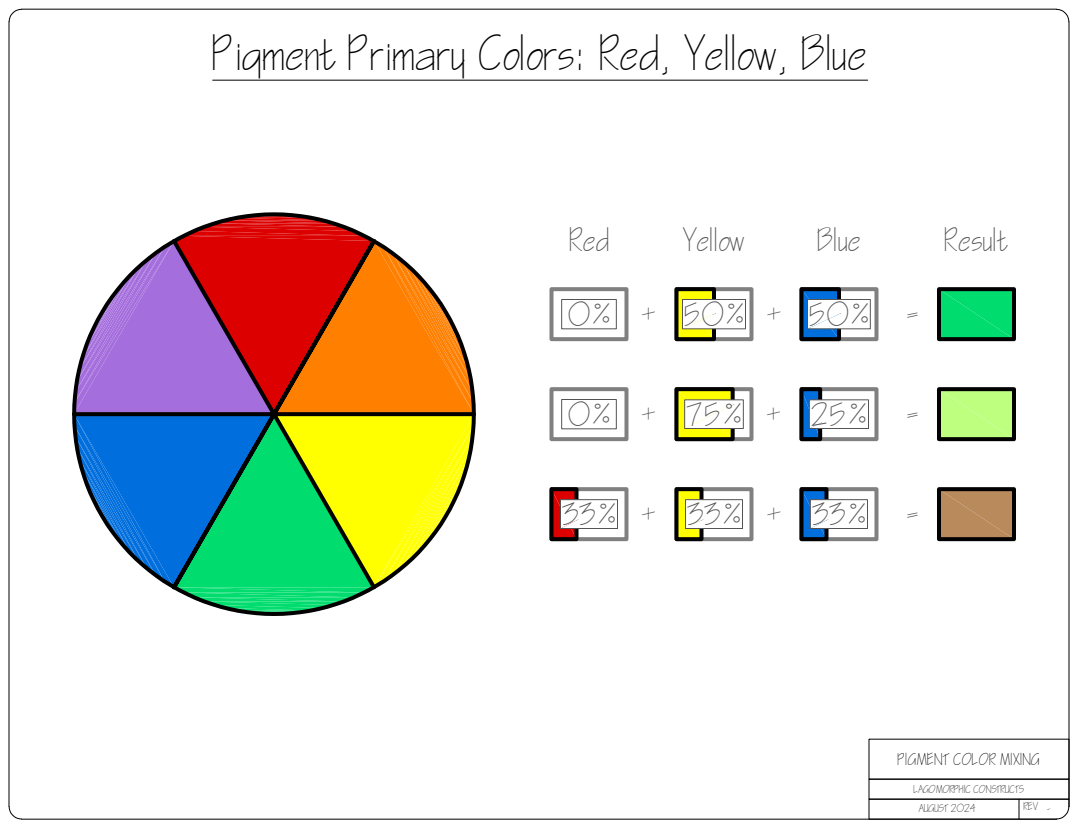
[picture p95: page 1]
REV LAGOMORPHIC CONSTRUCTS AUGUST 2024; - PIGMENT COLOR MIXING Pigment Primary Colors: Red, Yellow, Blue Red; Yellow; Blue; Result 0%
