rebeccajr/color-clock/docs/slide-decks/2024-08-10__demo/0a__title.pdf

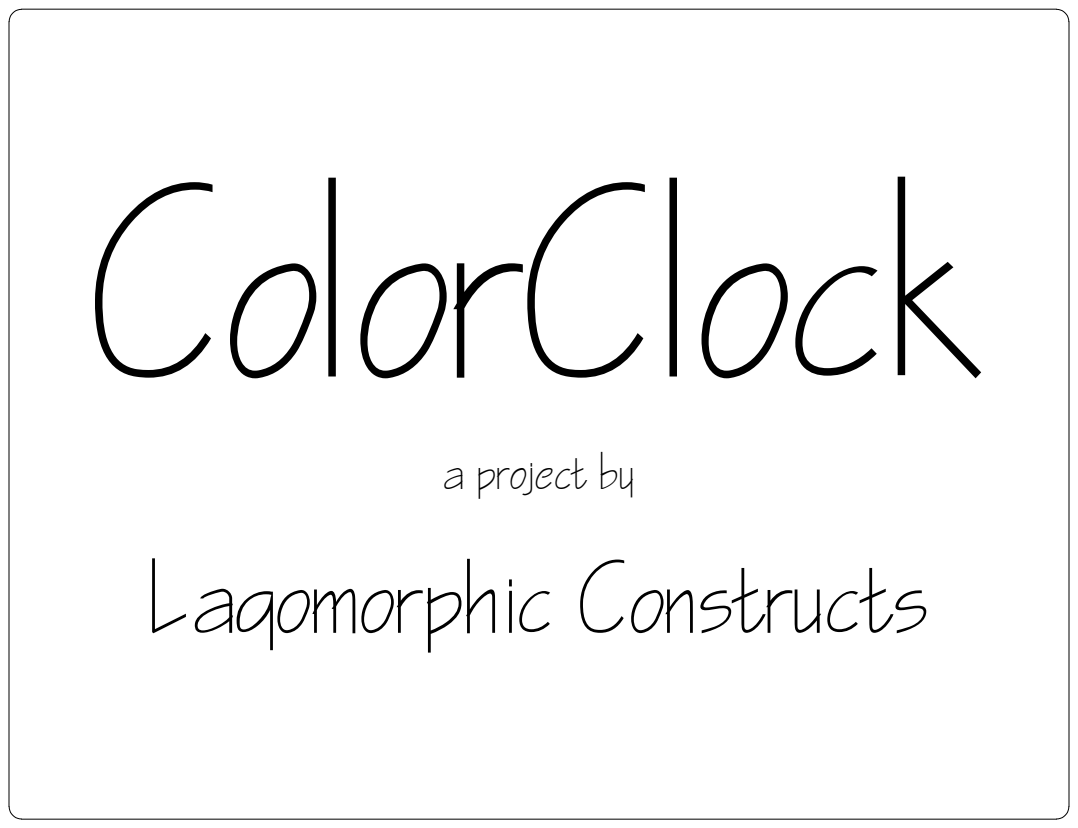
[picture p96: page 1]
a project by Lagomorphic Constructs
