rebeccajr/color-clock/docs/slide-decks/2024-08-10__demo/0b__title-intro.pdf

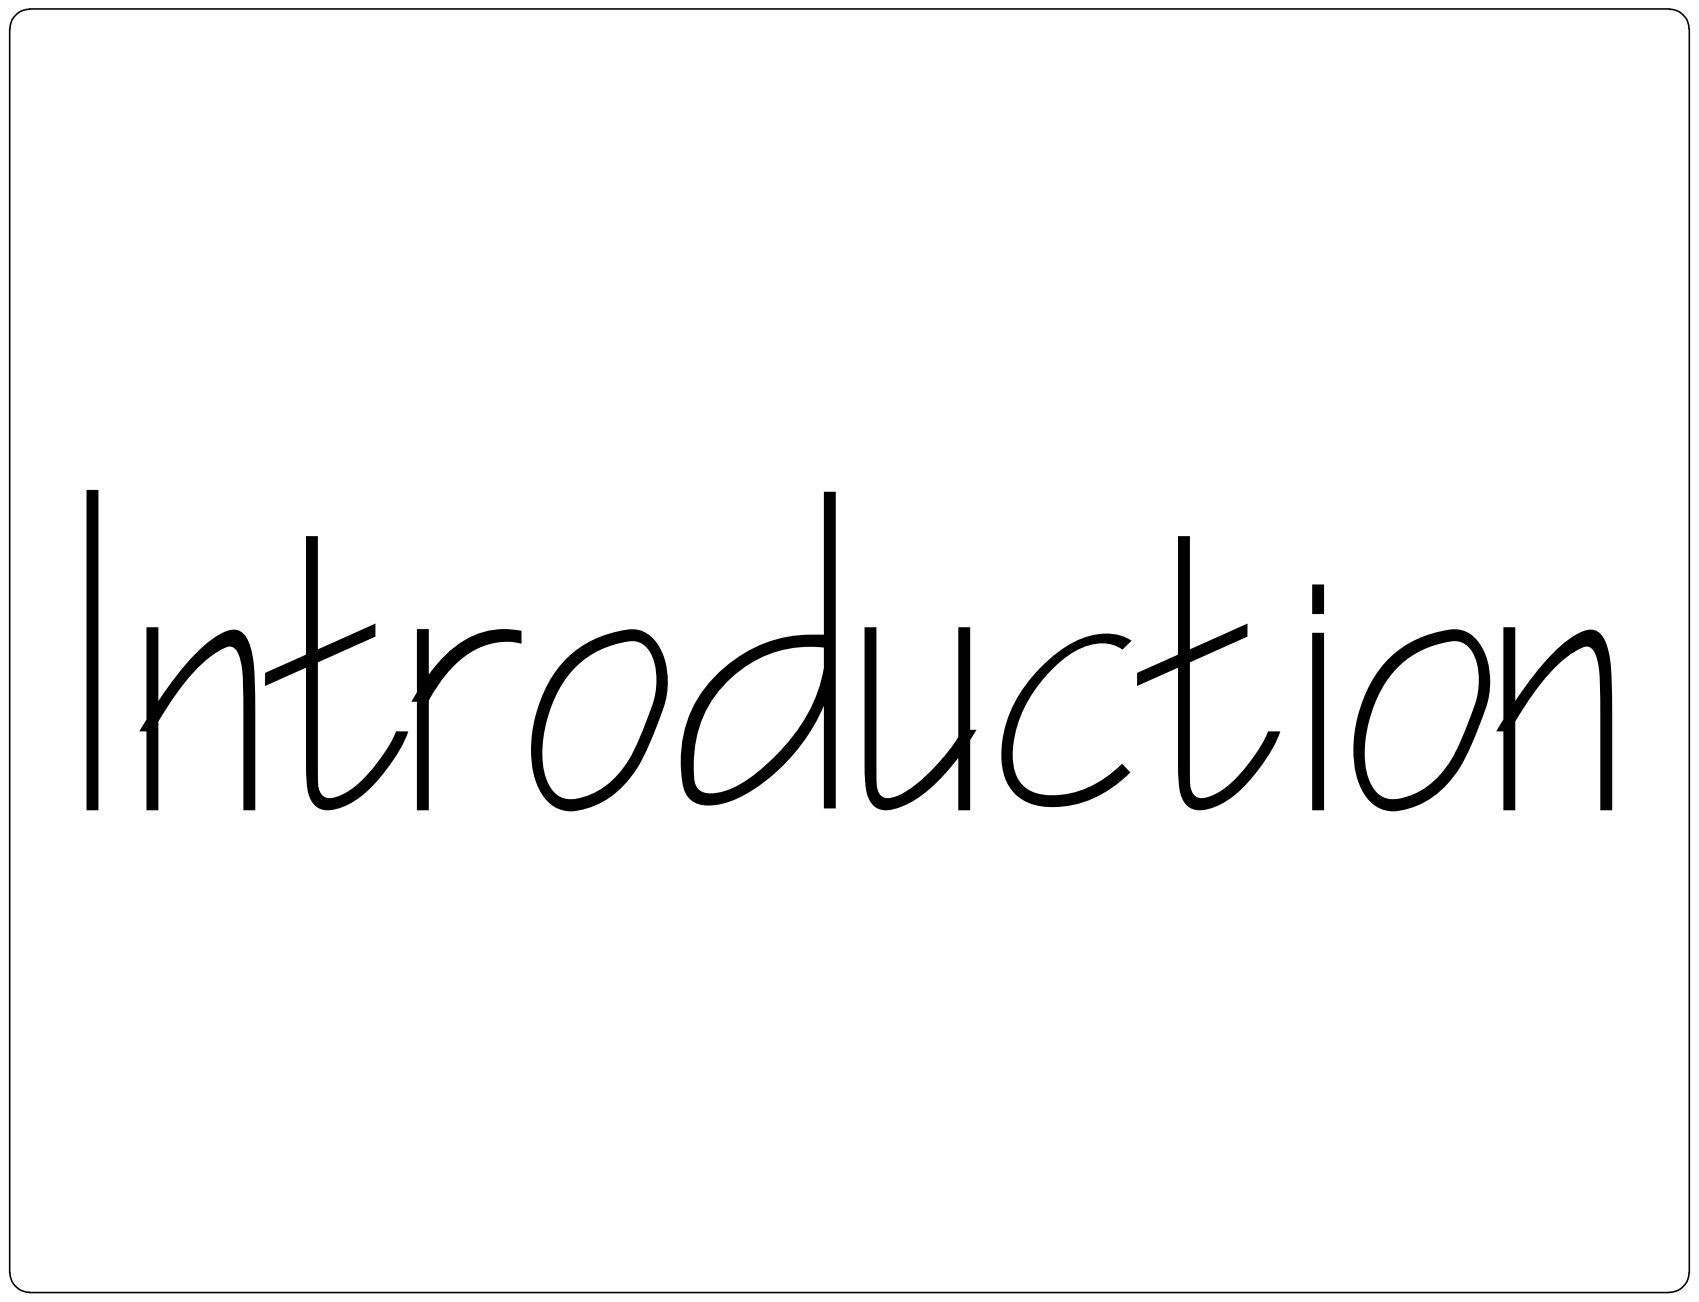
[picture p97: page 1]
