rebeccajr/color-clock/docs/slide-decks/2024-08-10__demo/0d__title-background.pdf

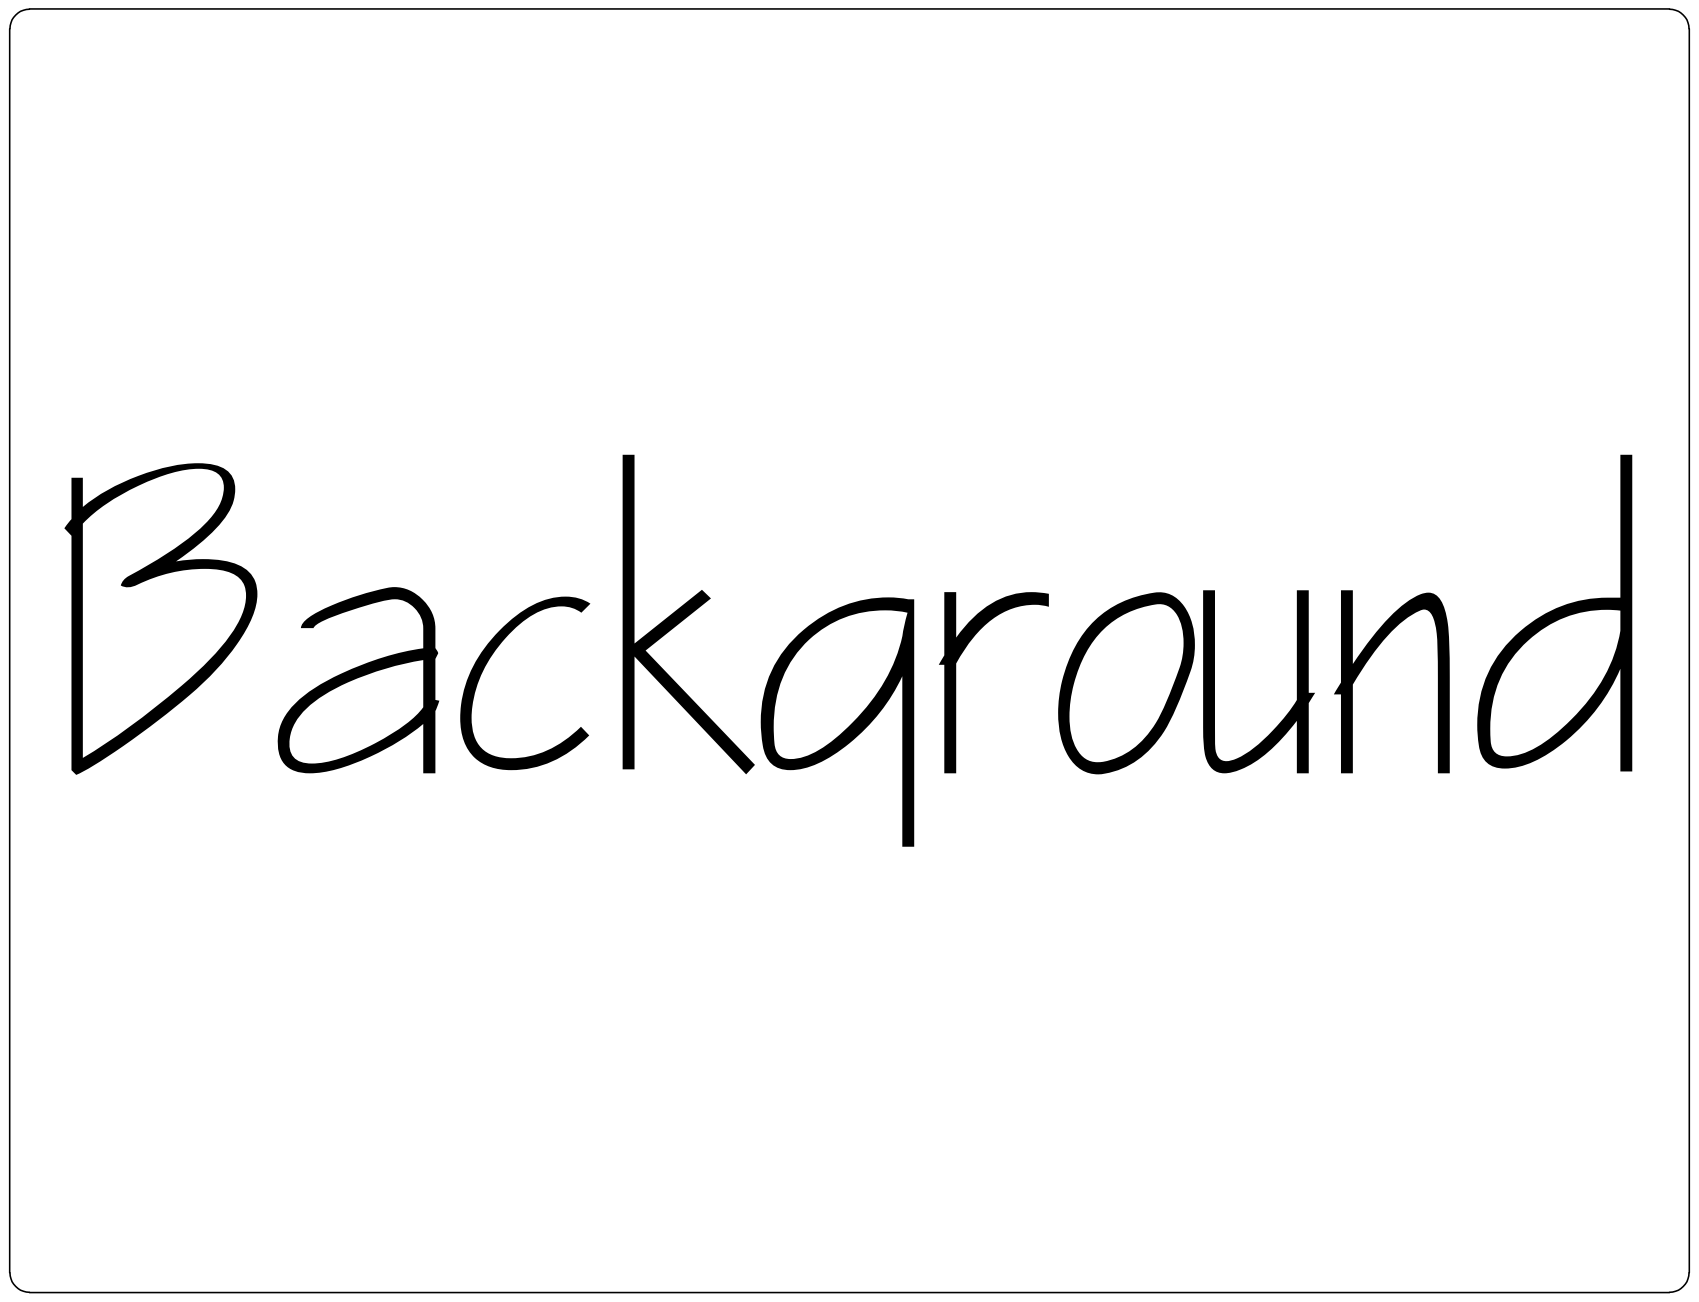
[picture p98: page 1]
