rebeccajr/color-clock/docs/slide-decks/2024-08-10__demo/11__title-participant.pdf

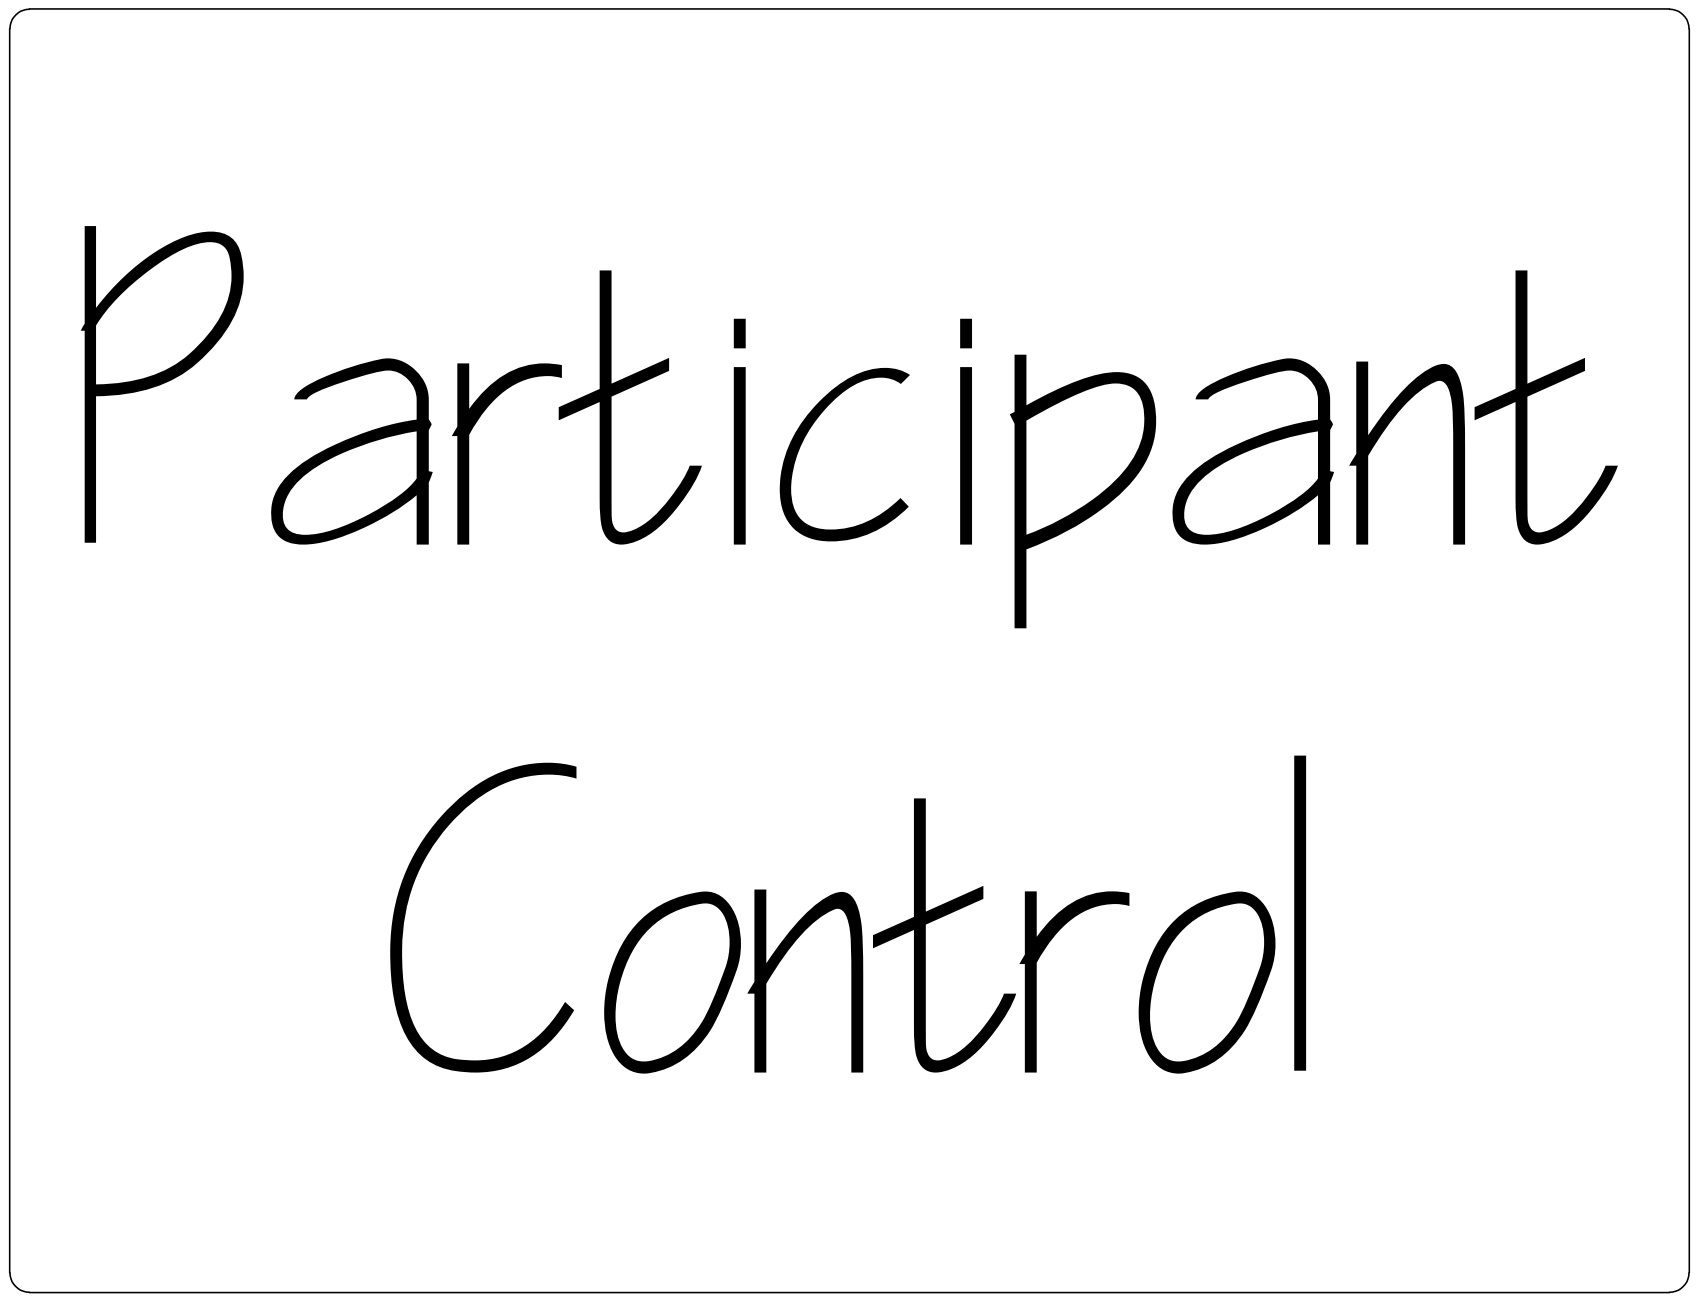
[picture p99: page 1]
