rebeccajr/color-clock/docs/slide-decks/2024-08-10__demo/12__title-structure.pdf

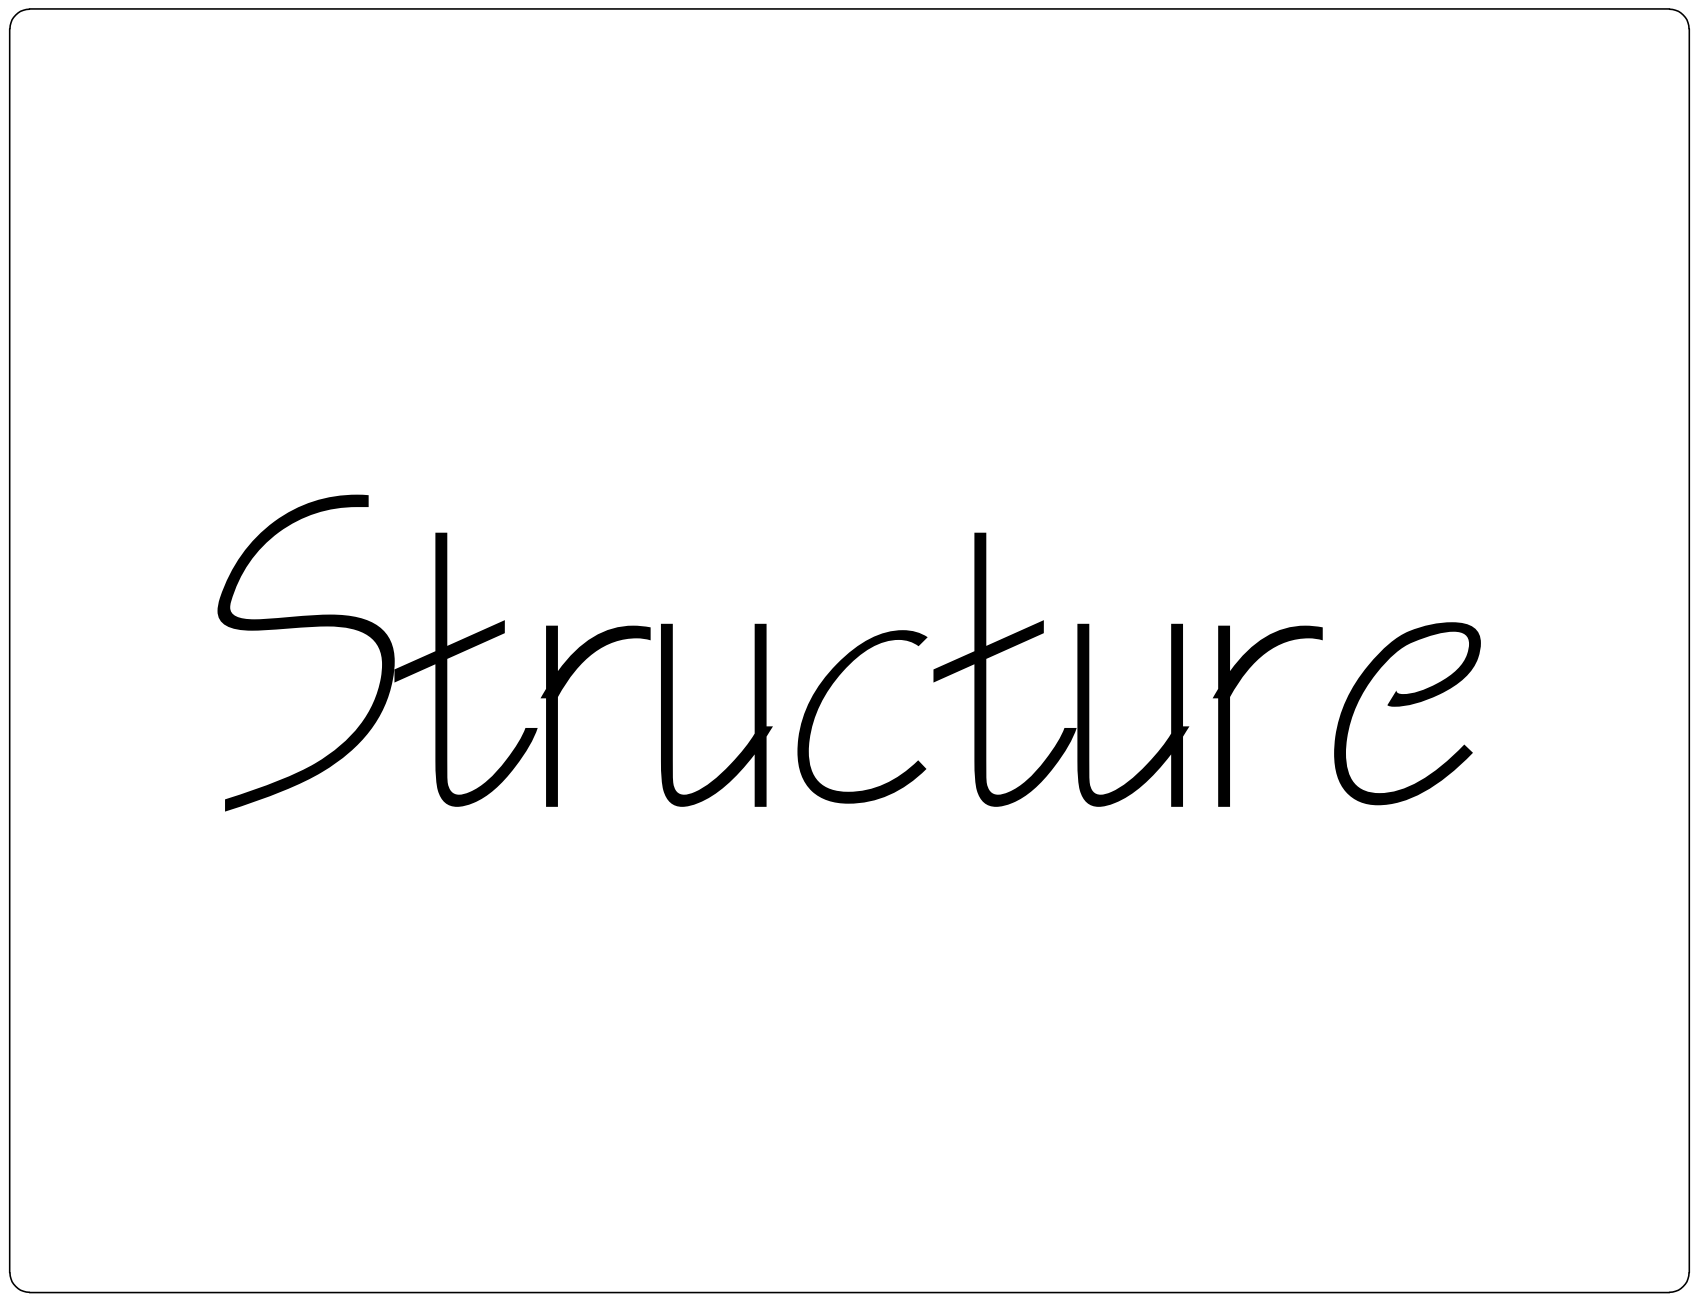
[picture p100: page 1]
