rebeccajr/color-clock/docs/slide-decks/2024-08-10__demo/13__title-end.pdf

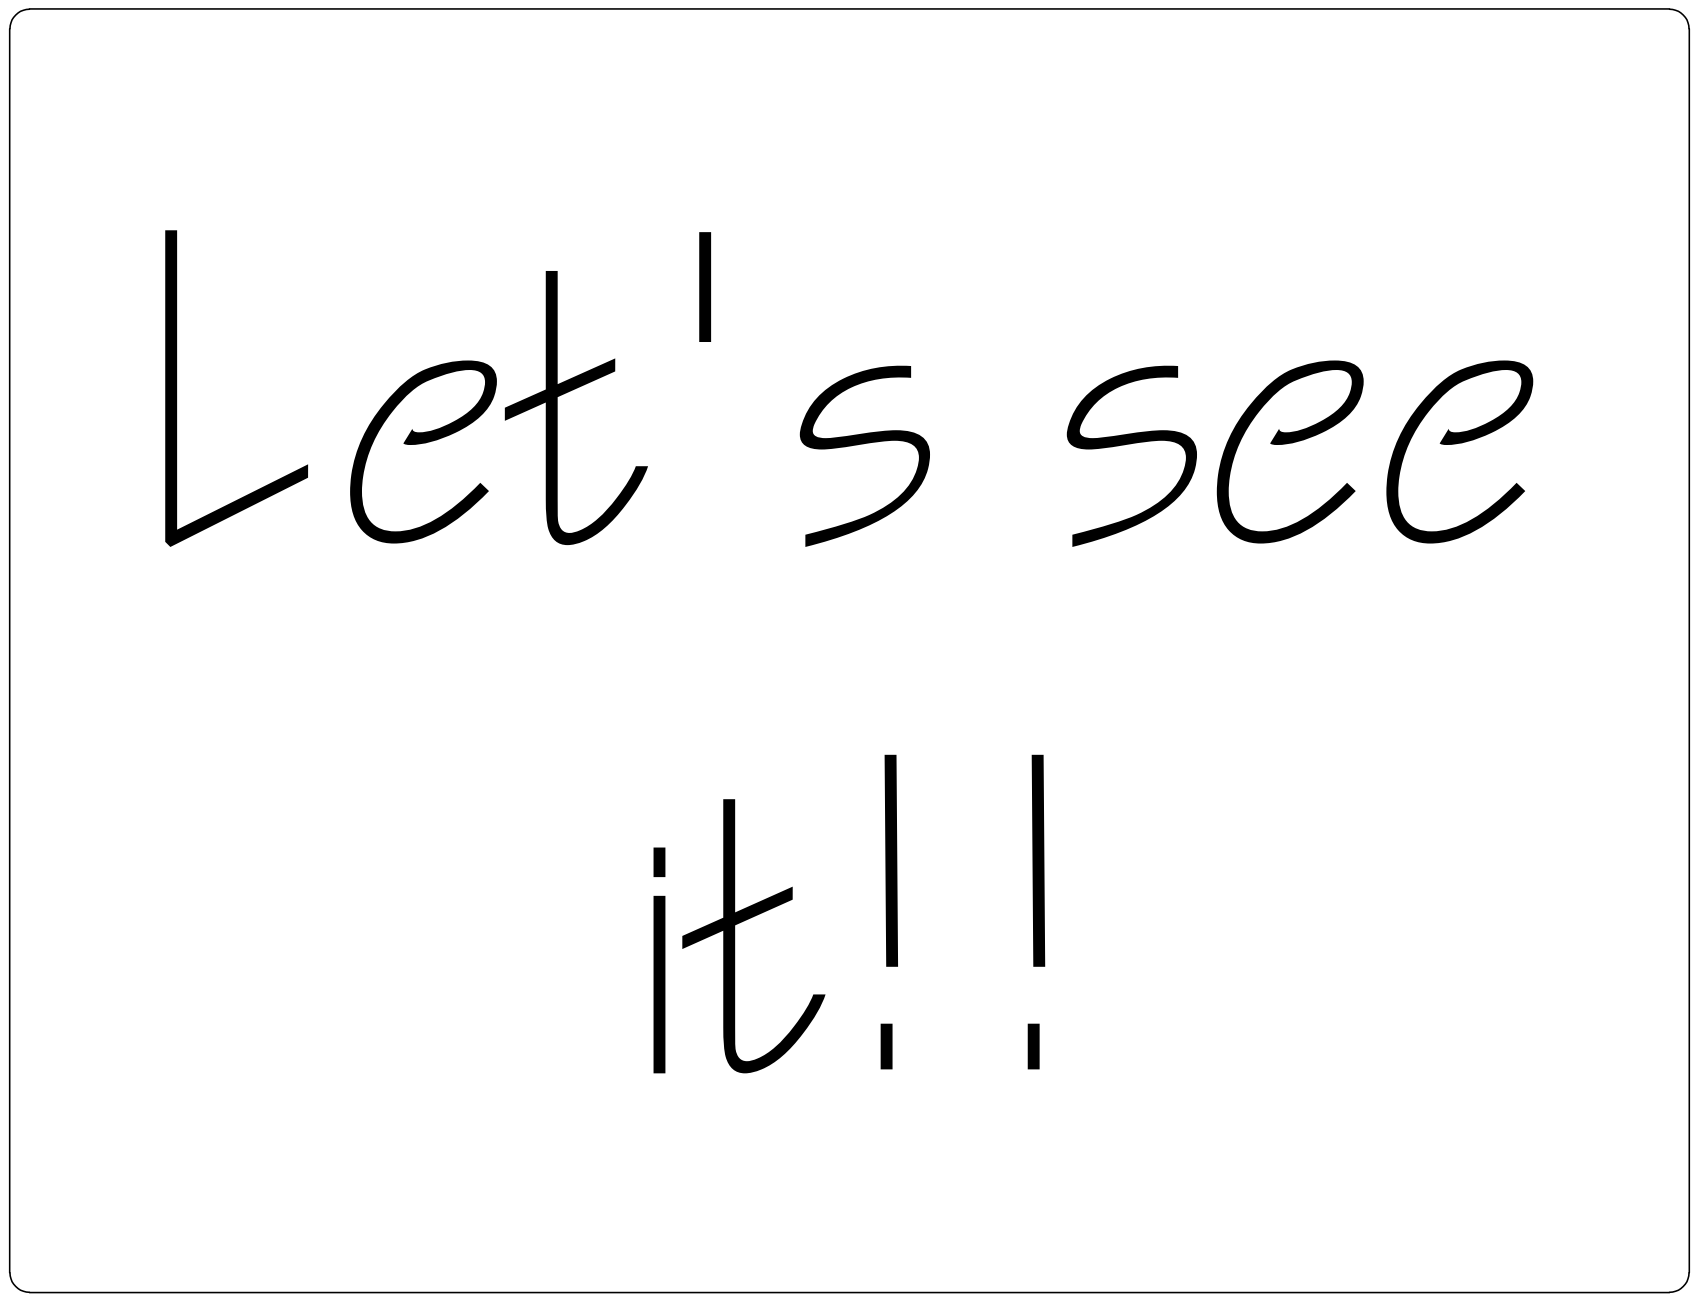
[picture p101: page 1]
