rebeccajr/color-clock/docs/slide-decks/2024-08-10__demo/5a__physical-structure-overall.pdf

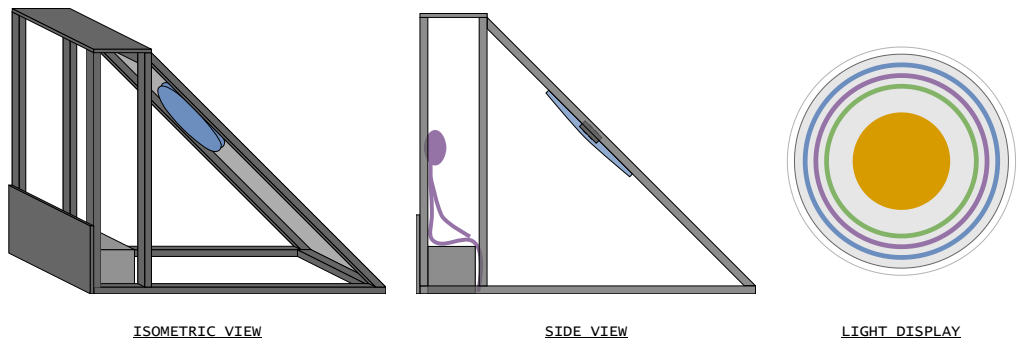
[picture p102: page 1]
ISOMETRIC VIEW; SIDE VIEW; LIGHT DISPLAY
