rebeccajr/color-clock/docs/imgs/acad/acrylic-sheet/acrylic-sheet-rev--__2024-06-06.pdf

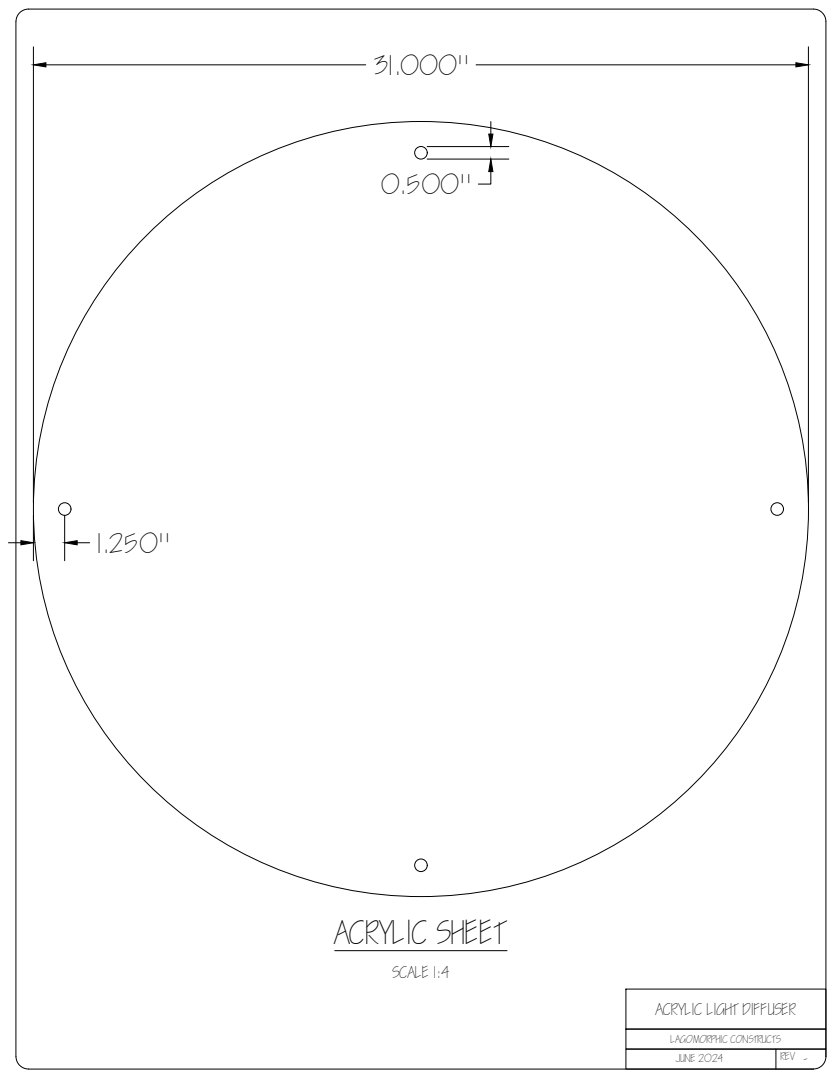
[picture p103: page 1]
LAGOMORPHIC CONSTRUCTS; JUNE 2024; - ACRYLIC SHEET; SCALE 1:4

ACRYLIC LIGHT DIFFUSER
