rebeccajr/color-clock/docs/imgs/acad/acrylic-sheet/acrylic-sheet-rev-a__2024-06-08.pdf

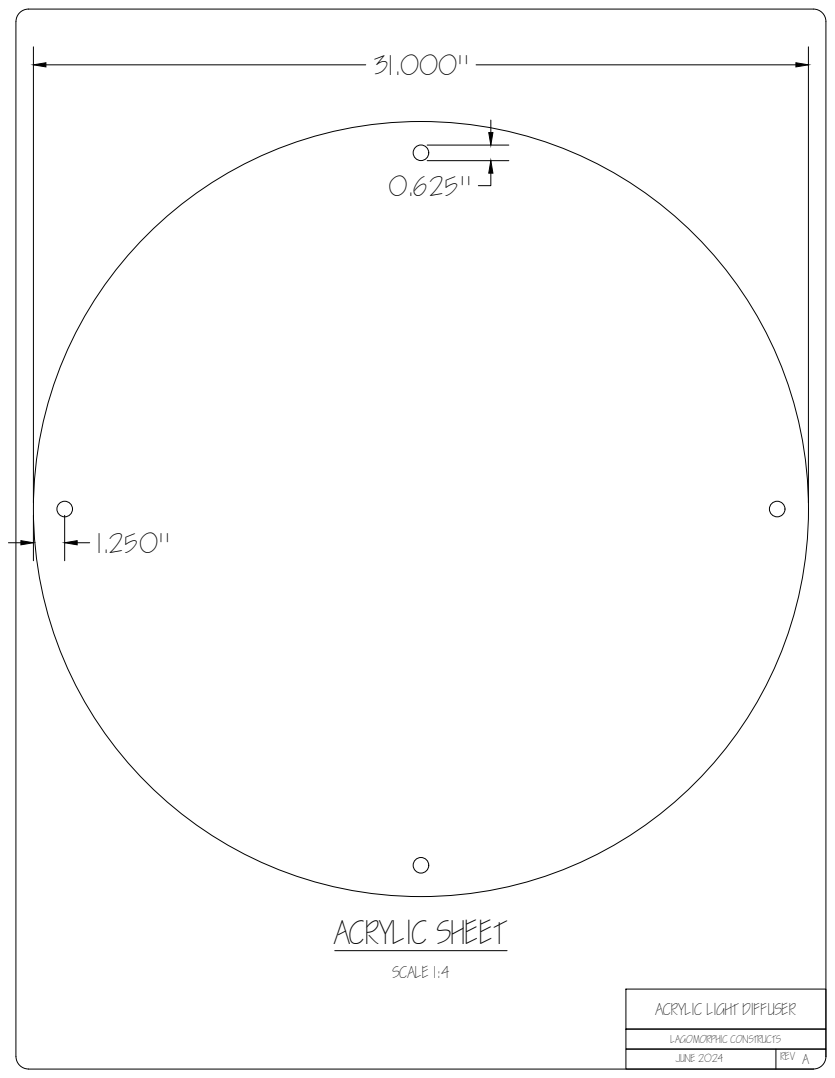
[picture p104: page 1]
LAGOMORPHIC CONSTRUCTS; JUNE 2024; ACRYLIC SHEET; SCALE 1:4

ACRYLIC LIGHT DIFFUSER
