rebeccajr/color-clock/sw/arduino/examples/pwm-out/pwm-out.ino

//______________________________________________________________________________
// This is an example for sending PWM output to the Arduino Nano ESP32.
// Note that this example doesn't work as intended and is still a wip.
//______________________________________________________________________________

#include <Arduino.h>
#include <Wire.h>

// the number of the LED pin
const int ledPin = D2;  // 16 corresponds to GPIO16

// setting PWM properties
const int freq = 5000;
const int ledChannel = 0;
const int resolution = 8;
 
void setup(){
  // configure LED PWM functionalitites
  ledcSetup(ledChannel, freq, resolution);
  
  // attach the channel to the GPIO to be controlled
  ledcAttachPin(ledPin, ledChannel);
}
 
void loop(){
  // increase the LED brightness
    ledcWrite(ledChannel, 255);
    delay(100);
    ledcWrite(ledChannel, 0);
    delay(100);
  /*
  for(int dutyCycle = 0; dutyCycle <= 255; dutyCycle++){   
    // changing the LED brightness with PWM
    ledcWrite(ledChannel, dutyCycle);
    delay(15);
  }

  // decrease the LED brightness
  for(int dutyCycle = 255; dutyCycle >= 0; dutyCycle--){
    // changing the LED brightness with PWM
    ledcWrite(ledChannel, dutyCycle);   
    delay(15);
  }
  */
}
