rebeccajr/color-clock/sw/arduino/examples/simple/simple-header.hpp

//______________________________________________________________________________
// This file is a simple header to be included in a test Arduino sketch.
//______________________________________________________________________________

class SimpleClass
{
  public:
    int variable;

  SimpleClass(){variable = 42;};
};
